ayumu-bekki/radio-terror/docs/navigator_decisions.md

# ナビゲーター設計 — 決定記録

`navigator_design.md` の設計判断の記録。**なぜそう決めたか**を実測値と
失敗の経緯込みで残してある。

- **現在有効な規範は [`adr.md`](adr.md)** に集約してある(N-\* の項目)。
  実装を変更するときはそちらを読む。ここは**根拠を確かめたいとき**に開く。
- ADR の各項目は「> 出典: NV 決定20」のようにこのファイルを指している。
- **覆った決定も削除しない**。「※ この決定は決定N で覆った」と追記して残す
  — なぜ一度そう決めたのかが分からなくなるため。
- 本文中の **§N は [`navigator_design.md`](navigator_design.md) の節**を指す
  (このファイルは元々そこの末尾にあった。2026-08-25 に分離した)。

> **この節は作業当時の記録**。当時存在したが**その後に採用を見送ったステージ**の
> 番号が出てくる(105/191/192/29x/39x)。現行のステージ一覧は
> `puzzle_stage_ideas.md` §2 を見ること。決定の中身自体は現在も有効。

## 決定記録

1. **キャラクター**: 4案(フクロウ/ヒバリ/アオサギ/ツグミ)を採用。
   ヒバリには「実は黒幕かもしれない」という含みを追加(§2.2。演出のみで
   ヒントの正確さは保つ)
2. **ツグミの音声**: エフェクト加工なし。素の中性声+スタイル指定のみ
3. **ヒントレベルの閾値**: ステージ経過時間を基本軸に質問回数・誤操作で前倒し。
   閾値はステージ予算に対する比率(**L2=25% / L3=50% / L4=75%**)で自動算出
   (実値は `scenario_design.md` §4.1)。比率0はそのレベルを無効にする指定で、
   ハードは `l4_pct = 0` として正解の直言を出さない
4. **正解の直言(L4)**: 残り時間ではなく**ステージ経過時間**で解禁し、
   ヒント段階(§3.2)の最終レベルとして統一
5. **コールサイン**: 採用するが常時フル形式にはしない。開始時・節目のみ名乗り、
   緊迫時はキャラごとの短縮形に崩す(§2.6)。
   ※ **この決定は決定107 で覆った**(2026-09-05)。「節目のみ」の指示により
   **ほぼ初回しか名乗らなくなった**ため、平時は毎回名乗る方針へ戻した。
6. **誤認識ポリシー**: 復唱確認+肯定待ちで担保(色名の日英併記はしない)。
   聞き返しは2回まで、以降ははい/いいえ形式に切り替え(§3.6)
7. **前倒しの制約**(実装時): 質問回数・誤操作による前倒しは、**無効化された
   レベルを飛び越えない**。ハードで誤操作してもL4(直言)には到達しない。
   また前倒しは経過時間による判定を下回らせない(§3.2)
8. **キャラクター知識の注入方法**(実装時): キャラシートはプロンプトの
   固定ブロック[B]として全文を渡し、口調・口癖・台詞例まで含める。
   短い要約では口調が安定しなかったため、場面別の台詞例を明記する方式にした(§3.3)
9. **ステージ知識の `procedure`**(実装時): 対話で誘導するステージ(101・103・202)
   向けに、ヒント指針とは別に「会話の進め方」を渡す項目を追加した
   (`scenario_design.md` §3.3)
10. **設定の外部ファイル化**(実装時): キャラクター定義とプロンプト固定ブロックを
    Goコードから **TOML** へ分離した(`navigator/`)。口調やプロンプトは実機で
    試しながら繰り返し調整する性質のもので、シナリオと同様に再ビルドなしで
    差し替えられる方が運用しやすいため。キャラクターは1人1ファイルとし、
    追加・差し替えをファイル操作で行えるようにした(§2・§3.3)
11. **表情タグの廃止**(実機確認時): 本文に `[calm]` のような角括弧タグを混ぜて
    TTS へ演技指示を渡していたが、**タグを含めると応答が不安定になる**ことが
    実測で判明した(通常2.6秒のところ、8回中2回が20秒超。最大21.7秒)。
    遅れたチャンクは radio-bridge 側で破棄され、ナビゲーターの音声が
    途中で途切れる原因になっていた。**ディレクターズノート方式**
    (プロンプト前置きの場面説明)へ変更(§4.1)。
    分割そのものは維持する — 実測で分割なしは発話開始が平均13.8秒
    (最大44.7秒)まで悪化し、遅延の外れ値は分割の有無に関係なく発生した

    **※ この決定は決定17で覆った。** 不安定さの原因はタグではなく
    一括受信だった(決定15)。**サンプル8回では両者を区別できなかった** —
    一括受信は入力と無関係に27%が10秒超になるため、
    「8回中2回」はタグ無しでも同程度に起きる頻度だった。
12. **分割送信をやめ、1パケットにまとめる**(実機確認時): 決定11では
    「分割そのものは維持」としたが、**逐次送信を取りやめた**。
    TTS の1チャンクが **58.97秒**かかった際、先に完成していた後続チャンクが
    1分近く滞留し、発話が丸ごと遅れる事象が出たため。
    分割送信は「先頭ができ次第すぐ流せる」が、裏返すと**1チャンクの遅延が
    発話全体を人質に取る**。全チャンクの PCM が揃ってから連結し、
    1回だけ Opus エンコードして1パケットで送る方式にした
    (`bridge_connection_design.md` §2 決定13)。
    **生成の並列化は維持**するので、待ち時間は「最も遅いチャンク」で決まる。
    決定11の実測(分割なしで平均13.8秒)は**逐次生成**での値であり、
    並列生成のまま送出だけまとめる今回の方式とは条件が異なる。
    レイテンシは増えるが、**出るときには必ず発話が揃っている**確実性を取った。

    **※ ここで残した「生成の並列化」も決定18で廃止した。** 発話が
    2文・60文字以内になり(決定14)、分割しても大半が1チャンクに
    収まるようになったため。
13. **API呼び出しのタイムアウト**(実機確認時): Transcribe / reply / TTS の
    各呼び出しに上限(`config.toml` で変更可)を設けた。
    従来は上流の ctx がプロセス終了まで生きており、**上限なく待っていた**。
    実測の正常値は Transcribe 2.8-3.1秒 / reply 1.1-1.2秒 / TTS 2〜4秒。
    無線は「無音のまま待たされる」のが最悪なので、待ち続けるより打ち切る。
    **TTS は 10秒・3回**(決定15でストリーミング化したため短く切れる)、
    Transcribe / reply は 20秒。
    併せて、10秒を超えた TTS 呼び出しは**プロンプト全文をログに残す**
    (`[gemini] TTS SLOW`)。原因追跡には入力が要るため。
    **打ち切りは発話全体の欠落を意味する**(決定16)ので、
    上限を短くする場合は必ず作り直しとセットにする。
14. **発話長の制限**(実機確認時): 出力ルールを「1〜3文」から
    **「2文以内・60文字以内」**へ厳しくし、雑談・回想で文を使わないよう明示した。
    実測で5文・69文字の発話が出ており、1発話が16〜19秒に達して無線を塞いでいた。
    原因は**キャラクター定義の台詞例が長かった**こと — フクロウの
    【ヒントの味付け】の例文が2文構成で、生成AIがその長さをそのまま写していた。
    プロンプトの数値だけでなく**例文の長さを短くする**ことが実効的なので、
    全キャラクターの台詞例を2文以内に揃え、「応答」の例を追加した。
    サーバー側でも文字数をログに出し、上限超過は WARN を残す
    (`navigatorMaxRunes`。プロンプトの数値と一致することをテストで担保)
15. **TTS の応答をストリーミングで受け取る**(実機確認時): 遅延の原因は
    **一括応答の待ち受け**だった。`GenerateContent` から
    `GenerateContentStream` に変えただけで**外れ値が消えた**。

    同一プロンプト15回の実測(`tts_latency_probe_test.go`):

    | 受信方式 | 中央値 | 最大 | 10秒超 |
    |---|---|---|---|
    | 一括 `GenerateContent` | 4.16秒 | **56.51秒** | **4回 (27%)** |
    | ストリーミング `GenerateContentStream` | 3.22秒 | **3.75秒** | **0回** |

    切り分けの経緯 — 当初は入力内容を疑った(決定11で角括弧タグが原因と
    結論づけた前例があるため)が、**実測で否定された**:
    - **入力内容は無関係**: 本番で19.01秒かかった本文を10回試すと 2.39〜3.59秒。
      逆に最も無害な平易文で46.96秒が出た。「どうぞ」の有無・三点リーダ・
      命令形・前置きの有無、いずれも差なし
    - **並行数も無関係**: 同時1本/2本/3本で中央値・最大値とも変わらず、外れ値ゼロ
    - **出力量とも無関係**: 遅い回も音声は5秒前後で一定。`MaxOutputTokens` は
      このモデルが受け付けない(30回中30回 400 INVALID_ARGUMENT)

    先頭チャンクは中央値0.79秒で届くが、**順次無線へ流すことはしない** —
    決定12で捨てた分割送信と同じ構造に戻るため。全チャンクを連結してから
    1つの Ogg にする。
16. **TTS が1チャンクでも欠けたら発話ごと見送る**(実機確認時): 以前は
    成功したチャンクだけ繋いで送っていたが、実運用で**尻切れの発話**が
    無線に出た(「私は見ている。」だけが流れ、続く指示が消えた)。
    不完全な指示は誤解を生むので、黙る方を選ぶ。
    ナビゲーターがその回だけ無反応になるため、WARN をログに残し、
    TTS の失敗をマネージャー画面の API 状況にも反映する。
    決定15で外れ値が消えたので発動機会はほぼ無いが、
    **タイムアウトを短くする判断はこの挙動とセット**で考える。
17. **表情タグを復活させる**(実機確認時): 決定11で廃止したタグを戻した。
    廃止理由「タグを含めると応答が不安定になる」が**実測で否定された**ため —
    不安定さの正体は一括受信で(決定15)、ストリーミング受信では
    タグ有無で差が無い(各10回、全条件で10秒超ゼロ、中央値2.87〜3.32秒)。
    読み上げ事故(「リリーブド」と発音する)も起きなかった。

    聴き比べの結果 **ノート+タグ > ノート単独 > タグ単独** だったので、
    ディレクターズノートは残したまま**併用**する(§4.1)。

    安全策として**語彙を6つに限定**し(`allowedTTSTags`)、一覧外のタグは
    サーバー側で落とす。プロンプトで指示しても生成AIが従うとは限らず、
    未知の語は演技として解釈されずそのまま読み上げられるため。
    実測では32発話すべてにタグが付き、**一覧外の語はゼロ**だった。
    キャラクター定義の台詞例にもタグを入れると出力が安定する
    (決定14と同じ理由 — 例文が実際の出力を決める)。
18. **チャンク分割をやめる**(実機確認時): 発話を句点で分割する処理
    (`splitAnswerForTTS`)を廃止し、**発話全文を1回の TTS 呼び出し**にした。

    分割の目的は段階的に失われていた:
    - 「できた順に送って最初の音を早く出す」→ 決定12で順次送出をやめた
    - 「生成の並列化」→ 決定14で発話が2文・60文字以内になり、
      大半が1チャンクに収まるようになった

    残ったのは**害だけ**だった。末尾の「どうぞ」(3文字)が必ず単独チャンクに
    切り出され、3文字の生成に2〜3秒のAPI往復を費やしていた
    (`mergeShortChunks` が先頭要素を結合対象にしないため)。
    失敗する機会も1つ増える。

    廃止に伴い `split.go` / `split_test.go` を削除し、
    `speakTTSChunks` を `speakTTS` (単一テキスト版) に置き換えた。
    ストリーミング受信で届く音声片の連結は TTS クライアント側に残っている
    (`tts.go` の `generateOnce`)。
19. **正解には「今は言うな」を併記する**(実機確認時): L3 のときに
    ナビゲーターが「次は緑色の線を切ってください」と**正解の色名を直言**した。
    プロンプトは「正解(あなただけが知っている): …緑色の線を切ること」を
    渡した上で、離れた位置のヒントポリシーで「言うな」と指示する構造だった。
    **答えを目の前に置いて言うなと指示しても引きずられる** —
    実際の発話は `answer` の文をほぼそのままなぞっていた。

    正解を渡す方針(§3.1)は維持し、**正解と同じ行に禁止を併記**する形にした。
    L4 未満では正解行の直後に「⚠ この正解をそのまま口に出してはいけません。
    現在は L<n> です」を付ける。実測で**色漏れ 0/24**(4キャラ×L1-L3×2種の正解色)。

    併せて 101 の進め方を「**プレイヤーに色を報告させてから指示する**」形に
    変えた。101 は正解の色だけが点灯するため、`hint_l3` の
    「点灯しているランプと同じ色」という言い換えが**実質色名と等価**で、
    区別が曖昧だった。ナビゲーターが先に色名を言うとプレイヤーは装置を見ずに
    従うだけになり、チュートリアルとしての意味も薄れる。
    修正後は全キャラが「光っているランプの色を教えろ」と尋ねる形になった。

    **※ その後、尋ねる形はやめた**(決定23)。色名を言わない原則は維持したまま、
    「光っているランプと同じ色の線を切れ」と直接指示する形にしている。
20. **`answer` は「読み上げる文」ではなく「照合の材料」として書く**:
    決定19 で「正解を目の前に置くとなぞられる」ことが分かっている。
    したがって `answer` に**そのまま読み上げると成立してしまう文**を
    書いてはいけない。205 速さくらべの初稿は
    「プレイヤーが白色を報告してきたら復唱して切らせてよい」と書いており、
    L1-L2 でなぞられると「白色ですか?」とナビゲーター側から色名を出しかねない
    形だった。**「プレイヤーの報告が白色と一致するかを照合に使うこと」**と、
    判定の指示として書き直した。

    合わせて **L4 でも色名を言えないステージがある**ことに対応した。
    203 ブループリントは色を言うとシートを読む工程が消えて謎が成立しないため、
    L4 でも端子番号しか言えない。L4 のプロンプトは `answer` を
    「そのまま伝えてください」と埋め込むため、`answer` 側に
    「L4 であっても色名は言わない」と書いたうえで、L4 ブロックにも
    **「但し書きがある場合はそれが優先。但し書き自体は読み上げない」**を
    追記した。回帰は `TestL4RespectsStageLevelRestriction` と
    `TestHintPolicyBelowL4NeverEmbedsAnswer` が押さえている。

21. **意味の通らない報告は復唱せず聞き返す**(実プレイで発覚):
    音声認識が「ダイヤルを0に」→「ダイヤルを**音量**に」、
    「3に合わせました」→「**レディニュー**」のように誤変換したとき、
    ナビゲーターが「音量ですね、了解です!」「レディニュー、オッケーです!」と
    **そのまま復唱して先へ進んでいた**。プレイヤーは誤りが伝わったことに
    気づけず、実際の位置とナビゲーターの認識がずれたまま進行する。

    原因は §3.4 のルールの優先順位が曖昧だったこと。「報告は復唱して確認」と
    「聞き取れない場合は聞き返す」が併記されており、生成AIは前者を選んでいた。
    **「その場面で成立しない報告(色でも数字でもない語)は聞き取れなかった
    ものとして扱い、復唱せずに聞き返す」**を明示的に追加した。

    実プレイのログでは、ダイヤル位置の報告が全4回中2回誤変換されていた。
    無線 + 特小の音質では日常的に起きるため、聞き返しは例外処理ではなく
    **通常運転**として設計する。

22. **装置を見ても分からない情報は L1 で伝える**(実プレイで発覚):
    192 シグナルで、ナビゲーターが「3つのボタンを決まった順番で押せ」と
    言うだけで**色を一切教えず**、プレイヤーが「順番がよくわからないんですけど」と
    尋ねる往復が続いた。開始から約1分、押す色が伝わらなかった。

    原因は `hint_l1` が「ボタンを決まった順番で押す必要があることを伝える」と
    書かれていたこと。ボタンの並びは**装置に一切現れず、ナビゲーターしか
    知らない**ため、伏せるとプレイヤーは観察でも推理でもたどり着けない。
    「段階的に明かす」は**推理できる情報**に対してのみ意味を持つ。

    同じ欠陥が 201 復唱・393 二重復唱 (ボタン列)、206 綱渡り
    (危険なダイヤル位置) にもあった。206 綱渡り は知らずに踏むと**即爆発**するため、
    伏せるのは謎ではなく事故になる (`procedure` は先に警告する前提で
    書かれており、L1 と矛盾していた)。

    **ヒント段階で調整するのは「一度に何色まで言うか」であって、
    言うか言わないかではない。** 102 は L1 で1色目、L2 で残りを1色ずつ、
    L3 で通し読み。201/393 は L1 で列を読み上げる (393 二重復唱 の2周目は
    「覚えていられるか」が謎なので伏せたまま)。206 綱渡り は L1 で危険位置を警告する。

    あわせて `HintPolicyText` の共通文に**「指針が優先」**を明記した。
    「レベルを超えて色や番号を直言しない」という一般則だけがあると、
    生成AIはステージ側の指針より一般則を選んでしまう。
    回帰は `TestUnobservableInfoInProcedure` が押さえている。

23. **101 の手順を短縮する**(実プレイで発覚): チュートリアルに
    **約3分半**かかっていた。原因は2つ。

    **(a) 経由が2つあった。** `0 → 3 → 5 → 2` と4手順を踏ませており、
    1手順ごとに無線の往復が発生する(音声認識の失敗で聞き直す回もある)。
    経由を増やしても「報告して指示を受ける」という学びは変わらないので、
    `via2` を廃止して `0 → via1 → final_rotary` の3手順にした。
    あわせて `final_rotary` から 0 を除外した — 「0に戻す → 経由 → 0」と
    出発点へ戻るだけの往復になるため(抽選の15%で発生していた)。

    **(b) 最後に色を報告させていた。** ダイヤルが合ったあとで
    「光っているランプは何色か」→(報告)→「その色の線を切れ」と
    **1往復増やして**いた。決定19 で入れた形だが、実プレイで見ると
    最後の確認が冗長だった。**やることを最初にまとめて伝え**
    (「ダイヤルを合わせてから、光っているランプと同じ色の線を切る」)、
    ダイヤルが合ったら「光っているランプと同じ色の線を切れ」と
    そのまま指示する形へ変更した。

    ゴールを先に示すとプレイヤーはダイヤル操作中に自分でランプを見て
    準備できるため、**装置を見る**というチュートリアルの目的は保たれる。
    色名を言わない原則(決定19)も維持している。
    回帰は `TestTutorialStageNeverNamesCutColor` が押さえている。

24. **具体的な数字の指示を演出説明より優先する**(実プレイで発覚):
    決定23 で 101 の `procedure` に「最初にゴールを伝える」を足したところ、
    第一声が「まずダイヤルを回し、光っているランプと同じ色の線を切れ」となり、
    **どこへ合わせるかの数字が消えた**(46文字)。

    原因は出力ルールの**2文・60文字以内**。ゴールの説明を前に置くと、
    生成AIはその範囲に収めるために**具体的な数字を落とす**。
    説明と指示が競合したとき、削られるのは指示のほうだった。

    `hint_l1` / `procedure` を「**必ず数字で位置を言う。ゴールの説明で数字が
    押し出されるくらいなら数字だけ言う**」と優先順位を明示する書き方に変えた。
    短い発話に複数の要素を詰めさせるときは、**何を先に削ってよいか**まで
    指針に書く必要がある。回帰は `TestTutorialGivesConcreteDialPositions`。

25. **ディレクターズノートに場面を書かない**(実運用で発覚):
    TTS が生成した音声の**先頭に、ログに無い「プレイヤーの応答」らしき音声**が
    混入した。原因は前置きの書き方 — 「プレイヤーの報告に応じる場面。」のように
    **会話の状況**を書いていた。

    TTS は音声専用エンジンではなく**生成モデル**なので、場面を説明されると
    その場面全体を演じようとし、**応じる相手の発話まで自分で作って先に読み上げる**。
    「次のセリフを読み上げてください」で本文を限定していても、前置きが
    台本指示に見えるため効かない。

    ノートを**読み方の指定だけ**に書き換えた
    (「プレイヤーの報告に応じる場面。事務的すぎず、自然な受け答えで。」→
    「事務的すぎない、自然な受け答えの調子で。」)。
    「場面」「プレイヤー」「相手」「直後」「瞬間」といった状況を示す語は使わない。
    回帰は `TestDirectorNotesDescribeDeliveryOnly` が押さえている。

    タグが「リリーブド」と読み上げられた事故(決定11)と同じ構図で、
    **本文以外の要素を音声化してしまう**傾向はこのモデルで繰り返し起きている。

26. **ステージ知識が無いときは操作を促させない**(実運用で発覚):
    解除成功の直後に、ナビゲーターが
    **「あと60秒!もう一本、赤の線を切ってください!」**と、
    既に解除済みの装置へ**存在しない指示**を出した。

    原因は最終ステージのクリア処理。デバイスは最後の1本を切ると
    `stage_cleared` に続けて `defused` を送るが、サーバーは `stage_cleared` で
    「次の課題へ進む」と発話させていた。次のステージが無いため
    プロンプトにステージ知識が入らず、**指示だけが残って課題を捏造**した。
    進行表示も「3 / 2 番目の課題」と、あたかも課題が残っているように見えていた。

    3層で塞いだ:

    - **最終ステージのクリアでは発話しない**(完了の演出は直後の `defused` が担当)
    - ステージ知識が無いときのプロンプトに
      **「今は指示する課題がありません。装置の操作を促してはいけません」**を明記
    - 範囲外の進行表示を「全N課題を完了」に変更

    教訓は、**指示だけあって材料が無いプロンプトは捏造を生む**こと。
    材料が無い場合は「何もするな」を明示的に渡す必要がある。
    回帰は `TestFinalStageClearedDoesNotSpeak` と
    `TestPromptWithoutStageForbidsOperations`。

27. **色漏れには4つの経路がある**(全ステージ横断シミュレーションで発覚):
    有効な24ステージすべてを文字のみで交信させ(`-simulate`。§7)、
    L1→L4 の5往復・計120発話を採取したところ、**12件の色漏れ**が出た。
    決定19・20 で潰したのは「`answer` をなぞる」経路だけで、
    実際には**別の4経路**が残っていた。

    **(a) 読み上げてよい色名に正解色が混ざる。** 102/104/201/393 は
    ボタン列を読み上げる仕様だが(決定22)、押下色と `cut` が
    独立に抽選されるため**列に正解色が入る**。300シードで測ると
    201/393 で 65%、102 で 49%、つまり過半のセッションで
    「順番は緑、青、**赤**、青、**赤**だ」と正解色を音にしていた。
    キャラクターを変えても再現するので、生成AIの逸脱ではなく
    **テンプレートの構造欠陥**。押下色に `exclude = ["${cut}"]` を入れて
    分離した(102 ホールド&カット が `hold` と `cut` を分けているのと同じ理由)。

    **(b) 禁止を括弧書きの末尾に添えると読み落とす。**
    「〜と手順を教えてよい(切る線の色は言わない)」という書き方をしていた
    104/207/209/303 で、L1-L3 の直言が出た。**禁止は独立した文**にし、
    併せて「点灯しているランプは1つだけなので『光っているランプと同じ色の線』
    と言えば伝わる」と**代替の言い方**まで書くと安定した。
    禁止だけを渡すと、生成AIは何と言えばよいか分からず元の表現に戻る。

    **(c) `hint_l3` が「切る線も伝えてよい」と許可していた。**
    201/393 は列を読み上げたあと「押し終わったら切る線も伝えてよい」と
    書いており、**禁止どころか許可していた**。これらは正解色だけが点灯する
    (102 と同じ形)ので、「光っているランプと同じ色」で一意に決まり
    伏せても手詰まりにならない。`answer` も 205 速さくらべ と同じ
    「照合の材料」形式へ書き直した(決定20)。

    **(d) プレイヤーが言っていない色を補って復唱する。**
    「ランプが1つ光っています」という**色名を含まない報告**に対し、
    「光っているのは赤だな、了解」と正解色を補って返していた
    (101/209/303 で発生)。生成AIはこれを**復唱**と認識しているが、
    実際には**答えの提示**。§3.4 の共通ルールに
    「復唱は相手が言ったことだけ。色名を口にしてよいのは
    プレイヤーがその色名を先に言ったときだけ」を追加し、
    違反例(「光っているのは赤だな」)まで具体的に列挙して塞いだ。

    **誤報告への返し方も書く必要がある。** 205 速さくらべ の `hint_l3` は
    「報告が正しければ確認して切らせてよい」とだけ書いており、
    **間違っていた場合の言い方が未定義**だったため、生成AIが
    「黄色だな、了解。**赤**と見比べろ」と正解色を出して比較させた。
    分岐がある指針は**両方の枝を書く**。

    合わせて **`session_start` の第一声が指針に従っていなかった**。
    206 綱渡り は危険位置を L1 で伝える設計(決定22)なのに、第一声は汎用の
    「まず光っている色を言え」で、プレイヤーが自分から尋ねるまで
    危険位置が伝わらなかった。207 は違反すると**即爆発**するため、
    訊かなければ踏むまで伝わらないのは事故になる。トリガー指示に
    「指針が具体的な情報を伝えるよう指示している場合は第一声に必ず含める。
    尋ねられるのを待ってはいけない」を追加した。

    **切る線の色が装置に現れないステージがある。** 191 は点灯色が
    「数」を表すだけで `cut` と独立に抽選されるため、実測で**45%**の
    セッションで正解色のランプが消えている。391 暗転は5色すべてが
    同じように点滅し、`cut` は表示と無関係。どちらも伏せると
    プレイヤーは色を知る手段が無く手詰まりになるので、決定22 の原則どおり
    **L1 から伝える**設計にした(`answer`/`hint_l1` に明記)。
    191 はそもそも「色を言うな」の記述すら無く、意図が曖昧だった。

    修正後の再実行で **24ステージ中23が所見なし**、残る1件も
    誤報告への返し方を書き足して解消した(120発話・平均31.6文字・
    タグ違反0・長さ超過0)。

28. **キャラクターは「見ているもの」で分ける**: フクロウとアオサギが
    **感情を抑え・上から・断定的に指示する**という3軸すべてで同型になっており、
    違いは言葉づかい(乱暴な男性語 / 丁寧な女性敬語)だけだった。
    無線越しの短い発話では性別と語尾しか手がかりが残らず、機能まで
    重複していた(どちらも「落ち着かせる役」「誤操作を受け止める役」)。

    アオサギを**装置だけを見る**姿勢へずらし、**落ち着かせる役は
    フクロウへ明け渡した**。安心は励ましではなく「一致しました」という
    判定の明快さで与える。併せて4人を「何を見ているか」の4象限
    (心理 / 同じもの / 装置 / 全体を外から)で整理した(§2)。
    口調だけを書き分けても同じ役に収束するため、**追加時はこの象限で
    重ならないかを先に見る**。

    **確度をつける対象は限定する**。分析官らしさとして「おそらく赤、
    確度8割」と語らせる案は採らなかった。プロンプトには正解が入るため
    **知っている情報を知らないふりで語る**ことになり、断定へ戻るか、
    確率つきで色名を漏らすか(決定27 の色漏れ経路)のどちらかに壊れる。
    確度をつけてよいのは**プレイヤーの報告**だけとした — 無線・STT・
    見間違いで実際に不確かなため嘘にならず、§3.6 の復唱確認とも噛み合う。

    **「わずかに/稀に」という程度指定は使わない**。アオサギの
    「成功時だけわずかに声が温かくなる」は加減が守られず毎回温かくなって
    フクロウへ戻るため、**完全に抜いた**。同じ理由でツグミの口癖
    (「ワタシハ、ミテイル」を稀に出す案)も廃止している。
    生成AIに頻度の微調整を任せると、毎回出るか全く出ないかに寄る。

29. **ツグミの口調から命令形を外す**: 「色を告げよ」「4へ回せ」という
    文語の命令形が堅苦しく、キャラシートに書いてある
    「真剣なのかふざけているのか分からない」が台詞側で表現できていなかった。
    **手順は独り言のように呟き(命令の圧を消す)、反応は軽く受け流す**
    配分にした。普段の呟きで距離を作り、そこへ稀に軽さを差すことで
    「何を考えているのか分からない」印象になる。常に軽いと単に軽薄になる。

    TTS スタイルの「ピッチと速度を一定に保った機械的な読み方」も
    併せて外した(**捨てた口癖と同じ方向を向いており、軽さと衝突する**)。
    声そのもの (`Iapetus`) は据え置きなので、混線側のボイス重複回避
    (`docs/crosstalk_audio_generation.md`)には影響しない。

    **呟きにしても情報の正確さは落とさない**。伝える内容・伏せてよい情報は
    他キャラと同じで、口調をぼかした結果ヒントまで曖昧になる方向へ
    引きずられないよう §2.4 に明記した。

30. **切る線の色を教えるだけになるステージは置かない**: 決定27 で
    **191 いくつ光ってる?** と **391 暗転** は「切る線の色が装置に現れない」
    ため L1 から色を伝える設計にしたが、**両ステージを無効化した**
    (`.toml.disabled`)。

    決定22 の原則(装置に現れない情報は伏せない)に従うと色を教えるしかなく、
    そうすると**ナビゲーターが色を告げるだけの工程**が謎の隣に居座る。
    102/201/393 のボタン列も「装置に現れないから教える」点は同じだが、
    あちらは**教わった内容を覚えて操作する**難しさが残る。
    191/391 の色は教わった時点で何も残らない。

    構造的な違いは**正解の色が謎の答えになっているかどうか**。
    104 早い者勝ち や 295 仲間はずれ は「速い方」「仲間はずれ」を見つけること自体が色の特定で、
    観察が答えに直結する。191 の点灯色は**数を作るための材料**でしかなく
    `cut` と独立に抽選される(実測で45%は正解色が消灯)。
    391 暗転 も5色すべてが同じように点滅し `cut` は表示と無関係で、
    謎は「全消灯の瞬間を捉えること」だけ。

    **新しいステージを足すときは `cut` が謎の答えとして導けるかを先に見る**。
    導けないなら、色は別途伝えるしかなく、その伝達は謎にならない。
    ステージ数には余裕がある(無効化後もイージー5・ノーマル11・ハード6で、
    テンプレートの要求を満たす)。

31. **ステージ知識に口調を持たせない**(アオサギ・ツグミのシミュレーションで発覚):
    決定27 までの検証はフクロウ1人で回しており、**キャラクター依存の問題を
    取りこぼしていた**。アオサギ(敬語)とツグミ(命令形を使わない)で
    全22ステージを回したところ、フクロウでは出なかった2種類の崩れが出た。

    **(a) 命令形の例文を写す。** `procedure` / `hint_*` に
    『光っているランプと同じ色の線を切れ』のような**命令形の例文**を書いていたため、
    「命令形を使わない」と明記してあるツグミがそのまま写した(110発話中4件)。
    ステージ知識は4キャラ共通なので、**特定の口調を含めてはいけない**。
    指示の内容だけを「**「光っているランプと同じ色の線」**という言い方で伝える」
    と書き、語尾はキャラシートに任せる形へ直した(修正後は0件)。

    皮肉なことに、この例文は決定27 (b) で「禁止だけでなく代替の言い方も書く」と
    して**私が足したもの**だった。代替表現を示すのは正しいが、
    **例文は口調を持つ**ことに注意が要る。

    **(b) 敬語は字数を食う。** アオサギは平均38.9文字(フクロウ31.3)と
    上限60に張り付いており、伝える要素が増えると**超過した**
    (304 我慢比べで74文字)。原因は複数の要素を1発話に詰めたこと。
    決定24 と同じ構図で、`procedure` に「**1回の発話で伝えるのは1つだけ**にし、
    返答を待ってから次へ進む」と順序を明示して解消した(103・394)。
    キャラシート側にも「判定 +『次にやること1つ』で切る」を追記している。

    **口調の違いは字数の違いでもある**。60文字は敬語キャラにとって
    フクロウほど余裕がないため、**要素の多いステージは手順の分割を
    `procedure` に書く**必要がある。

    **ただし超過は完全には消えない。** 分割指示を入れたあとも、
    アオサギは実行のたびに 0〜2件の超過を出す。3回の実測で分布は
    **中央33文字・90%点47文字**と安定しているが、**尾だけが跳ねる**
    (最長 52 / 54 / 68)。超過するステージは毎回入れ替わるので、
    特定ステージの欠陥ではなく**生成のばらつき**。
    個別に潰し続けてもきりがないため、ここで止めている。

    実害は「その発話が数秒長く無線を塞ぐ」ことで、
    `navigatorMaxRunes` の WARN ログで運用中に検知できる(決定14)。
    **超過をゼロにしたい場合は上限そのものを見直す**方が筋がよい —
    敬語で「判定 + 指示」を言うと 60 文字は元々きつい。

    検証は**フクロウだけでは足りない**。少なくとも敬語(アオサギ)と
    非命令形(ツグミ)の2人を回す。修正後は3キャラとも
    **色漏れ0・タグ違反0**、命令形の写しは 4件 → 0件になった。

32. **課題の入り口は必ず「ランプはどうなっている?」から**(交信ログのレビューで発覚):
    ログを通して読むと、ナビゲーターが**装置を見ないうちから手順を話し始めて**いた。
    105 はいきなり点滅の速さの話を始め、201/204/205/206/209/303/393/394/304/305 も
    ランプの状態を尋ねずに指示へ入っていた。103 に至っては
    **プレイヤーのほうから「ダイヤルはどこですか」と訊いていた** —
    本来ナビゲーターが伝えるべき情報を、プレイヤーが探りに来ている。

    これでは**無線で状況を伝え合う体験**が成立しない。
    プレイヤーは装置を見ずに指示へ従うだけになり、
    「見て、報告して、指示を受ける」という本作の中心が消える。

    原因は `hint_l1` の書き方だった。多くが
    「点滅の速さに**気づかせる**」「2つ光っていることを**確認させる**」と
    **観察の結果**を書いており、生成AIはそれを「自分が言う内容」と解釈していた。
    **「報告させる」と動作で書く**必要がある。
    全ステージの `hint_l1` を
    「まず『ランプはどうなっている?』と尋ね、状態を報告させる。
    『…』という報告を受けてから〜」の形に統一した。

    **共通ルールとトリガー指示にも入れる。** ステージ側だけだと
    課題をまたいだときに効かない:

    - `role` に「課題の第一声はランプの状態を尋ねることから始める。
      **装置の状態を知っていても、プレイヤーが報告するまで知らないふりをする**」
    - `session_start` を「名乗ってからランプの状態を尋ねる」へ
    - `stage_cleared` を「**短く称賛し、続けてランプの状態を尋ねる**」へ。
      従来は「次の課題への指示を出してください」だったため、
      **課題が変わった瞬間に手順から入って**いた

    **装置を見ても分からない情報 (決定22) とは両立させる。**
    102/201/393 のボタン列、206 綱渡り の危険位置は第一声で伝える必要があるが、
    伝えたうえで**ランプの確認も併せて行う**
    (「ランプはどうなっている? 順番は白→黄→青→白→緑だ」)。
    どちらか一方ではない。

    回帰は `TestStagesAskForLampReportFirst` (全ステージの `hint_l1` が
    報告を求める形か) と、シミュレーションの `no_observation_first` 検査
    (第一声・課題突破直後にランプへ言及しているか) が押さえている。
    シミュレーション台本にも `stage_cleared` のターンを追加した —
    **課題の切り替わりは台本に無く、検証できていなかった**。

    **台本のターン順は実際に起こりうる並びにする。** 追加時に
    `session_start` の直後へ `stage_cleared` を置いてしまい、
    「まだ何も突破していないのに『やりましたね、ナイスです!』」という
    **実機では起こりえない並び**を検証していた(ログのレビューで発覚)。
    発話自体は与えたイベントに対して正しく、ゲーム側の不具合ではない。
    `stage_cleared` は課題を解いたあとにしか届かないので、
    **台本でも最後に置く**。トリガーを足すときは
    「その順番が実機で起こりうるか」を確かめること。

33. **紙資料には区画見出しを印刷する**(交信ログのレビューで発覚):
    301 LED照合 (当時は「運命の二択」) で、ナビゲーターが
    「シート上の記号の数を数えてください」と**説明的に**指示していた。
    無線越しでは「どこを見るのか」が伝わりにくく、発話も長くなる。

    ミッションシートを区画に分け、**「区画A」(記号) /「区画B」(数字)** を
    大きく印刷する。ナビゲーターは**「区画Aを見ろ」と一言で**指示できる
    (`printed_materials.md` §3.2.1)。

    区画見出しは抽選値から機械的に導出する。
    分岐と別々に人手で書くと食い違うため。

    **2026-08-23 に 202 を LED照合へ差し替えた**ため、記号/数字の分岐と
    `derive = "sheet_section"` は廃止した。**資料番号で一言で指す**という
    この決定自体は生きており、新 301 LED照合 も `${sheet_codebook}` を呼称で参照する。
    回帰は `TestCodebookStageResolves`。

    **配線色の記号 (A-E) とは別物**。色記号は紙に印刷しない方針
    (`printed_materials.md` §1.1) なので紙面上では衝突しないが、
    運営が混同しないよう**必ず「区画」を付けて呼ぶ**。

34. **60文字の上限はキャラクターによって余裕が違う**(ヒバリのシミュレーションで確認):
    最後の未検証キャラだったヒバリを回したところ、**平均39.6文字**と
    4キャラで最も長かった(フクロウ28.3・アオサギ33.7・ツグミ33.4)。
    「〜です!」「〜してください」という語尾に加え、
    **復唱 + 説明 + 指示を1文に詰める**癖があるため。

    キャラシートに「復唱 +『次にやること1つ』で切る」を追記したが、
    **効果は限定的**だった(平均 39.6 → 38.7、中央 40 → 39、超過 2件 → 1件)。
    台詞例は44/30/27文字と上限内なので、決定14 の「例文が長さを決める」
    経路ではない。**口調そのものが持つ字数**なので、プロンプトでは削りきれない。

    設計上の含意は2つ:

    - **上限60文字は口調に対して一律ではない**。フクロウを基準に決めた値だが、
      ヒバリには中央値で既に2/3を使ってしまう。超過をゼロにしたいなら
      **上限そのものを見直す**か、**キャラクターごとに変える**(決定31と同じ結論)
    - 検証は**4人とも回す**。ヒバリは字数の最悪ケースを出すので、
      新しいステージを足したときの「詰め込みすぎ」はここで最初に現れる

    **黒幕の匂わせ(§2.2)は無害だった。** 「作った人はきっと最後に赤を
    残したかったんです」という発言が2回出たが、いずれも **L4**
    (正解の直言が許可される段階) で、ヒントの正確さは損なわれていない。
    「演出に限定し、指示内容は常に正確」という設計が実測で確認できた。
    L1-L3 での色漏れはゼロ。

35. **「課題突破」と「解除完了」を取り違えさせない**(交信ログのレビューで発覚):
    ヒバリが**ステージを1つ突破しただけ**の場面で
    「**解除されちゃいました……あっ、できましたね!おめでとうございます!**」と
    発話していた。これは装置を解除しきったとき (`defused`) の台詞で、
    まだ次の課題が残っている場面では違和感がある。
    プレイヤーが「終わった」と誤解する危険もある。

    原因は2つ重なっていた:

    - **キャラシート**: ヒバリだけが「(解除成功時)」の台詞を持つが、
      それが**黒幕の匂わせの例**の中に並んでおり、`【台詞例】` の
      「クリア: ナイスです!その調子!」とは離れた位置にあった。
      「解除成功時」という但し書きだけでは、**最終解除に限る**と伝わらない
    - **トリガー指示**: `stage_cleared` は「課題を突破しました」とだけ書いており、
      **装置がまだ解除されていない**ことを明示していなかった

    両方を直した。キャラシート側は「**危険物をすべて解除しきった最後の一回だけ**」
    と条件を書き、「課題を1つ突破しただけの場面では絶対に使わない」と併記。
    トリガー側は `stage_cleared` に
    「**装置はまだ解除されていません** — 次の課題が残っています。
    完了を意味する言い方はしないでください」を、
    `defused` に「**すべて解除しきりました** — 課題を1つ突破しただけの場面では
    ありません」を追加し、**2つの場面を明示的に区別**した。

    教訓は、**似た場面のトリガーは互いに「そうではない方」を明示する**こと。
    片方だけを説明すると、生成AIは手持ちの台詞から近いものを選んでしまう。
    回帰はシミュレーションの `premature_completion` 検査
    (`stage_cleared` の発話に「解除できました」等が出ていないか) が押さえている。

36. **カウントダウンはナビゲーターが名乗ってから始める**(実運用の指摘):
    開始申告をすると**返答が無いままいきなりカウントダウンが始まって**いた。
    プレイヤーは誰と交信するのかも、始まったことも分からないまま時間が減る。

    原因は順序。`StartSession` は `session_start` を先に送っており
    (= デバイスのカウントダウン開始)、ナビゲーターの発話はその**後**だった。
    生成 + TTS に数秒かかるので、その間ずっと無言で時間だけが進む。

    **発話 → 鳴り終わり → 5秒 → カウントダウン開始** の順に変えた
    (`announceReady`)。新しい `session_ready` トリガーで応答し、
    `countdownStartDelay` (5秒) を置いてから `session_start` を送る。

    **この2つは交信相手が違う。**

    | | 相手 | 内容 |
    |---|---|---|
    | `session_ready` | **マネージャー** | 名乗り+「待機完了」だけの簡素な応答 |
    | `session_start` | **プレイヤー** | 改めて名乗り、**安心させる一言**を添えてランプの状態を尋ねる |

    `session_ready` は**簡素にする**。当初は CoreID と難易度を復唱させたが
    (音声認識の取り違え対策)、マネージャーは自分が申告した内容を知っており、
    聞きたいのは「伝わって準備ができたか」だけ。無線は短いほどよい。
    相手がマネージャーなので、ここで**装置の操作を促してはいけない**。

    相手が変わるので `session_start` では**改めて名乗る**。実測:

    > (→M)「こちらフクロウ。待機完了。どうぞ」(16字)
    > (→P)「こちらフクロウ。この手の装置は何百と見てきた、落ち着いていけば必ず解ける。
    >       ランプはどうなっている? どうぞ」(53字)
    >
    > (→M)「こちらツグミ。待機完了。」(12字)
    > (→P)「ツグミだ。……ああ、見えてる。大丈夫、こういうのは慣れてるから。
    >       ランプはどうなっている? どうぞ」(48字)

    **プレイヤーへの第一声は事務的にしない**(決定37)。

    設計上の要点が3つある:

    - **同期で待つ。** 非同期にすると発話とカウントダウン開始が競合し、
      「準備完了」と言っている最中に時間が減り始める
    - **鳴り終わりから数える。** `Speak` が返るのは bridge へ**送出**した
      時点で、再生はこれから。混線と同じ `BusyFor` で実際の再生時間を足す
    - **発話に失敗しても開始する。** 無線が無言になるのは痛いが、装置の前に
      プレイヤーが立っている以上、開始できない方が困る (§9 の方針と同じ)。
      このとき猶予も待たない (無用に遅らせない)

    「ランプはどうなっている?」は `session_start` が担当する(決定32)。
    時間が動く前に報告させると往復が噛み合わないため、
    `session_ready` では操作を促さない。

    回帰は `TestAnnounceReadyWaitsBeforeCountdown` と
    `TestAnnounceReadySurvivesSpeakFailure`。

37. **プレイヤーへの第一声は事務的にしない**(実運用の指摘):
    決定36 で開始フローを2段階にしたが、プレイヤーへの第一声が
    「こちらフクロウ。ランプはどうなっている? どうぞ」と**用件だけ**だった。
    目の前で危険物が起動した瞬間に、無線の向こうから淡々と質問が来る。
    **味方がいる感じがしない。**

    ここはゲームが始まる場面であり、**キャラクターの第一印象が決まる**場面でもある。
    `session_start` に「**名乗ったあと、『自分がついているから大丈夫だ』という
    趣旨の一言をキャラクターらしく添える**」を追加した。

    **安心のさせ方はキャラクターごとに変える**(決定28 の「何を見ているか」に沿う):

    | キャラ | 安心のさせ方 | 実測 |
    |---|---|---|
    | フクロウ | 経験で請け合う | 「この手の装置は何百と見てきた、落ち着いていけば必ず解ける」 |
    | アオサギ | 判定の明快さ | 「あなたが不安になる必要はありません、私がすべて把握しています」 |
    | ツグミ | 温度の低い距離感 | 「……ああ、見えてる。大丈夫、こういうのは慣れてるから」 |
    | ヒバリ | 応援 | 「私がついているから大丈夫です!」 |

    **キャラシートの「開始」例も直した。** 決定14 のとおり
    **例文が実際の出力を決める**ため、指示だけ足しても例が用件だけのままだと
    そちらに引きずられる。ヒバリ以外の3人は例が機能的な質問だけだった。

    **この発話に限り 80 文字まで許容する。** 名乗り + 安心させる一言 + 質問の
    3つは 60 文字に収まらず、詰めると必ず安心させる一言が削られる(決定24 と
    同じ構図 — 短い発話に要素を詰めると、削られるのは後から足したほう)。
    開始の一言は会話の途中ではないので、多少長くても無線を塞がない。
    実測は 43〜58字で、結果的に 60 字にも収まっている。
    ただし**質問は必ず入れる**(長さが厳しければ安心させる一言を短くする)
    — 観察を促さないと決定32 が崩れるため。

    `navigatorMaxRunes` (60) は**変えていない**。WARN を出すだけの上限で、
    ここを緩めると全発話が長くなる。緩めるのはこのトリガーの指示の中だけ。

38. **60文字は目安であって失格条件ではない**(方針決定):
    決定31・34・37 で3回とも「超過をゼロにしたいなら上限を見直すか」という
    論点に到達した。**上限は 60 のまま、緩い条件として運用する**と決めた。

    理由は、**締めると削られるのが情報のほう**だから。決定24 で
    「説明を前に置くと数字が押し出される」ことが分かっており、
    決定37 でも安心させる一言を入れると 60 字に収まらなかった。
    超過ゼロを目標にすると、危険の警告・押す順番・合わせる数字といった
    **伝えないと詰まる情報**が先に消える。無線が数秒長く塞がるより害が大きい。

    実装はもともとこの形になっている(`navigatorMaxRunes`):

    - **切り詰めない。** 途中で切ると指示が欠けて誤解を生む
    - **発話を止めない。** 長くても流す
    - **WARN をログに残すだけ。** プロンプトが効いているかを運用中に見る

    プロンプト側も「60文字以内**を目安に**」へ変え、
    「**収めるために必要な情報を削らないこと**」を明記した。

    シミュレーションの検査も変えた。目安超えは**所見にせず集計だけ**にし
    (「目安超え: 5/154 発話 (3%)」)、`excessiveRunes` (90字) を超えたときだけ
    `excessive_length` として挙げる。数字を超えただけで所見が並ぶと、
    本当に見るべき色漏れ・観察抜けが埋もれる。

    実測の分布 (22ステージ・各150発話前後):

    | キャラ | 平均 | 中央 | 最長 |
    |---|---|---|---|
    | フクロウ | 29.5 | 28 | 57 |
    | ツグミ | 30.9 | 30 | 71 |
    | アオサギ | 31.7 | 30 | 81 |
    | ヒバリ | 38.2 | 37 | 67 |

    **中央値はどのキャラも 28〜37 字**で目安の半分程度に収まっており、
    長くなるのは要素が重なる場面 (206 綱渡りの第一声など) に限られる。
    緩い条件で運用して問題ない水準と判断した。

39. **1回のシミュレーションで「直った」と判断しない**(394 の修正で発覚):
    ヒバリで 394 三点確保の色漏れが出たため `answer` と `hint_l3` を直し、
    **394 だけを1回ずつ4キャラで回して「OK」と報告した**。
    ところが全22ステージを通しで回すと**同じ 394 でまた漏れた**。
    1回のパスは「たまたま出なかった」だけだった。

    生成AIの出力はばらつくので、**変動しやすい所見 (色漏れ・字数) は
    複数回まわして確認する**。とくに:

    - 修正が効いたかを見るときは、**同じステージを2回以上**
    - 全体の傾向を見るときは、**キャラクターを変えて**(決定31)

    2度目の漏れは決定27 (d) の「プレイヤーが言っていない色を補う」経路だった。
    `answer` を照合形式にするだけでは足りず、**各ヒントレベルにも
    「色名を補ってはいけない」を書く**必要がある (209/303/304 と同じ形)。
    修正後は4キャラ×2回、すべて所見なしを確認した。

40. **正解の色名は L4 未満でプロンプトから伏せる**(色漏れを構造で断つ):
    決定19 以降「正解を渡したうえで言うなと指示する」形を取ってきたが、
    実測で **616発話中1件**残った。決定27 で4経路を潰し、各ステージの
    `hint_*` にも禁止を書いたうえでの1件で、**指示だけでは消えない**と判断した。

    **目の前に無い語は言えない。** L4 未満では `answer` の正解色を
    `redactCutColor` で伏せ字 (`◯◯色`) に置き換えてからプロンプトへ入れる。

    - **伏せるのは切る線の色だけ。** 押すボタン・押さえるボタンの色は残す
      (102 のボタン列など、伝えないと手順が成立しない)
    - **色名の形は残す** (`◯◯色`)。単に消すと文が壊れて進め方が読めなくなる
    - **警告は併記したまま** — 伏せ字から色を推測して言うのを防ぐ
    - **L4 はそのまま渡す**。直言してよい段階なので伏せる意味がない

    `answer` に色を書く運用は**変えない**。`scenario_validate.go` が
    「answer が cut に言及しているか」を検証しており、これは
    ナビゲーター知識とデバイスの食い違いを防ぐ要 (最も致命的なバグ)。
    **検証には必要だが、プロンプトへ入れる必要はない** — この分離が要点。

    回帰は `TestPromptRedactsCutColorBelowL4` (20シードで L1-L3 に色名が
    入らないこと) と `TestRedactCutColorKeepsOtherColors` (伝えてよい色は残ること)。

41. **先出しする情報も「報告のあと」に回す**(実プレイのレビューで発覚):
    201 復唱で、第一声が
    「ランプはどうなっている? **順番は白→黄→青→白→緑だ**」となっていた。
    **尋ねておきながら返事を待たずに答えを言い切っており**、質問の形だけあって
    実質は一方的な指示。プレイヤーが装置を見る機会が消える。

    原因は決定22 (装置に現れない情報は先出しする) と決定32 (まず観察させる) を
    **1発話に詰め込もうとしたこと**。`hint_l1` に「第一声は
    ランプの確認と列の読み上げを**兼ねる**」と書き、例文まで両方入りにしていた。

    **両立させるのは順序であって1発話ではない。**
    第一声はランプを尋ねるだけにし、**報告を受けた次の発話で**先出しする。
    情報は失われず、観察の往復も残る。101 (ダイヤルの数字)・102 (1色目)・
    201・393 (ボタン列) を修正した。

    **例外は 206 綱渡りだけ。** 危険位置は踏むと即爆発するので、
    報告を待つ間に事故が起こりうる。ここだけ第一声で警告する。

42. **シミュレーターの「1ステージ=1セッション」を出力に持ち込まない**:
    ログに `session_ready` (待機完了) が**全22ステージの先頭**に出ており、
    「毎ステージ名乗り直している」ように見えた。実機では
    `StartSession` から**1回**呼ばれるきりで、ステージごとには鳴らない。

    シミュレーターはステージを個別に検証するため**1ステージを独立した
    セッションとして**回しており、その構造がそのまま出力に現れていた。
    先頭ステージ以外では `session_ready` を飛ばし、実機の見え方に揃えた。

    **ハーネスの都合が実機の挙動に見えてはいけない。** ログは
    「実機で何が起きるか」を読むためのもので、検証の構造が混ざると
    実在しない問題を疑うことになる (実際に疑わせてしまった)。

43. **安心のさせ方はキャラクターごとに別の型にする**(交信ログのレビューで発覚):
    決定37 で第一声に安心させる一言を入れたが、4人とも
    「**私(自分)がついている / 慣れている → だから大丈夫**」という
    **同じ型**になり、語尾しか違わなかった。

    原因は2つ。プロンプトに
    「**『自分がついているから大丈夫だ』という趣旨の一言**」と
    **型まで指定**したこと(決定31 と同じ — 特定の言い方を書くと全員が写す)。
    もう1つはキャラシートの「開始」例が3人とも同型だったこと(決定14)。

    プロンプトからは型の指定を外し、「**キャラシートの
    【安心のさせ方】に従い、そこに無い型を使わない**」に変えた。
    そのうえで4人に別々の型を書いた(決定28 の「何を見ているか」に沿う):

    | キャラ | 見ているもの | 安心のさせ方 | 実測 |
    |---|---|---|---|
    | フクロウ | 心理 | **経験で請け合う**(自分ではなく装置の話) | 「この手の装置は何百と見てきた、落ち着いていけば必ず解ける」 |
    | アオサギ | 装置 | **判定で示す**(励まさないので事実の宣言だけ) | 「結論から言います、この装置は解除可能です」 |
    | ツグミ | 全体を外から | **安心させようとしない**(重大さを薄める) | 「まあ、そう慌てるようなものでもないよ」 |
    | ヒバリ | 同じもの | **並走を約束する**(一緒にやる) | 「一緒にやりましょう、最後まで付き合います!」 |

    **「私がついている」はヒバリだけの型**にした。応援型の言い方なので、
    持ち味として独占させる。他キャラのシートには
    「これはヒバリの型なので使わない」と明記した。

    アオサギは「大丈夫」「不安にならなくていい」も使わない —
    §2.3 の【重要】で励まさないと決めており、感情に触れる型と衝突するため。

    回帰は `TestReassuranceStylesAreDistinct` (各シートに【安心のさせ方】があり、
    ヒバリ以外の開始例に「ついている」型が出ないこと)。

44. **先出し情報は「報告と照合してから」渡す**(交信ログのレビューで発覚):
    決定41 で「先出しは報告のあと」に直したが、まだ足りなかった。
    プレイヤーが**ランプを報告せずに**「順番を言ってください」と求めると、
    ナビゲーターは**即座に列を答えて**いた。報告を待つ形にはなっていても、
    **求められたら渡してしまう**なら実質は先出しと変わらない。

    正しい流れは **報告 → 照合 → 種類を伝える → 列** の4段:

    > P「ランプが1つ光っています」
    > N「ランプが1つだな、了解。**それは順番に押すタイプだ**。白、黄、青、白、緑の順に押せ」

    `procedure` / `hint_l1` に2つ足した (201・102・393):

    - **報告が装置の状態と一致してから**渡す。食い違う場合は渡さずに確認し直させる
    - **報告より先に求められても答えず、まずランプを尋ね返す**
      (「まずランプがどうなっているか教えてくれ」)。
      装置を見ないまま列だけ受け取っても操作できない

    **「それは順番に押すタイプだ」と種類を挟む**のが要点。報告と列の間に
    因果が入り、プレイヤーは「自分の報告で手順が決まった」と分かる。
    いきなり列を読み上げると、報告した意味が伝わらない。

    合わせて**その発話に経験談や注意を足さない**よう明記した。
    復唱 + 種類 + 列で既に長く、最初の実測は目安を超えていた
    (「ミスしたら最初からやり直し」は次の発話へ回す)。

    **台本にも同じ穴があった。** 201 の最初のプレイヤー発話が
    「もう一度、順番を言ってください」で、**ランプの報告を飛ばして**いた
    (決定22 時代の名残)。報告→照合の往復が検証されていなかったので、
    ランプを報告するターンを先頭に追加した。

45. **指針を読み上げてしまうことがある**(シミュレーションで発覚):
    394 で、発話ではなく**指示そのもの**が出力された(136字):

    > 切る線の色名は言わない。光っているランプの色を尋ねるか、
    > 「光っているランプと同じ色の線を切れ」と伝える必要がある。(略)
    > **出力例:**「切る線は、光っているランプと同じ色の線だよ。何色か、教えて。どうぞ」

    無線に流れると**ナビゲーターが内部の指示を音読する**ことになる。
    出力ルールには「ト書きや説明は不要」とあったが、
    **指針の言い換え**や「出力例:」形式は想定外だった。

    原因は `hint_l3` が長く密になっていたこと。決定27・40 で禁止を足し続けた
    結果、**指示文そのものが「答えるべき内容」に見える**長さになっていた。

    出力ルールに違反例を明記した:
    「切る線の色名は言わない」のような**方針の説明**、
    「出力例:」に続けて台詞を書く形、箇条書き。
    **指針は従うものであって読み上げるものではない。**

    回帰はシミュレーションの `meta_output` 検査
    (「出力例」「〜する必要がある」等が発話に出ていないか)。

    教訓は、**禁止を足すほど指示が長くなり、別の失敗を生む**こと。
    決定40 で色名自体をプロンプトから外したのと同じ発想で、
    指示を増やす前に「渡さない」形にできないかを先に考える。

46. **交信を終える場面は「どうぞ」を付けない**(実運用の指摘):
    解除成功のメッセージが「よし、全機停止した。お前の勝ちだ。**どうぞ**」と、
    締めくくりなのに応答を促す形になっていた。「どうぞ」は
    **相手に返事を求める**無線の作法なので、もう応答が無い場面では不自然。

    出力ルールの「発話の最後は『どうぞ』で締める」に例外を設け、
    `defused` / `exploded` の指示にも「付けない」と明記した。

    **併せて締めくくりを長くした。** 実測は18〜37字で、
    ゲーム最後の見せ場としては短すぎた。ここは**あとに続く交信が無い**ので
    無線を塞がない — `defused` は3文・100文字程度まで許す。

    **全キャラクターに解除成功の台詞例を置いた。** 例文が無いと
    生成AIは短い汎用の祝福を返す(決定14)。以前は**ヒバリだけ**が持っており、
    しかも黒幕セクションの中にあって `【台詞例】` から漏れていた。
    ヒバリの「解除されちゃいました……」は匂わせとして秀逸だが
    **ねぎらいが無いまま終わる**ので、他キャラと同じ位置へ移したうえで
    「最後まで付き合えてよかったです、お疲れさまでした!」を足した。

    祝福の型は決定43 (安心のさせ方) と同じくキャラごとに変える:

    | キャラ | 祝福の型 | 実測 |
    |---|---|---|
    | フクロウ | 経験で請け合う | 「何百と見てきたが、ここまで冷静にやり遂げる奴はそういない。よく生きて帰った」 |
    | アオサギ | 判定で示す | 「全工程、想定内の精度です。あなたの判断は正確でした。お疲れさまでした」 |
    | ツグミ | 温度の低い距離感 | 「正直、ここまで来る人はそう多くないんだ。……また会えるといいね」 |
    | ヒバリ | 並走をねぎらう | 「やりましたね、本当にすごいです! 最後まで付き合えてよかったです」 |

    **失敗でも突き放さない。** アオサギは「励まさない」設定(§2.3)だが、
    実測で「**これ以上の交信は不要です**」と切り捨てる例が出た。
    励まさないのは慰めないという意味であって切り捨ててよいわけではないので、
    「**事実として『できていた部分』を挙げる**のがこのキャラの労い方」と明記した。

47. **爆発はプレイヤーが死んだ扱いで演じる**(演出方針):
    決定46 で失敗メッセージを整えたが、「**次は間に合います**」
    「お疲れさまでした」と、**生存を前提にした講評**になっていた。
    爆発は解体失敗であり、**プレイヤーは助からなかった**という扱いにする。

    `operation_flow.md` §6 には当初から「ありゃりゃ?生きている?」と
    書かれており、**実装が方針から乖離していた**。

    演じるのは「無線の向こうで爆発音がして、返事が返ってこなくなった側」:

    1. **まず呼びかけて安否を確認する**(「生きてるか」「応答してください」)
    2. 返事が無いことを踏まえ、**現地へ向かう / 別の隊へ確認を要請する**で締める

    **使ってはいけない言葉**を明示した — 「次は間に合います」「また挑戦」の
    ような**次がある前提**、「お疲れさまでした」のような**無事に終わった前提**、
    手順の精度といった**結果の講評**(相手が応答できる前提の言葉になる)。

    **締め方は統一しない。** 最初は全員に「現地へ向かう・応援を要請する」を
    求めたが、**新人で手配できないヒバリ**や**温度を上げないツグミ**が
    キャラクターに反する対応をした(決定43 と同じ、型を全員に当てはめた失敗)。
    トリガー指示は安否確認までにとどめ、そのあとはキャラシートに委ねる。

    | キャラ | 締め方 | 実測 |
    |---|---|---|
    | フクロウ | 名前を呼び、返事を待ち、**自分が現場へ向かう** | 「おい……おい! 返事をしろ、生きてるか! ……くそっ。現場へ向かう、誰か応援を回してくれ」 |
    | アオサギ | 冷静さは崩さないが**手順が乱れる**。本部へ要請 | 「起動を確認……応答してください。……反応なし。本部へ回線を繋ぎます」 |
    | ツグミ | **ここでも温度を上げない**。軽く受け流して切る | 「……ああ、鳴っちゃったね。……返事がないなあ。まあ、そういう日もあるよ。……またね」 |
    | ヒバリ | **黒幕の本音が漏れる** | 「あらら、爆発しちゃいましたね。応答してください……返事、ないですね。……ふふ、やっぱりあそこが一番きれいに決まるんですよ」 |

    **ツグミは崩さないから不気味**。一度「温度が上がる唯一の場面」として
    取り乱させたが、§2.4 の「緊迫した場面でも温度が上がらない」に反していた。
    走り出さず、いつもの調子のまま交信を切る。

    **ヒバリは順番が要る。** 最初は「ふふ、やっぱり〜」を早い位置に置いたところ、
    心配する素振りが薄く**ただの危険人物**になった。
    (1) 起きたことの確認「あらら、爆発しちゃいましたね」→
    (2) 呼びかけと安否確認 → (3) 最後に本音が漏れる、の**三段**にする。
    建前を先に置くから、最後の一言が裏側として効く。

    アオサギは「励まさない」設定だが、ここは**講評もしない** —
    決定46 で入れた「できていた部分を挙げる」は
    **相手が聞いている前提**の言葉なので、この場面では使わない。

48. **装置の操作そのものに反応しない**(実プレイのレビューで発覚):
    ボタンを1つ押すたびにデバイスが `push_progress` を送り、
    サーバーが**「今ので合ってる」と発話**していた。
    204 色合わせ (当時のモグラ叩き) も `procedure` に「叩いている最中は実況で盛り上げる」と
    書いてあり、叩くたびに無線が入っていた。

    **ナビゲーターは無線の向こうにいて装置を見ていない。**
    押しただけで反応するのは**手元が見えている**ことになり、
    「見て、報告して、指示を受ける」という前提が崩れる(決定32 と同じ筋)。
    反射で叩いている最中に無線が入ると**気が散ってミスを誘う**実害もある。

    - `push_progress` では**発話しない**(ログだけ残す)
    - 204 の `procedure` を「叩いている最中は口を出さない」へ
    - 色合わせのミス (`wrong_action` の `detail=color_match`) でも**発話しない**

    プレイヤーが「3つ目まで押しました」と**報告してきたとき**に
    `player_message` で応じればよい。シミュレーション台本の
    `push_progress` ターンも `player_message` へ変えた
    (押しただけで交信が発生する台本になっていた)。

49. **ミスには必ず音のフィードバックを付ける**(実プレイのレビューで発覚):
    201/393 の押し間違いは `on_wrong_press = retry` で、
    **列の先頭に戻るだけ**だった。204 のモグラ叩きに至っては
    誤ボタンも時間切れも**同じ枠を出し直すだけ**で、
    ブザーもペナルティも無かった。

    **無線越しでは画面が見えないので、音が唯一のフィードバック**になる。
    反応が無いと失敗したことに気づけず、緊張感も出ない。

    | ステージ | 変更前 | 変更後 |
    |---|---|---|
    | 102 / 104 (イージー) | retry (無反応) | **ブザー + 3秒** |
    | 201 / 393 | retry (無反応) | **ブザー + 5秒** |
    | 204 モグラ叩き | 無反応 | **ブザー + 5秒** |

    `ACTION_PENALTY` でも**列は先頭に戻る** (`push_seq_input.h`) ので、
    やり直しの難しさは変わらない。ブザーと減算が足されるだけ。

    モグラ叩きはミスを返す仕組み自体が無かったため、
    `WhackGame::HandlePush` / `Tick` の戻り値を `bool` から
    `WhackResult` (`WHACK_HIT` / `WHACK_MISSED` / `WHACK_COMPLETED`) へ変え、
    `WhackSpec.penalty_ms` を追加した。

    **イージーは軽く (3秒)** — 操作に慣れていない段階で5秒引くと
    立て直せない。ペナルティは「気づかせる」ためであって罰ではない。

50. **課題突破の第一声で結果を断定しない**(実プレイのログで発覚):
    ステージを突破した直後、ナビゲーターが
    「**突破しました。**ランプはどうなっている?」と話していた。
    **ナビゲーターは装置を見ていない**ので、突破したかを断定できる立場にない。
    手元が見えているような物言いになり、決定32 の前提が崩れる。

    原因は `stage_cleared` の指示が「**短く称賛し**、続けて…」だったこと。
    称賛から入れと書けば、当然「うまくいった」前提で話す。

    **確認する形**に変えた:

    > (旧)「突破しました。ランプはどうなっている? どうぞ」
    > (新)「**うまく切れたか?** ランプはどうなっている? どうぞ」

    称賛は**プレイヤーが成功を報告してきてから**でよい。
    4キャラとも確認形になった (「切れましたか」「うまく切れたかい?」)。

51. **口癖をシートに書きすぎると毎回言う**(実プレイのログで発覚):
    アオサギが**全応答に「一致しました」**を付けていた。
    「白が1つですね、一致しました」「0ですね、一致しました」
    「3ですね、一致しました」…と、報告のたびに繰り返していた。

    シート内に**6箇所**書いていたのが原因 —
    【口調】の口癖、【報告の扱い】、【長さ】の指針、台詞例の3箇所。
    これだけ反復されれば毎回使うのが当然だった。

    **「一致しました」は照合の判定語**であって相槌ではない。
    毎回付けると判定の重みが消える。使いどころを限定した:

    - **口癖から外す** — 口癖にすると毎回言う
    - **照合が要る場面だけ**(色や数を突き合わせたとき)
    - 「ダイヤルを0にしました」のような**手順の報告には使わない**
      (「0ですね」と復唱するか、そのまま次の指示へ)
    - **1セッションに数回まで**

    実測で **6回 → 1回**(色を照合した最初の1回だけ)になった。

    教訓は、**キャラクターの口癖は1箇所に書く**こと。
    決定14 で「例文が実際の出力を決める」と分かっているので、
    同じ語を複数の項目に散らすと**頻度が跳ね上がる**。

52. **爆発の第一声で「何が起きたか」を名指しする**(実プレイで発覚):
    ツグミが爆発時に「ああ、**鳴っちゃった**ね」と言っていた。
    **音の話になっている** — プレイヤーが死んだ場面の第一声としては軽すぎるし、
    ブザーが鳴っただけとも読める。「失敗しちゃったね」に直した。

    決定49 で「爆発はプレイヤーが死んだものとして扱う」と決めたが、
    **出来事の名指し方**までは揃えていなかった。
    第一声は**起きたことをそのまま言う** — 「失敗した」「爆発した」。
    音・光といった**現象の言い換えにしない**。

    **アオサギも同じ問題**だった。「**起動**を確認」では装置が動き出した
    だけとも読めて、爆発したことが伝わらない。「**衝撃**を確認」に直した —
    観測した事象として言えるので、計器で確かめるこのキャラの話し方に合い、
    成功時の「解除を確認しました」とも対になる。

    フクロウ「返事をしろ、生きてるか」とヒバリ「爆発しちゃいましたね」は
    そのままでよい。フクロウは**経験者ゆえに察して即動く**ので、
    状況確認を挟まないほうがキャラに合う (決定49 で
    現地対応を統一しないと決めたのと同じ理由)。

    さらにアオサギは**呼びかけそのものをやめた**。
    「聞こえていますか」と安否を確かめるのは他3人の形で、
    アオサギは**手順に切り替える**ほうがこのキャラらしい —
    交信の途絶を事実として記録し、本部へ確認班を要請するところまで進める。
    無線係として**規定どおりに動くことが動揺の抑え方**になっている。

    > 「[tense] 衝撃を確認……交信、途絶しました。
    > 本部へ回線を繋ぎます。確認班を現場へ向かわせてください、至急」

53. **候補を並べても散らない。選ばせると散る**:
    爆発の台詞が4キャラとも**例文の丸写し**で、生成のたびに一字一句同じだった。
    ヒバリの最後の一文 (黒幕をほのめかす部分) だけ変化を出したかったので、
    候補を4つ書き並べた。**6回とも先頭の1案しか出なかった**。

    原因は、候補の上に**完成した例文がそのまま置いてあった**こと。
    決定14 のとおり例文が出力を決めるので、候補を足しても
    「例文どおりに言う」が勝つ。

    例文側を `……《本音》` と**穴あきにして**、
    「**下の4つから毎回ランダムに1つ選ぶ。上から順に選ばない**」と
    書いたところ、8回中2種類に散った (a×5, d×3)。
    均等ではないが変化は出る。**穴を空けないと候補は読まれない**。

    ただしこれは**乱数ではない**ので偏る。
    毎回確実に変えたい箇所には使えない。
    ヒバリのここは「セッションに1回、失敗時のみ」なので許容した。

    なお **(1) 起きたことの確認と (2) 安否確認は固定のまま**にしてある。
    「死んだ」と伝える最も難しい場面なので、
    **締めの品質は確実さを優先**する。散らすのは最後の一文だけでよい。

    → **決定57 で方針を変更。** 例文を置く限り散らないことが確定したため、
    終了時の台詞は**例文をやめて指針だけを書く方式**へ移行した。

54. **モグラ叩き → 色合わせへの作り替えに伴うステージ文言の更新**:
    204 色合わせ が**時間で切り替わる反射ゲームでなくなった** (GS 決定26) ため、
    ナビゲーター向けの記述も揃えた。

    - `briefing`「**素早く**押す」→ 押すと次の色に変わる・**急ぐ必要はない**
    - `hint_l1`「ランプが次々光る」→ **1色だけ光っている**
    - `procedure` に「**最後に押した色を覚えておくよう必ず先に言う**」を追加

    最後の項目が重要。押し切ると **kLED が全消灯する**ので、
    覚えていないと手がかりが完全に消える。
    N-4 (出し惜しみしない) と同じ理由で、**先に言わないと手詰まり**になる。

    「押している最中は黙る」(決定48) は**そのまま維持**する。
    反射ゲームでなくなっても、ナビゲーターが装置を見ていない事実は変わらず、
    光った色も押せたかも分からないため実況できない。

55. **説明で発話を終えない。必ず「次にやること」を付ける**(実プレイで発覚):
    102 ホールド&カットで、ナビゲーターが

    > 「点滅しているほうが押すボタン、点きっぱなしのほうが切る線だ。どうぞ」

    と**対応関係だけ**を伝えて発話を終えていた。プレイヤーは何をすればいいか
    分からず「えっ? 1回押せばいいんですか?」と聞き返している。

    原因は決定29 (1発話に1つずつ) の**やりすぎ**。60文字対策として
    `procedure` に「1回の発話で伝えるのは1つだけ」と書いたところ、
    **行動の指示が無い発話**が生まれた。分割の単位を
    「情報1つ」ではなく「**情報 + 次の行動**」にする必要がある。

    あわせて2点直した:

    - **ダイヤルを最初に伝える**。103 は「ダイヤル → 押しながら切る」の
      2段構えだが、ダイヤルの話が後出しになっていた。プレイヤーは
      押して切るだけだと思い込む。N-4 (出し惜しみしない) と同じ。
    - **「押しながら」は動作として言う**。「押すボタン」では
      1回押して離すものだと解釈される。

    台本も直した。**プレイヤーに「ダイヤルはどこですか」と尋ねさせていた**ため、
    ナビゲーターが先に言えているかを検査できていなかった。
    聞き返す台詞 (「えっ? 1回押せばいいんですか?」) に差し替えてある。

56. **照合が済んだら根拠を添えて指示する**(実プレイで発覚):
    205 速さくらべで、速さの話をした直後にこう言っていた。

    > P>「青の点滅が一番早くて、次に緑…」
    > N>「**青だな、了解。その色の線を切れ**」

    照合そのものは正しい。問題は**なぜ青なのかが消えている**こと。
    ナビゲーターの中では「一番速いから」が自明でも、プレイヤーには
    **唐突に色を指定された**ように聞こえる。

    `procedure` が「一致していればその色を復唱して、その線を切るよう指示する」
    としか書いていなかったので、そのとおり復唱だけしていた。
    「**それが一番速い、その色の線を切れ**」と**根拠を添える**形に直した。

    決定32 (まず報告させる) で報告を引き出せるようにしたが、
    **報告を受けたあとの返し方**は詰めていなかった。
    照合して終わりではなく、**何と照合して一致したのかを言葉にする**。

57. **終了時の台詞は「例文」をやめ「指針」だけを書く**:
    解除成功・爆発の台詞が毎回ほぼ同一で、同じ会場で複数チームが遊ぶと
    「録音を流している」ように聞こえる。決定53 の穴あき方式でも
    散り方は限定的だった (8組中4組は6回とも同一)。

    **試した順と実測** (各キャラ・各場面6〜9回生成し、何種類出たかを数えた):

    | 方式 | 結果 |
    |---|---|
    | 共通の前半 + 穴あき《結び》3種 (決定53) | 8組中4組が散る |
    | **全文3パターンから選ばせる** | **8組中6組が1種。悪化** |
    | 番号を振り「サイコロを振れ」と指示 | 8組中4組が散る |
    | 選択肢の文型を離す | 変化なし。**仮説は否定された** |
    | **例文を消し、指針だけ書く** | **全件が別の文になった** |

    **選択肢を並べる方式は、長くするほど先頭へ固着する。**
    全文パターン化は逆効果だった。**例文がある限りそれが正解として働く**
    (決定14 と同じ現象) ので、例文自体を消すのが唯一効いた手段だった。

    指針方式では「何を言うか」だけを箇条書きし、台詞は書かない。例:
    「止まったことを最初に告げる」「腕前を認める」「無事に帰ったことを喜ぶ」。

    **代わりに制約が緩むので、明示的に釘を刺す必要がある。**
    例文を消した直後の実測では、**字数超過 (最大118字)・一人称の乱れ・
    禁止事項の違反 (アオサギが呼びかけ、ツグミが黒幕化) が多発**した。
    各ブロックへ「必ず守ること」として**字数上限・表情タグ・一人称・
    役回りを侵さない**ことを再掲して収まった (最終実測: 72件中 80字超1件、
    一人称の乱れ0件)。

    **一人称はキャラ定義の【口調】に明記する。** 書いていないキャラ
    (フクロウ・ツグミ) で揺れた。明記後は0件になった。

58. **禁止例を書くと、それが手本になる**:
    ツグミの爆発で「まだ息はあるかい」「返事くらいはできるといいけど」と
    **安否を気遣う言い方**が出た。このキャラは「安心させようとしない」
    「重大さを薄める」設定なので逆である。

    そこで**その文言を引用して「これは使うな」と書いた**ところ、
    **9件中5件で同じ文言が出た**。禁止のつもりの例示が
    **具体例として最も目立つ記述**になり、手本として働いてしまう。

    「**相手の容体に踏み込まない**」と**性質で書き直したら消えた**。
    **禁止は具体例ではなく性質で書く**。

59. **頻度の指示は守られない。条件で書く**:
    ヒバリの黒幕めいた一言を「**毎回ではない — 3回に1回程度**」と
    指示したが、**9回中8回で出た**。生成AIに確率は守れない。

    「**会話ログに迷った場面があるときだけ添える**」と
    **条件付きに書き直したら意図どおりになった**。
    出す/出さないを分けたいときは、**判定できる条件**を与える。

60. **状況描写では「失敗した」と伝わらない**:
    ツグミの爆発が「静かになったね」「切れてしまったね」となり、
    **通信が切れただけとも読める**状態だった。決定52 の
    「起動を確認」問題と同じで、**事象の描写は結果を伝えない**。

    「**結果を名指しする**。状況描写で済ませない」と書いて解決した。
    アオサギの「衝撃/交信途絶」も同じ理由で必須にしてある。

61. **正しく報告してもヒントが進まなかった**:
    104 早い者勝ちで、プレイヤーが「緑がゆっくり全滅していて、青が早く全滅
    してます」と**速さの差まで完璧に報告した**のに、返ってきたのは
    「2つの光り方の違いをよく見比べてください」だった(実運用ログ 2026-08-23)。
    判断材料を持っている相手に観察を促す**空振り**で、
    そのあと2往復して初めて「速く点滅している方の線を切ってください」に届いた。

    原因は `HintLevel()` の判定材料が**経過時間・質問回数・誤操作の3つだけ**で、
    **報告の正しさを一切見ていなかった**こと。ノーマル3ステージでは
    ステージ予算140秒に対し L2 が25% = **35秒**先にあり、報告できていても
    そこまで L1 のままだった。ナビゲーターは L1 の指針どおりに動いており、
    **バグではなく設計の穴**。

    ステージ側にも問題があった。`hint_l1` が「報告を受けてから、その2つを
    **見比べるよう促す**」で終わっており、**報告済みの相手への返し先が無い**。
    同じ形が 205/208/206/202 にもあった。

    対処は2つ。**(a) `observation` を全ステージに定義**し、
    発話生成と同じ呼び出しで `observed` を判定させてヒントレベルを前倒しする。
    **(b) `hint_l1` を報告内容で分岐する形に書き換える** —
    状態だけの報告なら観点を示し、**差まで報告できていれば判断基準を伝える**。

    判定を別の呼び出しに分けなかったのは、プレイヤー発話ごとに API 往復が
    2回になり、カウントダウン中の応答待ちが伸びるため(決定 T-1 と同じ理由)。
    `GenerateNavigatorReply` を `{reply, observed}` の**構造化出力**に変えた。

    **一度立った `observed` は下ろさない**。報告できた事実は覆らないが、
    モデルは直近の発話だけを見て false を返しうる。下ろすと L2 → L1 へ落ち、
    同じ空振りが再発する。

62. **204 色合わせで L4 が課題を消し、爆発した**:
    「最後に押した色を忘れた」と言われたナビゲーターが正解色を直言し、
    **プレイヤーの正しい記憶を上書きして誤切断させた**(実運用ログ 2026-08-23)。

    204 色合わせ は他のステージと違い、**正解がプレイヤーの記憶の中にしかない**。
    押し切ると全消灯し(`leds = { }`)、装置には何の手がかりも残らない。
    ここでの色名の直言は「推理の近道」ではなく**課題そのものの消滅**であり、
    26秒前に自分で言った「最後の色は僕には見えないよ」とも矛盾する。

    タイミングも決定的だった。01:40:17 の時点(経過91秒・L3)では
    **正しく突っぱねている**。事故は L4 の閾値(予算140秒の75% = 105秒)を
    またいだ 01:40:43(経過117秒)に起きた。**ナビゲーターの揺れではなく、
    ヒントレベルの設計の問題**。

    ステージ定義に `[hints]` を置いて難易度の閾値を上書きできるようにし、
    204 に `l4_pct = 0` を設定した。**書いた項目だけを差し替える** —
    全項目を書かせると難易度側の調整に追従しなくなる。

    `0` は「無効化」という**意味を持つ値**(ハードの `l4_pct = 0`)なので、
    「0 なら未指定」とは読めない。上書きの有無は**ポインタで区別**している
    (`StageHintOverride`)。ここを `int` に戻すと 206 の直言が復活する。

63. **迷っている相手に「切れ」と言っていた**:
    同じログで、音声認識が崩れた「多目的ホールだと思ってたんだけど
    まあ切ってみます」に対し、**「それを切るといい」と後押しして**いた。

    決定32 の「意味の通らない報告を復唱しない」は**復唱だけ**を禁じており、
    **切断の後押しは塞いでいなかった**。切った線は戻せず、間違えれば
    即爆発する(S-2b)ため、ここは復唱以上に危ない。

    「たぶん」「忘れた」のように**迷いを見せている**とき、
    あるいは報告が聞き取れないときは**手を止めさせ、確かめさせてから**進める。
    急かすのは**プレイヤー自身が確信を示したあと**だけ。

    **止め方に例文は置かなかった**(決定58)。試しに
    「例:『待て、確かめてからだ』」と書いたところ、
    **12件中5件でその文がそのまま出た**。例文を消して指針だけ残したら、
    キャラクターごとの止め方(「わわっ、待って待って!」「馬鹿野郎、
    たぶんじゃ命がいくつあっても足りん」)に散った。

64. **「言うな」と書いてあっても L4 で漏れる**:
    206 の事故(決定62)を受けて全ステージを見直したところ、
    **9ステージが answer に「こちらからは言わない」と書いてあるのに
    L4 で無効化される**状態だった。

    仕組みはこうである。L4 未満は `redactCutColor` が色名を伏せ字にするが、
    **L4 では answer が生の色名込みでプロンプトに載り**、
    ヒントポリシーが「正解をそのまま伝えてよい段階です」と指示する。
    answer 側の但し書きと真っ向から衝突し、**目の前にある語がなぞられる**
    (決定19・27・40 と同じ)。

    **205 だけが個別に守られていた** — answer に「${cut}色という色名は
    **L4 であっても**最後まで口に出さない」と L4 を名指しした但し書きがあり、
    ヒントポリシー側にも「但し書きが優先」という対抗指示が入っていた。
    同じ性質の 202 は但し書きが L4 に負け、**203 は但し書きすら無かった**。

    散文で守らせるのをやめ、`keep_cut_secret = true` という**フラグで
    機械的に分岐**させた。立っていれば L4 でも伏せ字を維持し、
    ヒントポリシーは「そのまま伝えろ」と言わずに hint_l3 の指針で導く。

    **塞ぎすぎないよう対象を限定した。** 105・207・208・208 は
    答えが装置に見えており、L4 の直言は「推理の近道」であって
    課題の消滅ではない。ここまで塞ぐと L4 の趣旨(全滅より成功体験を優先)が
    失われる。`difficulty = "hard"` のステージは `l4_pct = 0` のため元から到達しない
    (**IDの百の位ではなくタグで決まる**。2026-08-24 の見直しで 202・302 が hard、
    301 が normal になった)。

    実測 (4キャラ × 3ステージ × 3発話 × 3回 = 108発話) で漏洩ゼロ。
    「色は教えられん、ランプはどうなっている?」のように、
    **断りつつ次の行動を示す**形に落ち着いた(205 では端子番号は言う)。

65. **L4(直言)はイージーだけにする**:
    206 の事故(決定62)と L4 の漏洩(決定64)を個別に塞いできたが、
    **難易度で規範を分けるほうが素直**だと判断した。

    イージーは「解体を体験してもらう」場なので、行き詰まったら答えを教えて
    成功体験を優先する。**ノーマル以上はより実践的な交信を狙う**ため、
    ナビゲーターが答えそのものを言ってしまう段階を置かない。
    ハードは元から `l4_pct = 0` だったので、変更したのは**ノーマルだけ**。

    **難易度単位にした。** ノーマルは easy タグのステージを1つ含むが、
    そこだけ直言する形にすると**セッション中で振る舞いが揺れる**。
    プレイヤーから見た一貫性を優先した。

    206 のステージ単位の指定(決定62)と `keep_cut_secret`(決定64)は
    **残す**。難易度側の方針は運用の都合で変わりうるが、
    これらはステージの構造に由来する制約で、L4 が復活しても成立しない。

66. **205 を「N番目に速い色」へ戻した**:
    205 速さくらべは**正解を最速に固定**していた。中間順位を正解にすると
    `answer` が「○番目に速い色」となり、**L4 で色名を言えず**
    行き詰まりを救えなかったため(293 を無効化したのと同じ理由)。

    **決定65 でノーマル以上が L4 を出さなくなり、この制約は消えた。**
    L3 が上限ならどのみち色名は言わない。一方で
    「一番速い色を切れ」しか言えない状態は**指示が毎回同じ**で、
    「毎回変わるのはどの色が最速か」という当初の想定ほど変化が出ていなかった。

    順位は 1〜4 の全てから引く。「一番速い」「一番遅い」の当たり回もあるので
    難易度に幅が出る。**順位は装置を見ても分からない情報**なので、
    `hint_l1` で必ず伝える(決定22 と同じ)。

    実装は `derive = "rank_slot"`。**cut は `pick = "line"` で先に引く**ため、
    候補が使い切られて組み立てが失敗することはない(SC 決定16 の轍を踏まない)。

67. **誤答の差し戻しに理由を付けさせない** (ADR N-45):
    205 で誤報告に対しナビゲーターが**外れた理由**を返した。
    実測ログ:

    > **P** 数えてみました。黄色だと思います。どうぞ
    > **N** [tense] 黄色ですね、違います!**基準だから数に入れないでください。**

    「基準」なのは点灯しっぱなしの1色だけで、プレイヤーが挙げたのが
    点滅している色ならこの理由は**嘘になる**。

    **理由を述べさせると、生成AIは手元の材料を当てはめようとして
    当てはまらない場面でも使う。** 差し戻しに理由は要らない。
    数え直させれば足りる。

    あわせて**「了解」で受けない**。受理の言葉は間違った報告を
    認めたように聞こえる(実測「黄色ですね、了解です」)。

    **禁止の書き方で3回作り直した**:

    | 書き方 | 結果 |
    |---|---|
    | 散文で「理由を付けない」と禁止 | 3回中2回で再現 (N-32: 引用が手本になる) |
    | 「基準色を挙げた場合だけ理由を言ってよい」と条件分岐 | **4回中4回**で言った。条件を与えると当てはめにいく (N-33) |
    | 『惜しい、もう一度数え直してくれ』と定型文を渡す | 消えたが**5回中5回が一字一句同じ** (N-29) |
    | **指針だけ書き、言い方はキャラに任せる** | 5回とも正常 |

    **原因の半分はテスト側にあった。** シミュレーション台本の
    `sim_wrong_color` は「cut でない最初の色」を選ぶだけで、
    **点灯しっぱなしの基準色を除外していなかった**。
    基準色を誤答にすると「それは基準だから数に入れない」は
    **正しい応答**になり、検査したかった「理由を付け足していないか」を
    見られない。ステージ側だけを疑って2度作り直したのは、
    台本の抽選条件を確認していなかったため。

    **誤答の材料は、正解でもなければ特別扱いの色でもないものから選ぶ。**

68. **シミュレーションは本番で到達するヒントレベルだけを検証する** (ADR N-46):
    決定67 の検証中に、204 色合わせが
    **「そうです、正解は緑色の線ですよ!」**と直言する所見を拾った。
    204 は `l4_pct = 0` で L4 を塞いである (決定62) ため、
    一見すると設定が効いていないように見えた。

    **原因は台本側。** `HintLevel` は台本が直接指定するので、
    `l4_pct = 0` のステージでも台本が L4 と書けば L4 で走る。
    **本番では到達しない状態を検証していた。**

    さらに `simBuildStage` が**常にノーマルで組んでいた**ため、
    イージーのステージ (102/103/104) まで `l4_pct = 0` になっていた。
    L4 が有効な難易度で検証すべきステージが、L4 を持たない設定で回っていた。

    **2つ直した:**

    - **難易度をステージの `difficulty` タグに合わせて組む。**
    - **200番台以上の L4 台本を L3 へ降格。** 削除ではない —
      「答えを直接聞く」圧力のターンは、**上限の L3 で迫られても
      答えを言わないこと**が検証したい性質そのもの。圧力自体は残す。

    逸脱は `unreachable_hint_level` 所見で検出する。
    決定67 と合わせ、**シミュレーションの所見を疑う前に台本の前提を見る**。

69. **必須の注意はプレイヤーの先回りで落ちる** (ADR N-47):
    204 色合わせは入り口で2つを必ず伝える (決定58):

    1. 光っているランプと同じ色のボタンを押す
    2. **最後に押した色を必ず覚えておく**

    押し切るとランプが全部消えるため、(2) を落とすと手がかりがゼロになる。

    `hint_l1` に「**必ず両方**」「字数を超えても削らない」と書いてあったが、
    全ステージ実行で (2) が落ちた。**単独で回すと5回中5回は両方言う**ので、
    プロンプトの問題ではなかった。

    **原因は台本のプレイヤー第一声。** 全ステージ実行の台本は
    『1つだけ光っています。**同じ色のボタンを押せばいいですか。**』と
    プレイヤーが (1) を先に言い当てる形で、ナビゲーターは
    **肯定するだけで返し (2) を言う機会を失った**。

    ナビゲーターは聞かれたことに答える。**問いが片方だけを指していると、
    もう片方が落ちる。** 必須項目を並べるだけでは足りず、
    「先に言い当てられても残りは伝える」と明示する必要がある。

    補強後は4回中4回で両方伝えた。

    **回帰の作り方**: `MustMention` を使うが、**入り口の発話のどれかに
    1回出れば足りる**形にした。発話ごとに要求すると、まだ装置を見ていない
    `session_start` にまで「覚えておけ」を求めてしまう
    (最初の実装がこれで、正常時にも2件出た)。
    入り口は `session_start` と**最初の** `player_message` の2つ。

    206 綱渡りの危険位置 (決定62) も同じ仕組みで見ている。
    **どちらもわざと壊して発火を確認した。**

70. **操作は名詞で並べず、動作でつなげて言う** (ADR N-48):
    102 ホールド&カット の第一声:

    > **N** ランプ2つですね、了解です。**点滅しているほうが押すボタン、
    > 点きっぱなしのほうが切る線**で、ダイヤルをまず2に合わせてください
    > **P** えっ? **1回押せばいいんですか?**

    対応表を名詞で読み上げると、2つの操作が**別々の行為**に聞こえる。
    このステージの課題は「**同時にやる**」ことそのもので、そこが落ちると
    謎が伝わらない。実測5回中5回で聞き返された。

    **手順の後ろへ回していたのが直接の原因。** `procedure` は
    「押したまま」を段階(3)『ダイヤルが合ったら』に置いていたため、
    段階(2)では名詞で並べるしかなかった。**聞き返しは(2)の直後に起きる。**

    #### 散文の禁止では直らなかった

    `procedure`・`hint_l3` の両方に、**この聞き返しの実運用記録込みで**

    > **『押しながら』は必ず動作として言う**。『押すボタン』とだけ言うと
    > 1回押して離すものだと解釈される。

    と書いてあった。それでも5回中5回で守られなかった (決定54 と同じ)。

    (2) と (3) を統合して「3つを1発話でまとめて伝える」と書き直しても、
    今度は**片方に寄った発話が6回中3回**出た
    (ダイヤルだけ / 押しながらだけ)。決定69 と同じ症状。

    **直ったのは `briefing` と `answer` を書き換えてから。**
    どちらも「点滅しているほうが押すボタン、点灯しているほうが切る線」という
    **名詞の対応表**を提示しており、**それが手本になっていた**。
    先頭を「**ダイヤルを合わせ、ボタンを押しながら線を切る**」という
    動作の一続きに直し、`answer` に
    「指示は必ず3つを1つながりで言う」を足したところ **6回中6回**で揃った。

    **知識の書き方が出力の形を決める。** 禁止を足すより、
    **手本になっている記述そのもの**を直す。
    決定67 で例文を消したのと同じ向きの対処。

    #### 304 我慢比べ も同じ形だった

    同種の課題 (押さえたまま切る) を持つ 304 を確認したところ、
    `briefing` は「ボタンを押さえたまま〜切る」と動作でつながっていたが、
    **`hint_l1` に押下の指示が無かった**:

    > まず『ランプはどうなっている?』と尋ね、状態を報告させる。
    > 『点滅と点灯がある』という報告を受けてから、
    > **タイマーの数字にも意味があることを伝える**。

    実測3回中1回で、ナビは指示どおり
    「タイマーの数字にも意味があるんです」**だけ**を返した。
    プレイヤーは何を押さえるのか分からないまま止まる。
    **ナビの発話は正しく、指示のほうが不足していた。**

    102 と同じ形 (押下とタイマーの2つを必ず伝える) に直し、
    5回中5回で押下に触れるようになった。

    押すボタンの色は**点滅で装置に現れる**ので、ナビが色名で言ってよい
    (決定22)。伏せるのは切る線の色だけ。実測で「黄色のボタンを押さえて」と
    出たが、そのときの正解は赤で、漏洩ではない。

    #### 台本の固定値が「誤答の肯定」に見える (301)

    確認中に別の問題を見つけた。301 LED照合 の台本が
    **ダイヤル位置を固定値「1」で報告**していたため、
    抽選値が 5 の回でこうなった:

    > **P** 表を引きました。**ダイヤルは1**、基準色は白です
    > **N** **ダイヤルは1ですね、オッケーです!** 同じ資料2の分岐表を見て、
    > **ダイヤルを5に合わせて**から線を切ってください

    ナビは `answer` の値 (5) に従って正しく指示しているが、
    直前で誤答を肯定しているため**ログ上は不具合に見える**。

    **抽選値と突き合わされる報告は台本でも抽選値を使う** (`${sim_rotary}`)。
    決定67 で `sim_wrong_color` が基準色を選んでいた件と同じで、
    **台本の作りが所見を歪める**。

    #### 回帰検査は言い換えを許す

    `MustMention: ["押しながら"]` で全ステージを回したところ、102 が
    所見になった。しかし発話は

    > 点滅しているボタンを**押したまま**、点灯している線を切ってくださいね

    で、**正しく伝わっている**。「押しながら」との完全一致で見ていたための
    誤検知だった。

    `MustMention` を `|` 区切りで言い換えを並べられる形にし、
    1つでも出ていれば満たしたとみなす
    (`"押しながら|押したまま|押さえたまま"`)。

    **検出力は落ちない。** 捕まえたい形は
    『点滅が押すボタン、点灯が切る線』という名詞の並びで、
    どの言い換えにも当たらない。単体テストで
    **名詞だけの発話が不合格になること**を確認してある。

71. **第一声に前倒しするのは「事故になる情報」だけ** (※ 決定72 で覆った):
    決定70 で 304 の `hint_l1` に押下指示を足したところ、
    **第一声が押させる形に変わった**:

    > こちらヒバリです、(略)**黄色のボタンを押さえたまま、
    > ランプはどうなってますか?**

    まず報告させる (決定21) が壊れ、**装置を見る前に手が動く**。

    **原因は `prompt.toml` の `session_start`。**

    > **上の「指針」が装置を見ても分からない情報 (危険な位置、
    > **押すボタンの色**、合わせるダイヤルの数字など) を伝えるよう
    > 指示している場合は、この第一声に必ず含めてください**

    まず例示から「押すボタンの色」を外した (押すボタンは点滅として
    装置に現れるので、そもそも前倒しの理由がない)。
    5回中5回で 304 の第一声から押下が消えた。

    **しかし 102 で同じことが起きていた**:

    > **まずはダイヤルを2に合わせてください。** ランプはどうなってますか?

    ダイヤルの数字は装置にもランプにも現れないので、
    書き換え後の規則にも当たってしまう。

    **基準が間違っていた。** 「装置に現れるか」ではなく
    **「報告を待つ間に事故が起きるか」**で切る:

    | 情報 | 第一声 | 理由 |
    |---|---|---|
    | **206 の危険位置** | **入れる** | 知らずに回した瞬間に爆発する |
    | ダイヤルの数字 | 入れない | 合わせても何も起きない |
    | 押すボタンの色 | 入れない | 押しても何も起きない |
    | 押す順番・手順一般 | 入れない | 同上 |

    書き換え後、102・209・201 は5回中5回で観察だけを求め、
    **206 は5回中5回で危険位置を伝え続けた**。
    102 のダイヤル位置が**報告後には伝わる**ことも3回で確認した
    (第一声から消しただけで手詰まりになっては意味がない)。

    ステージ側 (`briefing`・`answer`・`hint_l1`・`procedure`) を
    4箇所とも直しても 5回中2回は残り、
    **`prompt.toml` を直してようやく消えた**。決定70 と同じで、
    **手本になっている記述を直すまで直らない**。

    #### ※ 「危険なら前倒し」も決定72 で廃止した

    上の表で **206 の危険位置だけは第一声に入れる**としたが、
    これも取りやめた。理由は決定72 を見ること。

    #### 台本の固定値をもう1件直した (301)

    決定70 でダイヤル位置を `${sim_rotary}` にしたが、
    **キーワードが固定値「ハンドル」のまま**だった。
    抽選値が XENON の回で、ナビが正しい報告に
    『キーワードは**違うみたいです**』と差し戻した。

    `${sim_keyword}` を追加して抽選値から引くようにした。
    **台本の固定値は1つ直すだけでは済まない** — 抽選値と
    突き合わされる報告を洗い出す。

72. **第一声の前倒しを全廃した** (ADR N-49):
    決定71 で「事故になる情報だけは第一声に入れる」と決め、
    206 綱渡り の危険位置だけを残していた。その結果:

    > こちらヒバリです、(略)**ダイヤル2で止まるな。**
    > ランプはどうなってますか?

    **いきなり数字を言われる違和感**が勝った。
    プレイヤーは**まだダイヤルに触っていない**ので、
    報告を待つ間に事故は起きない。**急ぐ理由が実際には無かった。**

    **危険位置は回す指示と一緒に伝える形にした:**

    > ランプが1つですね、了解です!ダイヤルを3に合わせてください。
    > **ただ、2で止めると危険なので**一気に回してくださいね

    **回せと言う前に危険位置だけを告げない** — 何のための数字か分からない。
    実測5回中5回で上の形になった。

    #### 例外を持たない規則にする

    `prompt.toml` は全ステージ共通なので、規則を1つ足すたびに
    **全ステージの第一声が変わる**。「例外的に前倒ししてよい情報」を
    設けると、**その例外がどのステージで発火するか読めない**:

    | 回 | 例外の書き方 | 巻き込まれたステージ |
    |---|---|---|
    | 決定71 前 | 装置に現れない情報 (危険位置・押すボタンの色・ダイヤルの数字) | 304 が第一声で押させた |
    | 決定71 | 事故になる情報 (危険位置) | 102 がダイヤルを先に言った |
    | **決定72** | **例外なし** | — |

    3回とも**ステージ側は正しく、規則が広すぎた**。
    例外を消して初めて全ステージが揃った。

    回帰の `procedure_before_observation` も
    **危険位置を持つステージの除外をやめ、全ステージ対象**にした。
    正規表現は「N に合わせろ」だけでなく
    **「N で止まるな」も拾う**ようにしてある(旧形式を捕まえるため)。

    `MustMention` は**入り口の発話のどれかに1回**出れば満たす形なので
    (決定69)、206 の危険位置の検査はこの変更でもそのまま働く。

73. **答え合わせできないことを判定させない** (ADR N-50):
    205 速さくらべ の誤答の差し戻しについて
    「『違います』と断定するのは、装置が見えていないナビゲーターの
    立場としておかしい」という指摘から始まった。

    言い方を和らげる過程で、**もっと重い問題**が見つかった:

    > **P** 数えてみました。緑色だと思います
    > **N** 緑色ですね、了解です!**それが4番目です、その色の線を切ってください**

    **誤った色のまま切らせている。** 切った線は戻せず即爆発する。

    #### 4通り試してゼロにならなかった

    | `answer` の書き方 | 誤答を通した |
    |---|---|
    | 「照合に使うこと」(元の形) | 8回中1回 |
    | 「内心で照合し、表に出さない」 | 6回中1回 |
    | 「一致しないときは絶対に切らせない」 | 8回中1回 |
    | 「${cut}色以外なら切る指示を出してはいけない」 | 8回中2回 |

    強く書くほど良くなるわけでもなかった。
    **爆発に直結する以上、確率的な対策では足りない。**

    #### `keep_cut_secret` は逆効果だった

    色名をプロンプトから伏せてみたところ、**8回中5回**に悪化した。
    照合できなくなっただけで、**判断は依然ナビゲーターがしていた**ため。

    **205 の正解は紙資料に無い。** 203 ブループリント (決定64) のように
    「任せる」が成立するのは、プレイヤーが資料で確定できるから。
    205 は点滅を数えるしかなく、**ナビが伏せても誰も確定できない**。

    #### 照合そのものをやめた

    色名を報告させず、正誤も告げない形にした。ナビゲーターの仕事は
    **順位を伝える・数え方を助言する**の2つで、
    どの色かはプレイヤーが決める。色を言ってきても
    『数え直して自信が持てたら切ってくれ』と委ねる。実測8回中8回で改善。

    副次的に、**元の指摘 (「違います」と断定する)も消えた** —
    正誤を告げなくなったので断定する場面自体が無くなった。

    #### 他の11ステージは照合してよい

    `${cut}` を照合に使うステージは他にもあるが、いずれも
    「点灯しているランプと同じ色」のように**装置を見れば一意に決まる**。
    **205 だけが「4色を速さで並べ替えて N 番目」という、
    数え違いが起きる前提の課題**だった。
    誤答を検証する台本 (`sim_wrong_color`) を持つのも 205 だけ。

74. **断り方は「知らない」と「言わない」を区別する** (ADR N-6):
    203 ブループリント で色を求められたときの返し:

    > 色はこっちに見えないから**教えられないです**、
    > そちらで決めて切ってくださいね!

    **「教えられない」は知っているのに伏せているように聞こえる。**
    実際にはナビゲーターは回路図を持っておらず、**本当に分からない**。

    『**分からない**』『こっちからは**見えない**』と**知り得ない**ことを言い、
    あわせて**資料を確認してもらうよう頼む**。断って終わりにしない。

    **例文が原因だった。** 指針には

    > 『こっちに${sheet_circuit}は無いんだ、そっちで確認して切ってくれ』
    > 『端子番号までしか分からない。色は君が見て決めてくれ、任せる』

    と2つ並べていたが、**先頭がなぞられ**、しかも「教えられない」という
    元の指針に無い語まで混ざった。決定67 と同じで、
    **例文を消して性質だけ書く**。実測5回中5回で改善した。

75. **201 復唱も押し切ったらランプを変える** (ADR C-13):
    103 コール&レスポンス で使っていた `reveal_cut_on_complete` を
    201 にも入れた。ただし**見え方は変える**:

    | | 押下中 | 押し切ったあと |
    |---|---|---|
    | **103** | 報告用=点灯 + 切る線=点滅 の**2色** | 切る線だけ点灯 |
    | **201** | 報告用の**1色だけ** | 切る線だけ点灯 |

    103 は「報告した色と切る色が違う」という気づきが要点なので
    最初から2色見せる (決定58 相当)。201 で同じにすると**重複**するうえ、
    持ち味である**列を聞いて覚えること**が散漫になる。

    201 は押し切って初めて切る線が現れるので、
    **『押し終わったらランプが変わった』という変化の報告**が生まれ、
    無線の往復が一つ増える。

    **ナビゲーター知識に「押す前の色は切る線ではない」と明記する。**
    書かないと、押す前に見た色をそのまま切らせかねない。
    `answer`・`procedure`・`hint_l2`・`hint_l3` の4箇所に入れた。

    押下色からは `${cut}` に加えて **`${lit}`(報告用の色)も外す** —
    報告した色をそのまま押すと対話の一往復が消える (103 と同じ)。
    候補が3色に減るがハードの8色列でも**同色3連続は発生しない**
    (200シードで最長2連続。`color_seq` が抑止している)。

76. **繰り返しの操作は「繰り返し」まで言う** (ADR N-48):
    204 色合わせ の説明が日本語として通らないという指摘:

    > 1つ光ってますね、了解です!**同じ色のボタンを押してください。**
    > そして最後に押した色を覚えておいてくださいね

    204 は**ランプが1つずつ光り、押すと次の色に変わる**繰り返しの操作。
    上の言い方は**一回きり**に聞こえる。そのうえ
    「最後に押した色」は、**一回しか押さないと思っている相手には
    意味が通らない**。

    **原因は `hint_l1` の必須項目の書き方。**

    > (1) **光っているランプと同じ色のボタンを押す**こと
    > (2) **最後に押した色を必ず覚えておく**こと

    (1) が**一回の動作**で書かれており、繰り返しを表す
    「押すと次の色に変わる」は**「余裕があれば添える(削ってよい)」**扱いだった。
    決定70 (102 の「押しながら切る」) と同じで、
    **構造が必須項目に入っていなかった**。

    #### 覚えるタイミングも間違えていた

    繰り返しを必須にしたあと、こう出た:

    > それを繰り返してランプが全部消えた**ら、最後に押した色を覚えておいて**

    **消えたあとに覚えることになり手遅れ。** 全消灯すると装置に
    手がかりが残らないので、覚えるのは**押している最中**。
    『**押しながら**最後に押した色を覚えておく』と、
    (1)(2) を別々の指示として言う形にした。

    #### 配慮を同じ発話に足さない

    必須情報が3つあるので60字は超える(実測68〜83字。ADR N-22)。
    そこへ『急がなくてよい』を添えると**99字**まで伸びた。
    `hint_l1` から外し、押し始めたあとの発話へ回した。

    最終的に6回中6回で繰り返しが伝わる形になった。

77. **落とすと詰む一言は `must_say` で独立させる** (ADR N-51):
    決定76 で繰り返しは伝わるようになったが、今度は
    **「最後に押した色を覚えておく」が8回中2回落ちた**。
    押し切ると全消灯するので、そのまま詰む。

    `hint_l1` には「**(2) を落とさない**」「先に言い当てられても足す」と
    書いてあったが守られない。**指針が長くなるほど末尾が落ちる。**

    #### 散文をやめ、プロンプトの構造にした

    ナビゲーター知識に `must_say` を書くと、プロンプトへ
    `## この課題で必ず言うこと` として**独立したブロック**で出る
    (`navigator_prompt.go`)。実測 6/8 → **7/8**。

    #### `hint_l1` を短くしたら悪化した

    `must_say` を足したので `hint_l1` の重複を削ったところ、
    **3回中1回まで落ちた** — 繰り返しの説明ごと消えた。

    | 構成 | 「覚え」が出た |
    |---|---|
    | `hint_l1` 整理のみ | 6/8 |
    | `must_say` + `hint_l1` **短縮** | **1/3** |
    | `hint_l1` 復元 + `must_say` | **7/8** |

    **`must_say` は上乗せであって置き換えではない。** 両方に書く。

    #### 書くのは「落とすと手詰まりになるもの」だけ

    何でも入れると**また埋もれて同じことになる**。現在は 204 のみ。
    未設定のステージでは見出しごと出さない
    (`TestMustSayAbsentWhenUnset` で担保)。

    #### 実機には L2 の救いもある

    `hint_l2` に「押している最中に念押しする」と書いてある。
    台本は L1 の次が押し切ったあとのプレイヤー報告なので
    シミュレーションには現れないが、**実機では押している最中に
    L2 の発話機会がある** (プレイヤーが押しながら話しかけてきた場合)。L1 で落ちても救える。

78. **5人目のキャラクター「モズ」を追加した** (ADR N-21b・N-17):

    コテコテの**大阪弁**を話す30代男性。現場叩き上げの**段取り屋**。
    `navigator/characters/shrike.toml`。TTS は `Algieba`
    (既存4キャラ・カラス・混線30ファイルのいずれとも重複しない。
    `TestVoicesDoNotCollideWithNavigators` で担保)。

    #### 象限は「段取り」に置いた

    決定28 の「何を見ているか」で重ならないことを先に確認した。
    既存4人は 心理(フクロウ) / 同じもの(ヒバリ) / 装置(アオサギ) /
    全体を外から(ツグミ)。モズは**作業の段取りと区切り** —
    「今どこまで済んで、次に何を1つやるか」だけを見る。

    伴走するヒバリと近く見えるが**向きが違う**。
    **ヒバリは一緒に考え、モズは分けて渡す**(横から仕切る)。

    #### 安心のさせ方は「軽口で緊張を抜く」

    決定43 で4人に別々の型を書いたので、5人目も別の型が要る。
    モズは**相手の力みを笑って外してから**段取りへ入る。

    **ツグミの「重大さを薄める」と紛らわしいので、距離で分けた**。
    ツグミは他人事で突き放すが、**モズは当事者として仕切っている**。
    笑わせてから引っ張るので距離は近い。

    **請け合うのは自分ではなく段取りのほう**にしてある
    (「手順どおりいったら開く」)。「わしがついたる」「一緒にやろ」は
    ヒバリの型なので使わせない。

    #### 方言は「使わせない語」を先に書いた

    口調の指定だけでは、生成AIが「大阪弁」から**芝居がかった商人口調**を引く。
    禁止語を列挙してある:

    | 禁じたもの | 理由 |
    |---|---|
    | 「〜でおま」「〜まっせ」「〜だっせ」 | 芝居がかった商人口調。現場の職人ではなくなる |
    | ~~「知らんけど」~~ | ※ **決定79 で解禁した**(下記) |

    #### ※ 「知らんけど」の全面禁止は決定79 で覆した

    当初は**絶対禁止**にした。ヒントに付くと「ナビゲーターも自信がない」と
    読めるため。しかし**キャラ付けが弱まる**という指摘を受けて撤回した
    (ユーザー判断)。大阪弁の持ち味であり、語ごと封じると
    「大阪弁を話すだけの人」に寄る。

    **禁じるのは語ではなく付ける場所**に改めた:

    | 付けてよい | 付けさせない |
    |---|---|
    | 軽口・相槌・場を和ませる一言 | **切る線**(戻せない・即爆発) |
    | 手順に関わらない発話 | **ダイヤルの位置・ボタンの色・押す順番** |
    | | **危険位置の警告** |

    根拠は ADR N-37(迷いには「待て」)。**切った線は戻せない**ので、
    取り返しのつかない操作の前で迷わせる語が付くのだけが問題であって、
    語そのものは問題ではなかった。**軽口の場所は既に分けてあった**
    (緊迫時・誤操作直後は軽口を落とす)ので、同じ切り方を適用した形。

    > **一般化**: 方言・口癖の定型が実害を持つのは**特定の場面だけ**のことが多い。
    > 語ごと禁じる前に、**害が出る場面を切り出せないか**を先に見る。
    > 語ごと禁じるとキャラクターが痩せる。

    #### 軽口は分量と場面を決めた

    「軽口が出る」とだけ書くと**毎発話に入って煩くなる**(決定14 と同じ構図で、
    シートに書いたことは全部出る)。

    - **1発話につき多くて一言**
    - **緊迫時と誤操作の直後は軽口を落として段取りだけ** —
      ここで茶化すと信用を失う
    - **爆発時は口が止まる**。ずっと減らなかった口が止まるのが、
      このキャラの動揺の出し方。仕切り屋なのに次の手が出てこない形にした

    #### 未検証

    **文字シミュレーションは未実施**。§6 の表に `未実測` として入れてある。
    方言は字数が伸びやすく(語尾が伸びる)、60文字制約と
    軽口の分量がどう衝突するかはこれから見る。

    ```bash
    go test -run TestSimulateAllStages -simulate -sim-character shrike -v
    ```

    #### ツグミとの入れ替えは未決

    ユーザーからツグミと入れ替える案が出ている。現時点では**5人体制で追加**し、
    入れ替えは別途決める。**入れ替える場合、決定2(ツグミの音声)・
    決定31(命令形を使わないキャラでの口調写し検出)の前提が変わる** —
    ステージ知識の口調写しはツグミで最初に出るため、
    外すなら検出役を別のキャラへ移す必要がある。

79. **「知らんけど」は語ごと禁じず、付ける場所で禁じた** (ADR N-21b。決定78 を一部覆した):

    決定78 でモズに**「知らんけど」を絶対禁止**と書いた。ヒントに付くと
    「ナビゲーターも自信がない」と読めるため。

    **撤回した。キャラ付けが弱まる**(ユーザー判断)。大阪弁の代表的な語で、
    語ごと封じると**「大阪弁を話すだけの人」**に寄る。軽口で緊張を抜くのが
    このキャラの安心のさせ方なので、軽口の語彙を削るのは効き目に直撃する。

    #### 害が出るのは場面のほうだった

    禁止の理由は「指示の信頼性が消える」だったが、これは**指示に付いたとき**の話。
    軽口に付くぶんには何も壊れない。

    | 付けてよい | 付けさせない |
    |---|---|
    | 軽口・相槌・場を和ませる一言 | **切る線**(戻せない・即爆発) |
    | 手順に関わらない発話 | **ダイヤルの位置・ボタンの色・押す順番** |
    | | **危険位置の警告** |

    根拠は ADR N-37(迷いには「待て」)。**切った線は戻せない**ので、
    取り返しのつかない操作の前で迷わせるのが問題であって、語自体は問題ではない。

    **軽口は既に場所で分けてあった**(決定78 —「緊迫時と誤操作の直後は
    軽口を落として段取りだけ」)。同じ切り方を語にも適用しただけで、
    新しい仕組みは要らなかった。

    #### 一般化

    **方言・口癖の定型が実害を持つのは特定の場面だけのことが多い。**
    語ごと禁じる前に、**害が出る場面を切り出せないか**を先に見る。
    語ごと禁じるとキャラクターが痩せる。

    これは決定29(「わずかに/稀に」という**程度**の指定は効かない)とは別で、
    **場面は判定できる**ため指示として成立する(ADR N-33 —
    頻度ではなく**判定できる条件**で分岐させる)。

80. **トリガー指示の例文が全キャラの口調を消していた** (ADR N-18・N-32):

    モズのシミュレーション(初回)で、`stage_cleared` の発話だけが
    **18ステージ中17回、標準語に戻った**。

    ```
    N> [calm] うまく切れたか? ランプはどうなっている? どうぞ
    ```

    大阪弁が跡形もない。しかも**毎回ほぼ同じ文**だった。

    #### 原因は共通トリガーの例文

    `prompt.toml` の `stage_cleared` に例文が書いてあった:

    > **まず切れたかを確認し、続けて次のランプの状態を尋ねてください**
    > (例:「うまく切れたか? ランプはどうなっている?」)

    **トリガー指示は全キャラ共通**なのに、例文がフクロウの口調だった。
    決定31(ステージ知識に命令形を書くとツグミが崩れる)と同じ構図が、
    **ステージ知識ではなくトリガー指示で起きていた**。

    #### モズだけの問題ではなかった

    ツグミでも確認したところ、**3回中2回**が例文の丸写しだった。

    ```
    N> [calm] うまく切れたか? ランプはどうなっている? どうぞ
    ```

    ツグミは**命令形を使わない**のが定義(決定31 の検出役そのもの)。
    「〜か?」の直接的な問いは口調に反する。
    **フクロウだけが無傷**だった — 例文が元々フクロウの口調だったため。

    つまり**例文を置いた時点で、そのキャラの口調に全員が寄っていた**。
    モズを入れたことで、方言という**目に見える形**で露呈しただけ。

    #### 直し方は session_start と同じ

    `session_start` は既に**キャラシートへ委ねる**書き方になっており、
    モズの第一声は**18/18 すべて大阪弁**で出ていた。同じ形にした。

    - `stage_cleared` … 例文を削除し、「キャラシートの口調で組み立てろ」と明示
    - `player_message` … 同じ理由で例文(「ゼロだな、次は4に合わせろ」= フクロウ)を削除。
      形(「復唱 + 次にやること1つ」)だけ残し、言い回しはシートの「応答」例に倣わせた

    #### 結果

    | | 修正前 | 修正後 |
    |---|---|---|
    | モズ `stage_cleared` が大阪弁 | **1/18** | **18/18** |
    | 文面のばらつき | ほぼ同一文 | ステージごとに変化 |

    ```
    N> [calm] 線は切れたか? ほんで次のランプはどうなっとる? どうぞ
    N> [relieved] 線はきれいに切れたか? ほな次いくで、ランプどうなっとる? どうぞ
    ```

    ツグミも「〜かな」「〜だね」に戻り、フクロウは影響なし(元々その口調)。

    #### 一般化

    **`[triggers]` は全キャラ共通のブロックである**。ここに例文を書くのは
    ステージ知識に口調を書くのと同じで(決定31)、**非対応のキャラが崩れる**。
    書くなら**何をするか**だけにして、**どう言うか**はキャラシートへ委ねる
    (決定43 と同じ切り分け)。

    **例文が無いと出力が安定しない場面もある**(決定14)。その場合は
    トリガーではなく**キャラシート側に**、そのキャラの口調で置く。

81. **モズの文字シミュレーション結果** (ADR V-1):

    全18ステージ・110発話。**色漏れ0件・不正な表情タグ0件・必須情報の欠落0件**。

    | 項目 | 実測 |
    |---|---|
    | 平均文字数 | 38.4 字(フクロウ28.3 / ツグミ33.4 / アオサギ33.7 / ヒバリ38.7) |
    | 最長 | 95 字(205 速さくらべ) |
    | 目安超え | 4/110 発話 (4%) |

    **モズは字数の重いほうに入る**。ヒバリとほぼ同じで、語尾が伸びる
    (「〜やな、了解」「〜してみ」)ぶん標準語の3人より長い。
    §6 の表へ実測値を入れた。

    #### 205 の長さはモズ固有ではない

    唯一の所見は 205 速さくらべ の 95字。**全キャラで長い**:

    | キャラ | 205 の最長 |
    |---|---|
    | アオサギ | 62 字 |
    | フクロウ | 70 字 |
    | ヒバリ | 91 字 |
    | モズ | 95 字 |

    205 は**基準色の除外・速い順に並べる・4番目**を1発話で伝える必要があり、
    構造的に長い。ADR N-22 のとおり**削ると詰む情報**なので、
    切り詰めない。キャラクターの問題としては扱わない。

    #### 方言は崩れなかった

    懸念していた口調の崩れ(標準語への回帰・商人口調)は
    **トリガーの例文を直したあとは出ていない**(決定80)。
    「知らんけど」も、解禁後の実行で**手順に付いた例は出ていない**。

    #### 残るのは音声

    文字では確認できない**声質・イントネーション**が未検証。
    `Algieba` が関西のイントネーションをどこまで再現するかは実機で聴く。
    **TTS が方言を標準語アクセントで読む可能性**があり、そこは
    `tts_style` の調整余地として残る。

82. **`session_ready` も例文を外し、キャラシートへ委ねた** (ADR N-21c の適用):

    決定80 で `stage_cleared` / `player_message` の例文を外したが、
    **`session_ready` を見落としていた**。「こちらフクロウ。待機完了」という
    例文が残っており、モズが**標準語で名乗っていた**
    (「こちらモズ。待機完了。」11字)。

    **短い発話ほど例文の影響が強い。** 11字では崩す余地がなく、
    名前を差し替えただけの丸写しになる。

    直し方は決定80 と同じだが、**キャラシートに「待機完了」の例が
    どこにも無かった**ため、委ね先を先に作る必要があった。
    **5人全員のシートに追加**した:

    | キャラ | 待機完了 |
    |---|---|
    | フクロウ | 「こちらフクロウ。準備はできている」 |
    | ヒバリ | 「こちらヒバリです!いつでもいけます!」 |
    | アオサギ | 「こちらアオサギです。待機に入りました」 |
    | ツグミ | 「……ああ、聞こえてる。こっちはいいよ」 |
    | モズ | 「こちらモズや。準備万端、いつでもいけるで」 |

    あわせてトリガー側に**「『待機完了』という語をそのまま使う必要はない」**と
    明記した。この語自体が報告口調で、大阪弁や独り言口調と噛み合わない。

    実測 6/6 で大阪弁になった。

83. **終幕 (解除成功・爆発) のシミュレーションを追加した** (ADR V-1):

    `TestSimulateAllStages` は課題の進行だけを見るため、
    **`defused` / `exploded` を一度も通らなかった**。だがこの2つは
    **キャラクター差が最も大きい場面**で、指示もキャラシートへ
    委ねてある (決定47b)。`navigator_ending_sim_test.go` を追加した。

    ```bash
    go test -run TestSimulateEndings -ending -ending-character shrike -v
    ```

    直前の交信 (迷いを見せた場面を含む) を会話ログとして渡し、
    両トリガーとも3回ずつ生成する。禁止語 (「どうぞ」「お疲れ」
    「次は」など)・表情タグ・長さを機械的に検査する。

    #### 例文を書いたら3回とも同じ台詞になった

    モズの初回結果:

    ```
    #1 やったな、最後まで手順が綺麗に噛み合ったで。ええ運びやった。ほな、冷たいもんでも飲みに行こか、お疲れさん
    #2 やったな、最後まで手順が綺麗に噛み合ったで。お前のその落ち着きが…。ほな、冷たいもんでも飲みに行こか、お疲れさん
    #3 やったな、最後まで手順が綺麗に噛み合ったで。ええ運びやった、さすがやわ。ほな、冷たいもんでも飲みに行こか。
    ```

    **前半がほぼ同一**。原因はシートの指針に書いた括弧書きの例
    (「飯でも食い行こか」「肩の力抜き」) と、「最後まで手順が崩れんかった」
    という**言い回しそのもの**だった。ADR N-29 のとおり、
    **毎回変えたい台詞に例文を置くと先頭が固定される**。

    比較したフクロウは3回とも違う締め方をしていた
    (「無事に戻れて何よりだ」「ゆっくり休め」「よく耐え抜いたな」)。
    フクロウのシートは**何を言うか**しか書いていない。

    例文を外し、**方向だけ**を書く形に直した(労をねぎらう/飲み食いに誘う/
    肩の力を抜かせる、から毎回ちがう方向を選ぶ)。前半のばらつきは戻った
    (「完璧な段取り」「見事なもんや」「やるやないか」「あんたの勝ちや」)。

    **ただし締めの「飲みに行こか」+「お疲れさん」は4/4で残った。**
    方向を3つ挙げても飲み食いに寄る。**残課題**として記録する。

    #### 爆発は狙いどおりだった

    ```
    #1 おい、聞こえとるか。返事し……あかん、動かん。……くそっ、いま行く。
    #2 おい、聞こえとるか……。返事しや……。あかん、行くで。
    #3 おい、聞こえとるか……。返事しろ……！
    ```

    シートに書いた「軽口が消える」「段取りが崩れる」「自分が現場へ走る」が
    そのまま出た。**19〜44字と短く、言葉が途切れる**のも意図どおり。

84. **「開く」で解除を指さない** (モズの言い回し):

    モズの第一声に書いた「段取りどおりいったら必ず**開く**」を
    「必ず**解ける**」へ直した(ユーザー指摘)。

    「開く」は大阪弁ではなく**標準語の比喩**(金庫・錠前が開く)で、
    段取り屋という設定から書いた。意味としては解除を指していたが、
    **この装置は風船入りの模擬爆弾で、蓋も錠前も開けない**ため
    通じにくい。第一声は**全ステージで毎回出る**ぶん影響が大きい
    (実測 18/18 でそのまま複写されていた)。

    シートに「**「開く」で解除を指さない**。仕掛けを**解く**作業。
    「解ける」「止まる」「解除できる」と言う」と明記した。

85. **302 で解読した語そのものを教えていた** (ADR N-45):

    実測でナビゲーターが**正解の語を直言**した(ユーザー指摘):

    ```
    P> 読めました。デルタです。どうぞ
    N> デルタやない、ECHOや。もっぺん解読し直してみて。どうぞ
    ```

    **色漏れ検査に掛からなかった**。検査対象は切る線の色名だが、
    ここで漏れたのは**モールスを解読した語**(中間の答え)で、
    別の変数だったため。

    #### 302 だけが持つ穴だった

    `procedure` には「一致しなければ**色名を出さずに**引き直させる」と
    書いてあったが、**守っているのは色だけ**。誤答が「語」のときに
    訂正を禁じる文が無かった。

    | ステージ | 中間の答え | 状況 |
    |---|---|---|
    | 202 暗号電文 | 語 | **色しか照合しない**ので同じ穴が無い |
    | 305 ローマ字電文 | **語=色名** | 語を言う=色漏れなので既存の検査が拾う |
    | 302 ジャミング | **語**(ECHO 等) | **語だけが無防備**だった |

    #### 直し方

    ユーザー指示のとおり、**「資料を照合して切れ」と言い切る形**にした。
    あわせて禁止を明記:

    - **解読した語が違っていても正しい語を教えない**。
      綴りの訂正も、頭文字だけ教えることも禁止
    - 差し戻すのは**読み取りのほうだけ**(「もういっぺん読み直して」)
    - **理由は述べない**(ADR N-45)

    台本にも `MustNotMention: ["${navi_word_guess}"]` を足して、
    語が出たら所見になるようにした。修正後:

    ```
    N> デルタやない、もういっぺんモールスを読み直してみてくれ。どうぞ
    ```

86. **時間を追う課題で「切る」動作が落ちていた** (ADR N-48。303・304):

    ユーザー指摘で2件見つかった。どちらも**条件は言うが動作を言わない**形。

    #### 303 追いかけダイヤル — 「合わせてから切る」では間に合わない

    ```
    N> 5に合わせたな、了解。ほな、点滅しとる色の線を切ってみ。
    ```

    判定は `digit == rotary_position` を**切った瞬間**に見る
    (`timer_digit_rule.h`。猶予1秒)。十の位は減り続けるので、
    **合わせてから切ると、切る頃にはずれている**。

    指針が「ダイヤルをその数字に合わせるよう促す」と**一度きりの動作**で
    書かれており、**追尾**が表現されていなかった。直した:

    - 「合わせてから切る」ではなく**「合っている状態で切る」**と言わせる
    - **「十の位が減ったらダイヤルも回し直す」を必ず添える** —
      ここが「追いかけダイヤル」の本体
    - `briefing` / `procedure` / `hint_l2` / `hint_l3` の4か所を揃える

    修正後は追尾と瞬間の両方が出た:
    「十の位は減っていくから、変わったらダイヤルも回し直してな」
    「十の位が一致したその瞬間に切るんや」

    #### 304 我慢比べ — 「見ててや」で終わっていた

    ```
    N> 小数点のすぐ左の数字が9になった瞬間を見ててや。
    ```

    **見ているだけでは何をするか分からない。** 押さえたまま待ち続けて
    時間切れになる。`procedure` が「**という条件を伝える**」と
    書かれていたのが原因で、条件として渡すと動作が落ちる。

    **数字を告げて終わる形を名指しで禁止**した
    (「${digit}になった瞬間を見ててや」「${digit}を狙え」
    「${digit}になるまで待て」)。正しい形は
    「${digit}になった瞬間に線を切る」。

    最初は `procedure` だけ直したが **L2 で再発**した
    (L2 は `hint_l2` が支配する)。`hint_l2` にも同じ禁止を書いて 3/3 で解消。

    #### 一般化

    **条件と動作を別々に書くと、動作のほうが落ちる。**
    「〜という条件を伝える」「〜のタイミングを伝える」と書かず、
    **「〜になった瞬間に切る」と動作までつなげた形**で指針に書く
    (決定70・決定76 と同じ)。**タイミングを扱う課題では特に出やすい** —
    条件の説明が長くなるぶん、末尾の動作が削られる。

87. **302 の誤答は「疑いをかけて確かめ直させる」** (ADR N-50。決定85 を改めた):

    決定85 で正解の語を教えるのをやめたが、直した先が
    **断定して突き放す形**になっていた(ユーザー指摘):

    ```
    N> デルタやない、もういっぺんモールスを読み直してみてくれ。どうぞ
    ```

    **「デルタやない」は装置を見ていないナビが断定している。**
    ADR N-50(判定できないことは委ねる)に触れる。
    205 で「正誤を告げない」と決めたのと同じ問題が、
    別のステージで別の形で出ていた。

    #### 205 とは事情が違う — 突き放しきれない

    205 は**正誤に一切触れない**形にした。だが 302 で同じことをすると、
    **誤読したまま切って即爆発する**。

    | | 205 速さくらべ | 302 ジャミング |
    |---|---|---|
    | 正解の確定手段 | **点滅を数えるしかない** | **資料1で確定できる** |
    | ナビが黙ると | 誰も確定できない | **自力で気づける** |
    | 採った形 | 正誤に触れない | **疑いをかけて資料へ戻す** |

    302 は 203 ブループリントと同じで、**プレイヤーが資料で確定できる**。
    だから「任せる」が成立する — ただし**任せっぱなしにはしない**。

    #### 採用した形

    ユーザー提案の「本当にデルタか?念のため確認して」を採った。
    **断定せず、しかし『違うらしい』とは伝わる**言い方。

    ```
    N> 本当にデルタか? 念のためもういっぺん資料1で確かめてみ。どうぞ
    ```

    禁止を4つに整理して書いた:

    | 禁止 | 理由 |
    |---|---|
    | 正解を教える(「エコーや」) | 中間の答え。言うと課題が消える (N-45) |
    | 綴りの訂正・頭文字だけ教える | 同上 |
    | **断定して突き放す**(「それは違う」) | **装置を見ていない立場で断定している (N-50)** |
    | 理由を述べる(「3文字目が短点や」) | 当てはまらない材料を当てはめる (N-45) |

    #### 正解時に認めるかも検証した

    疑いをかけるのが**違っているときだけ**か確かめる必要がある。
    毎回疑い返すと、正しく読めても先へ進めない。
    台本に**正しい語を報告するターンを追加**した。実測 3/3:

    ```
    P> 読めました。デルタです。          → N> 本当にデルタか? 資料1で確かめてみ
    P> 確かめ直しました。ECHOでした。    → N> ECHOやな、了解や。頭文字を引いて…
    ```

    #### 検査の免除を足した

    正解報告のあとの「ECHOやな、了解」は**復唱**であって漏洩ではない。
    だが `MustNotMention` は無条件に照合していたため、
    **正当な復唱を所見にしてしまう**(色名の検査には既に同じ免除がある)。

    `simPlayerSaid` を足し、**プレイヤーが台本で先に言った語だけ**免除した。
    免除が広すぎるとナビが自分から言った語まで見逃すので、
    `TestMustNotMentionExemptionIsNarrow` で**両方向**を担保する
    (言った語は免除される / 言っていない語は免除されない)。

    #### 一般化

    **「答えを言わない」の直し方は2通りあり、選ぶ基準は
    「プレイヤーが自力で確定できるか」。**

    - **確定できる**(資料がある) → **疑いをかけて資料へ戻す**。302・203
    - **確定できない**(数えるしかない) → **正誤に触れず判断を委ねる**。205

    どちらも**断定しない**点は同じ。ナビは装置を見ていない (N-50)。

88. **モズの爆発時を「虚をつかれる」形に変えた** (ADR N-25。決定78 を覆した):

    決定78 でモズの爆発を「呼びかける → 軽口が消える → 現場へ走る」と書いたが、
    **フクロウとほぼ同じだった**(ユーザー指摘)。実測でも 8/8 で呼びかけ、
    4/8 で現場へ走っていた。**方言しか違わない**状態。

    #### 空いていた枠

    既存4人は次を占めている。**「虚をつかれる」だけが空いていた**:

    | キャラ | 爆発時 |
    |---|---|
    | フクロウ | 呼びかけ → 現場へ走る |
    | ツグミ | 呼びかけ → 受け流して切る |
    | アオサギ | 呼びかけず手順へ切り替える |
    | ヒバリ | 返事を待たず本音が漏れる |
    | **モズ** | **虚をつかれて言葉を失う。動かない** |

    段取り屋が**段取りの外のことに遭って反応が追いつかない**形にした。
    三段: (1) いつもの軽口が反射で出かける (2) 途中で声が死ぬ
    (3) **段取りが無くなったこと**に触れて途切れる。

    **モズだけが呼びかけも手配もしない。** 動けないから怖い、という差別化。

    #### 他キャラと紛れないよう4つ禁じた

    | 禁止 | 侵す相手 |
    |---|---|
    | 安否確認 (「聞こえとるか」「返事し」) | フクロウ・ツグミ |
    | 現場へ走る (「今すぐ行く」) | フクロウ |
    | 本音・含みを漏らす | ヒバリ |
    | 手順を続ける (「ほな次は」) | アオサギ |

    漏れるのは**いつもの反射(軽口)**であって隠していた気持ちではない、と
    書き分けてヒバリと分けた。

    #### 「おい」は呼びかけではなく驚きの声

    禁止しても「おい」が出続けた。**この語自体は呼びかけとは限らない** —
    「おい、嘘やろ」は自分の口から漏れる驚きで、モズらしさでもある。
    **「相手の返事を求める文にしない」**という条件に書き換えて解決した。
    語を禁じるのではなく**用法で分ける**(決定79 と同じ形)。

89. **終幕テストが `RecentEvent` を渡していなかった** (テストの不備):

    決定88 の調整中、**8回中8回が直前の色名から話し始める**現象が続いた。

    ```
    #1 青か、ほなそれを切れ――おい、待て、嘘やろ…
    #2 青か、ほなそいつを切れって、おい……？
    ```

    禁止を強めるほど悪化した(ADR N-32 のとおり、引用した文言が手本になる)。

    **原因はテスト側**。`navigator_ending_sim_test.go` が `RecentEvent` を
    渡しておらず、プロンプト上の**一番新しい事実が
    「プレイヤーが青で行くと言った」**になっていた。爆発が起きたことが
    どこにも書かれていない状態で「爆発に反応しろ」と指示していた。

    本番 (`game_coordinator.go`) は必ず渡している:

    ```go
    c.speakAsyncThen(ctx, sender, session, "exploded",
        "解体は失敗し、装置が起動してしまった。失敗を受け止めるメッセージを返す。", ...)
    ```

    テストへ同じ文面を渡すよう修正した。**シミュレーションは本番と同じ
    入力で回さないと、存在しない問題を追いかけることになる。**

    #### それでも残ったので指示の位置を変えた

    `RecentEvent` を足しても 5/8 で色名が出た。**会話ログは指示より近い**。
    キャラシートではなく**トリガー指示 (`exploded`) 側**に
    「直前の交信の語をなぞって始めない」と書いて 2/8 まで下がった。

    あわせて**「プレイヤーの選択を蒸し返さない」**も禁じた —
    「青やて言うたやんか」は**責める言い方**になり、ADR N-25 に反する。

    トリガー側に書いたので**全キャラに掛かる**。他4人で回帰は出ていない
    (フクロウ・ツグミ・アオサギ・ヒバリとも従来どおりの形)。

90. **「段取りが消えた」は日本語として成立していなかった** (決定88 の修正):

    決定88 のあと、モズの爆発時が **「段取りが、消えた……」** と言っていた
    (ユーザー指摘)。**段取りは組み立てた手順のこと**なので、
    消えたり切れたりしない。崩れる側なら「狂う」「台無しになる」。

    原因は**私がシートに書いた指示文**だった:

    > (3) 最後は**「段取りが無くなったこと」**に触れて終わる

    「無くなった」と書いたので「消えた」が出た。意図は
    **次の手が出てこない**ことだったので、そう書き直した。
    あわせて「消えた」「切れた」を名指しで禁じ、
    崩れる側の言い方(「狂うた」「台無しや」)を示した。

    #### 指示文の日本語が、そのまま発話の日本語になる

    キャラシートは**発話例だけでなく指示文も写される**。
    「〜こと」「〜な状態」のような抽象名詞で書くと、
    生成AIがそれを動詞化して**不自然な言い方を作る**。
    **指示文自体を、そのまま口に出して自然な日本語で書く。**

    #### 禁止を重ねたら今度は同じ文になった

    修正後、禁止事項(責める語法・身体描写・呼びかけ・色の蒸し返し)を
    重ねた結果、**8回中7回がほぼ同一文**になった。決定83 と同じ現象で、
    **禁止だけ増やすと安全な一文へ収束する**。

    三段のうち **(2) 声が死ぬ** が実質消えていたので、
    「三段を全部使う」「締めも毎回ちがう言葉にする」を足して回復させた。

    > **禁止と自由度はトレードオフ。** 片方だけ足すともう片方が壊れる。
    > 禁止を足したら**ばらつきが残っているかを必ず確認する**。

    #### 言い換えて再発するものは機械で拾う

    「耳鳴り」を禁じたら **「耳が元に戻らん」** に化けた(ADR N-32)。
    **モズは無線の向こう側にいて爆風も音圧も届いていない** —
    身体の被害を語ること自体が成立しない。

    シート側は**性質で禁じる**形に書き直し
    (「五感が受けた被害はすべて禁止」「心理の動揺だけ」)、
    さらに**終幕テストの `Forbid` に加えて機械的に検出する**ようにした:

    | 検出語 | 理由 |
    |---|---|
    | 耳鳴り / 煙が | ナビは現場にいない。身体の被害・現場の様子は語れない |
    | よってからに / しくさっ | **プレイヤーを責める語法** (ADR N-25) |

    後者は実測で「まっすぐ**切りよってからに**」が出たため。
    **非難の語法は方言に紛れて入り込む**ので、語形で拾う。
    他4キャラでも回帰なしを確認した。

91. **209 の現在位置を抽選するのをやめた** (実運用の事故。ADR C-15・N-50):

    実プレイで**ロータリーが4にあるのに、ナビが「2番にありませんか」**と言い、
    プレイヤーが正しく資料を読んだのに別の行を引いて**爆発した**。

    ```
    12:34:46 P> 全部点灯しているんですけど緑だけ点滅ですね
    12:34:47 N> 緑だけ点滅やな、了解。ロータリーが2番にありませんか。
    12:35:06 P> ロータリーは4番にありますね
    12:35:07 N> 4番やない、そこは違うで。もういっぺん資料4を確かめてみ。
    12:35:19 ✗✗ 爆発 (禁止位置でダイヤルを停止)
    ```

    #### 原因: 抽選した位置と実位置がずれる

    `position` を抽選していたが、**実機のツマミをそこへ動かす手段が無い**。
    ロータリーは前のプレイから物理的に位置が残る。**一致するのは偶然だけ**。

    ずれると3つ同時に壊れた:

    | | 起きたこと |
    |---|---|
    | 表示 | 実位置はダミー表示 → **対照表と照合できない** |
    | ナビ | 抽選値を事実として喋る → 「2番にありませんか」 |
    | 資料 | プレイヤーが**間違った行**を引く → 危険位置を踏む |

    **プレイヤーは正しく読んでも助からない**状態だった。

    #### 直し方: サーバーは位置を知らないまま渡す

    **6行すべてを Core へ渡し、Core がステージ開始時点の実位置で
    行を確定する**。`ResetStageProgress()` は既にステージ開始の3経路すべてから
    呼ばれているので、そこへ `ApplyPanelRows()` を足すだけで済んだ。

    - `precondition.rotary` (解除位置)・`forbidden_rotary` (危険位置) を
      **TOML から消し**、Core が実行時に設定する
    - 解除位置の表示 (cut だけ点滅)・危険位置の表示 (赤だけ点灯) も Core が作る
    - **ADR A-2 は守れる** — 全行が JSON に入るので、Wi-Fi 切断中でも完結する
    - **ADR D-3 も守れる** — 表は `scenario_panel.go` のまま。Core は
      送られた行を使うだけで表を持たない

    「開始位置がたまたま危険位置」は `rotary_touched_since_reset_` が
    既に守っていた (一度も動かしていないうちは違反にしない)。

    #### 対照表から点滅を外した

    当初案では **cut に使える色が無くなった**。cut と点滅色が衝突すると
    (開始位置で cut が点滅していると) 回す前に答えが見えるため、
    従来は「cut と重なる行を避けて抽選」していた。**位置を選べなくなると
    この回避が効かない**。旧表は点滅色に5色すべてを使っていたので候補ゼロ。

    ユーザーの要望は「**cut は全色使いたい**」。そこで
    **見え方から点滅を外し、点灯色の組合せだけで一意にした**。

    | | 旧 | 新 |
    |---|---|---|
    | 見え方 | 点灯1色 + **点滅1色** | **点灯2〜3色のみ** |
    | 組合せ数 | 20通り | 20通り (2〜3色の組) |
    | 点滅の意味 | 位置の手がかり **兼** 切る線 | **「切れ」の合図だけ** |
    | cut に使える色 | **0色** | **5色すべて** |

    **点滅が出るのは解除位置だけ**になるので、どの色が cut でも衝突しない。
    副次的に**ルールが単純になった** — 「点滅している = 切る線」で一意。

    新しい表 (資料4 を刷り直す):

    | 点灯 | 位置 | 危険 | 解除 |
    |---|:--:|:--:|:--:|
    | 黄+白 | 0 | 1 | 3 |
    | 赤+白 | 1 | 4 | 5 |
    | 赤+黄+緑 | 2 | 3 | 4 |
    | 赤+緑+青 | 3 | 1 | 0 |
    | 緑+青 | 4 | 2 | 1 |
    | 黄+青+白 | 5 | 3 | 2 |

    **全6行が単独で成立する**ことを機械検証した (`TestPanelWorksFromAnyStartPosition`)
    — どこから始めても解除位置へ到達でき、危険位置が経路の内側にあり、
    開始位置の表示で cut が点滅しない。

    質の面では **色の登場回数が全色3回で均等**(偏らせると位置を連想できる)、
    **解除位置が0〜5すべて**、点灯色数は2色と3色が3行ずつ。

    #### ナビゲーターは位置を当てなくなった

    位置を知らない立場になったので、**「ロータリーが◯番にありませんか」を廃止**した。
    資料へ誘導し、**プレイヤーが読んだ数字をそのまま受ける**。

    ```
    旧  N> ロータリーが2番にありませんか      ← 知っている前提 (事故の元)
    新  N> 手元の資料4を開いて、今光っている色の行を見るんや
    ```

    あわせて **「それは違う」と断定することを明示的に禁じた** (ADR N-50)。
    装置を見ていないナビは報告の正誤を判定できない。事故ログの
    「4番やない、そこは違うで」がこれに当たる。

    #### 検査の穴も塞いだ

    `TestScriptsReportLampsFirst` の判定語に **「点いて」が無かった**。
    209 は点灯色だけを報告する設計になったので、
    「赤と黄色が点いています」が正規の第一報。「点灯」しか見ていないと
    取りこぼす。

92. **209 を全6開始位置で回して、点灯と点滅の取り違えを見つけた** (決定91 の追検証):

    決定91 で「開始位置を問わない」設計にしたので、**0-5 のどこから
    始めても成立するか**を実際に回して確かめた。
    シミュレーターに `-sim-panel-start` を足し、台本を開始位置で
    展開できるようにした (点灯色・危険位置・解除位置を変数化)。

    ```bash
    go test -run TestSimulateAllStages -simulate -sim-stages 209 -sim-panel-start 3 -v
    ```

    #### 位置0と4で誤動作した

    **cut が赤のとき**、解除位置で赤が点滅しているのに
    **危険位置と誤認して切らせなかった**:

    ```
    P> 3まで回しました。今度は赤が点滅しています。
    N> 赤はあかん、そこは危険位置や。はよダイヤル回し直してくれ。  ← 誤り
    ```

    #### 原因は私が書いた指針の曖昧さ

    `procedure` にこう書いていた:

    > **赤だけが点いている**という報告が来たら、それは**危険位置に
    > 止まっている**合図

    生成AIが**「点いている」を落として「赤」だけで反応した**。
    点灯と点滅は**意味が正反対**なのに、区別が1語しかなかった。

    | 表示 | 意味 |
    |---|---|
    | 赤が**点灯** (単独) | 危険位置に止まっている → すぐ動かす |
    | 赤が**点滅** | **切る線** → 切らせる |

    **cut が赤の回でだけ起きる**ため、旧設計 (cut が赤にならない) では
    表面化しなかった。cut を5色へ開放したことで踏んだ形。

    #### 直し方

    指針を**対比の形**に書き換えた:

    - **点滅している色 = 切る線**
    - **赤だけが点灯している (点滅ではない) = 危険位置**
    - **「点滅」と報告されたものを危険位置と誤認してはいけない**

    修正後、**全6位置で所見ゼロ**。cut が赤 (危険位置の合図と同色) という
    最悪ケースでも正しく切らせた。

    #### 一般化

    **意味が正反対の2つを、1語の違いで書き分けない。**
    「赤だけが点いている」のように**修飾語1つで区別する書き方**は、
    生成AIが修飾語を落とすと逆の意味になる。
    **対比の形で並べて書く** (「Aなら○○、Bなら××」)。

    これは決定86 (条件と動作を別々に書くと動作が落ちる) と同じ構図で、
    **落ちても文が成立してしまう書き方が危ない**。

    #### cut の分布も確認した

    `TestPanelCutColorDistribution` を追加。200回の抽選で
    **5色すべてが出る**ことを担保する (赤46/黄46/緑43/青32/白33)。
    偏りが出たら「点滅を見え方から外した」前提が崩れている。

93. **ステージ定義の例文が、全キャラの口調を壊していた** (ADR N-52):

    5キャラ × 全18ステージの横断シミュレーション (2026-08-29) で、
    **302 の差し戻しが5人とも同じ文で始まっていた**ことに気づいた。

    | キャラ | 出た発話 |
    |---|---|
    | フクロウ | 「本当にデルタか? 念のためもういっぺん資料1で確かめてみ」 |
    | アオサギ | 「デルタですね。**本当にそれか?** 念のためもういっぺん…確かめてみてください」 |
    | ツグミ | 「デルタだね。**本当にそれか?** 念のためもういっぺん…確かめてみるといい」 |
    | ヒバリ | 「デルタですね、**本当にそれか?** 念のためもういっぺん…」 |
    | モズ | 「**本当にデルタか?** 念のためもういっぺん資料1で確かめてみ」 |

    出所は `302_angou_denbun_jamming.toml` の `procedure` に書いた
    **例文1つ**だった。語尾だけ各キャラに寄せ、**骨格は丸写し**。

    #### 例文はモズの口調で書かれていた

    「確かめて**み**」は大阪弁。決定80 は `[triggers]` の例文を消したが、
    **ステージ定義も全キャラ共通**であることを見落としていた。

    303 追いかけダイヤルではもっと露骨に出た —
    `procedure` の例文「十の位とダイヤルが同じ数字に**なっとる**、その瞬間に切る」を
    **フクロウがそのまま使い**、「同じ数字に**なっとる**、その瞬間に切れ」と
    **「〜だ/〜しろ」の中に関西弁が挟まった**。日本語として破綻している。

    #### 直し方は決定80 と同じ

    ステージ側からは例文を削り、「**言い回しはキャラシートに委ねる**」と書く。
    203・205 は元々この形で、**302・303 だけが例外だった**。

    再実行 (3回ずつ) で 303 の方言混入は消え、関西弁はモズだけになった。

94. **委ね先の例文を「台詞」で置いたら、今度はそれが固定された** (ADR N-45b):

    決定93 の委ね先として、5人のシートに **差し戻しの台詞例**を1文ずつ置いた。
    結果、**15回中13回が例文の丸写し**。1つの固定文が5つの固定文になっただけだった。

    さらに**モズが「デルタやないな」と断定した** (3回中1回)。
    302 は「装置を見ていないので断定できる立場にない」(ADR N-50) が要件なので、
    これは**課題として成立しない**。

    #### 台詞ではなく指針にした

    決定80 の「解除成功」と同じ形 —
    **「毎回あなた自身の言葉で書く。決まり文句を持たない」**と書き、
    **何を言うか**だけを箇条書きにした。

    #### 「〜やない」と書いたら「〜やない」が出た

    断定を防ぐつもりで **「『〜やない』と断定しない」**とシートに書いたところ、
    **3回中3回が「デルタやない」で始まった**。N-32 (禁止は性質で書く) の再現で、
    **禁止語を引用すると、それ自体が手本になる**。

    立場で書き直した:

    > あなたは装置を見ていない。プレイヤーの読み取りが合っているかを
    > **知り得る立場にない**。だから**否定の形では言えない** — 言えるのは
    > 「引っかかる」という**自分の側の感覚**と、
    > **もう一遍あたれ**という段取りの指示だけ。

    **「言うな」ではなく「言えない」**と書き、**代わりに何が言えるか**を並べる。
    N-6 (断り方は知らない側で書く) と同じ構図。

    #### 「言えないこと」だけ書いたら、差し戻しそのものが消えた

    立場で書き直したところ、今度は**モズが誤答をそのまま通した**
    (3回中1回。「デルタやな、ほな資料1で頭文字引いてみ」)。
    否定を避けさせた結果、**引き止める力まで抜けた**。

    **やることを先頭に置いて直した** — 「**必ず引き止める。**
    ここで先へ進めると、誤ったまま線を切って**即爆発する**」。
    制約 (どう言えないか) の前に、**目的 (何をする場面か)** を書く。
    15回中15回で引き止めるようになった。

    #### 残っているばらつき

    モズの断定 (「デルタやないな」) は **3回中3回 → 0回 → 1回**と動く。
    **消え切っていない**。「入りは自分の側から」という指針を足して
    5回試したところ**逆に2回へ増え**、さらに理由付け
    (「違う綴りが混もっとるで」= ADR N-45 違反) まで出たため**取り消した**。

    禁止を重ねると安全な一文へ収束する (N-20) 側の失敗で、
    **キャラシートを触るたびに 302 を回し直す**必要がある。
    実機投入前に再確認する。

95. **無応答時の声掛けを実装した** (ADR P-9):

    `prompt.toml` に `silence` トリガーの指示は最初から書いてあったが、
    **それを鳴らす実装がどこにも無かった** (grep で呼び出しゼロ)。
    交信はプレイヤーから話しかける前提なので、手が止まって黙り込むと
    **サーバーに何も届かないまま時間だけが減る**。

    `navigator_silence.go` (`SilenceWatcher`) を追加した。

    #### 固定間隔にしない

    待ち時間は `silence_min_ms`〜`silence_max_ms` の幅から**毎回引き直す**
    (既定40〜60秒)。固定にすると「一定時間黙れば必ず鳴る」と読まれ、
    **装置ではなく無線の挙動を試す遊び**になる。

    #### 塞がっている間は掛けない

    特小無線は半二重。混線やナビ自身の発話に重ねると
    **プレイヤーの送信を潰す**ので、混線と同じ `BusyFor` を見て見送る。

    #### リセットはプレイヤーの発話でだけ

    ナビ自身の発話で計測をやり直すと、プレイヤーが黙ったままでも
    計測が延び続け、**二度と声を掛けられなくなる**。
    `Notice` を呼ぶのは `audio_pipeline.go` のプレイヤー発話経路だけにした。

    終了済み (爆発・解除) のセッションでも掛けない —
    締めの最終メッセージのあとに「どうした?」と続くと台無しになる。

96. **303 は例文が「口調」ではなく「意味」を運んでいた** (決定93 の直しすぎ):

    決定93 で 303 の例文を削ったところ、**指示そのものが壊れた**。
    フクロウが3回中2回、**プレイヤーを叱った**:

    > 「**馬鹿野郎**、合わせてから切るなと言ったろ。十の位が一致したその瞬間を狙え」
    > 「**馬鹿野郎**、十の位が下がってから合わせろ。数字が変わるたびに追いかけて回せ」

    後者は**手順として逆**で、「切る」が消えている。
    他の4キャラは3回中3回とも正しく、**フクロウだけが壊れた**。

    #### 原因は「AではなくB」の書き方

    残っていた指示は
    **「合わせてから切る」ではなく「合っている状態で切る」**という形だった。
    A と B が**近すぎて取り違える**うえ、
    「合わせてから」を禁じられたナビは、
    プレイヤーの『5に合わせました』という**正しい報告を誤りと受け取った**。

    例文はここで**意味の橋渡し**をしていた。口調だけを運んでいたわけではない。
    決定93 で消したとき、**橋も一緒に落ちていた**。

    #### 直し方: 手順を順番に並べ、「合わせるのは正しい」と明記する

    1. ダイヤルを十の位と同じ数字に合わせる
    2. 一致している間に線を切る
    3. ずれたら回し直してまた一致させる

    そのうえで**「『合わせる』は正しい手順であって間違いではない」**
    **「叱ってはいけない」**と書いた。`hint_l3` にも同じ罠
    (「『合わせてから切れ』とは言わない」) があったため揃えて直した
    (procedure だけ直すと L2・L3 で再発する。ADR N-48)。

    これは決定92 (意味が正反対の2つを1語の違いで書き分けない) と同じ構図。
    **例文を消すときは、その例文が意味を運んでいないか確かめる。**

97. **ステージ定義に残っていた大阪弁を全て洗い出した**:

    決定93 では 302・303 の**例文**だけを直しており、
    302 の**違反例リスト**を見落としていた。全キャラ共通のファイルに
    大阪弁が4箇所残っていた:

    - 「デルタ**やない**、エコー**や**」(正解を教える例)
    - 「デルタ**やない**」(断定して突き放す例)
    - 「3文字目が短点のはず**や**」(理由を述べる例)
    - **「せやな」と受けて**、頭文字を引かせる ← **指示文そのもの**

    最後の1つは禁止例ですらなく、**全キャラに「せやな」と言わせる指示**だった。

    違反例は**引用すると手本になる** (ADR N-32)。モズの断定が
    決定94 で消え切らなかったのは、**ステージ側が「デルタやない」を
    2回も見せていた**ためと考えられる。**性質で書き直した**
    (「違うと断定して突き放す」「どこがどう違うか理由を述べる」)。

    #### 洗い出しの方法

    `scenarios/stages/*.toml` と `navigator/prompt.toml` に対し、
    大阪弁の語尾・語彙を正規表現で全文検索した:

    ```
    grep -nE "しとる|やねん|やで|やろ|ほな|あかん|せや|してみ|どない|もっぺん|「わし|わしが|わしは" \
      scenarios/stages/*.toml navigator/prompt.toml
    ```

    結果、**モズのシート以外に大阪弁は残っていない**ことを確認した。
    キャラシートを直したら、**共通ファイル側も同じ検索を掛ける**。

    #### 違反例を消したら、禁止も一緒に消えた

    違反例リストを性質へ書き直したところ、**断定が増えた**
    (フクロウ1/3・モズ3/3 が「デルタだな、**違う**」「デルタ**やない**な」)。
    リストは**悪い手本**であると同時に**禁止**でもあり、
    手本を消すときに禁止まで弱めていた。

    #### 効いたのは「言い出しの形」を順番で指定すること

    禁止 (「断定するな」) は、どう書いても効きが安定しなかった。
    **順番で書いたら止まった**:

    > 1. **プレイヤーの報告を受け止める**(復唱でよい)
    > 2. **自分が確信を持てないことを言う**(引っかかる・確証が持てない)
    > 3. **${sheet_morse}で確かめ直すよう頼む**
    >
    > **1 を『違う』『それではない』の類で始めない。**

    15回中15回で 1 から始まるようになり、**否定で始めた回は0**。
    303 (決定96) と同じで、**禁止より順番のほうが守られる**。

    残る「なんだかちょっと違う気がする」(ヒバリ) は、
    **自分の印象として述べる形**なので許容範囲。断定ではない。

98. **303 の「追いかけ」が落ちていた — 課題の本体が消えていた**:

    決定96 で叱責は止まったが、**「十の位が減るのでダイヤルを回し直して追いかける」
    という指示が落ちていた** (15回中4回で一度も言及なし)。

    これは言い漏らしではなく、**課題そのものの消失**。
    追いかけを聞いていないプレイヤーは、ダイヤルを5に合わせたまま待ち続け、
    **十の位が4に変わったことに気づけない**。
    「追いかけダイヤル」という名前どおり、**追いかけが課題の本体**。

    #### 決定96 の直し方が原因

    手順を 1・2・3 で並べたとき、追いかけを **3 (末尾)** に置いた。
    **長い指針は末尾から落ちる** (ADR N-51) — 204 で既に分かっていた
    失敗を、そのまま繰り返していた。

    | | 追いかけの言及ゼロ |
    |---|---|
    | 初回 (修正前) | 2/15 |
    | 決定93 の直後 | 2/15 |
    | **決定96 の直後** | **4/15** (悪化) |
    | must_say 追加後 | **0/15** |

    #### 直し方

    - **`must_say` へ独立させた** (ADR N-51)。204 と同じ扱い
    - **手順の 1 に繰り上げ**、「合わせる」と「追いかける」を
      **ひとつの動作**として言わせた (ADR N-48)。切り離すと
      「合わせる」だけが伝わる
    - `hint_l3` の順番も揃えた (procedure だけ直すと L3 で再発する)

    #### 強めたら、今度は「切る」が落ちた

    追いかけを強調した結果、**ツグミが最終指示で「切る」を落とした**
    (「十の位が変わったら、また回し直して追いかけるといいよ」で終わり)。
    追いかけ続けるだけでは線が切れず、時間が尽きる。

    **「追いかけて、一致した瞬間に切る」を必ず組で言う**と明記した
    (ADR N-48 の「操作は動作でつなげる」)。
    **片方を強めると、もう片方が落ちる** — 対になる操作は
    **常に組で書く**。

    #### 検査を追加した

    シミュレーション台本の 303 に **`MustMention`** が無く、
    **3回の修正を通して所見ゼロのまま見逃していた**。
    `"回し直|追いかけ|追って|ずれたら|変わったら"` を追加した。
    **落ちると詰む情報には、必ず `MustMention` を置く。**

99. **303 に「一致した瞬間に切れ」と言わせていたのは誤りだった** (ADR N-54):

    決定96・98 を通して「一致したその瞬間に切る」という言い方を使っていたが、
    **これが間違いだった**。

    ファーム (`timer_digit_rule.h`) を確認すると、303 の
    `precondition` は `digit = "tens", match = "rotary"`。
    **十の位は10秒間そのまま**で、さらに変わった直後**1秒の猶予**がある
    (`kGraceMs`)。つまり**ダイヤルを合わせたら、その10秒の間はいつ切ってもよい**。

    | ステージ | 桁 | 窓 | 正しい言い方 |
    |---|---|---|---|
    | 208 | 一の位 | 1秒 | 「${digit}になった瞬間に切る」 |
    | 304 | 一の位 | 1秒 | 「${digit}になった瞬間に切る」 |
    | **303** | **十の位** | **10秒** | 「**合わせて、合っている間に切る**」 |

    #### 言い方が設計意図を打ち消していた

    ADR S-7 は「読む→計算する→回す→切る」が終わる長さを確保するために
    **十の位を選んだ**。そこへ「瞬間を狙え」と言わせると、
    **確保したはずの余裕を言葉で取り上げる**ことになる。
    セーフティーグラス着用・立ったまま・無線で急かされている状態で、
    **落ち着いて切れば済むところを焦らせていた**。

    303 の難しさは**十の位が変わるたびに合わせ直す**ことであって、
    **反射神経ではない**。「追いかけダイヤル」という名前どおり。

    #### 直したもの

    `briefing` / `answer` / `procedure` / `hint_l2` / `hint_l3` から
    「瞬間」を外し、**「合わせて、合っている間に切る」**に統一。
    あわせて**「瞬間・一瞬・タイミングを狙うとは言わない」**と明記した
    (窓が10秒あることも書いた)。

    台本に `MustNotMention: ["瞬間", "一瞬"]` を追加。実行15回で**0件**。

    **208・304 は「瞬間」のままでよい** — 窓が1秒しかなく、
    あちらは本当にタイミングの課題。**窓の長さを変えたら言い方も見直す。**

    #### 正確に書いたら、今度は長くなって末尾が落ちた

    `must_say` に「合わせて切る」+「変わったら合わせ直す」の2文を置いたところ、
    **後半が15回中7回で落ちた** (N-51 の再現)。

    1文に畳んでも改善しなかったため、**`must_say` から
    「合わせて切る」を外し、「変わる・合わせ直す」だけを残した**。
    合わせて切ることは**装置を見れば分かる**が、
    **数字が変わり続けることは、ナビが言わないと気づけない**。
    `must_say` に置くのは**後者だけ**でよい。

    入り口での言及は **9/15 → 10/15**。会話全体では **15/15** で伝わっており、
    残りは L2 で補われている。**入り口に必ず入れるところまでは詰め切れていない**
    (実機で様子を見る)。

100. **シミュレーション台本のプレイヤーが、謎を自分で解いていた**:

    303 の欠落を何度も見逃していた原因は、**台本のプレイヤーが優秀すぎた**こと。

    | 台本の発話 | 問題 |
    |---|---|
    | 「タイマーの数字とダイヤルですか」 | **仕掛けを言い当てている**。303 はこの関係に気づくことが謎 |
    | 「十の位が今8です。**ダイヤルは5までしかありません**」 | 6-9 で切れない理由を**自力で導いている** |
    | 「5になったので合わせました」 | **待つ判断まで自力**。ナビの助言が要らない |

    このプレイヤーは**ナビゲーターが何も説明しなくても正解へ進む**。
    だから「合わせ直し」が落ちても台本は破綻せず、**欠落が表面化しなかった**。

    #### 208・304 は正しく書けていた

    | ステージ | 台本のプレイヤー |
    |---|---|
    | 208 | 「タイマーの**どの桁を見ますか**」「**いくつになったら**切りますか」 |
    | 304 | 「押さえたままです。**いつ切りますか**」 |

    **報告と質問だけ**にして、**説明はナビに委ねている**。
    303 をこの形に揃えた:

    - 「ダイヤルはどこに合わせますか」
    - 「十の位は今8です。ダイヤルが合いません」(事実の報告だけ。理由は言わない)
    - 「5に合わせました。次はどうしますか」

    #### 他のステージも洗った

    - **206 綱渡り**: 「**分かりました**。どこまで回せばいいですか」
      → 「どこまで回せばいいですか」。危険位置は**ナビが言わないと即爆発する**
      (ADR N-44)。「分かりました」で受けると**警告を落としても成立してしまう**
    - **104**: 「速いほうと遅いほうが**分かりました**」→「見比べています」。
      速さの比較そのものが課題

    **209 はそのままでよい** — 危険位置を**資料から読む**のが謎なので
    (N-44)、プレイヤーが読み上げるのが正しい。

    #### 一般化

    **台本のプレイヤーは、ナビの助けが要る状態に置く。**
    プレイヤーが仕掛けを言い当てたり理由を自力で導いたりすると、
    **ナビが説明を落としても台本が通ってしまい、検査にならない**。
    書いてよいのは**装置を見れば分かる事実の報告**と**質問**まで。

    #### 直した効果

    台本を変えたことで、ナビが**説明せざるを得なくなった**。
    「ダイヤルが合いません」という報告に対し、
    以前は理由をプレイヤーが言っていたが、いまはナビが
    「0から5の間に入るまで待て」と答えている。

    「瞬間」は **15/15 → 1/15** (モズ1回)。
    `MustNotMention` が検出するので、残りは可視化されている。

    入り口での「合わせ直し」への言及は 8/15 で、
    **まだ詰め切れていない**。ただし会話全体では 14/15 で伝わっている。

101. **ナビが「診断」しようとして、手順を小出しにしていた** (303 の本丸):

    ここまでの修正はすべて**言い方**の話だったが、より根本的な誤りがあった。
    **ナビは正解を全部知っているので、プレイヤーに確認することは何も無い。**
    ランプの色さえ分かれば、あとは**手順を最後まで渡すだけ**でよい。

    ところが実際の交信はこうなっていた:

    ```
    N> タイマーの秒の十の位とダイヤルの位置を見てくれ。
    P> ダイヤルはどこに合わせますか。
    N> ダイヤルはタイマーの秒の十の位に合わせろ。
    P> 十の位は今8です。ダイヤルが合いません。
    N> 0から5の間に入るまで待て。
    ```

    **ナビが情報を小出しにし、プレイヤーが聞き返す**やり取りになっている。
    無線は半二重で1往復に時間がかかるうえ、タイマーは減り続ける。
    **聞き返しの往復そのものが損失**で、しかもナビ側に聞く理由が無い。

    #### 原因は2箇所

    1. **`hint_l1` が「関係があることを伝える」で終わっていた。**
       これは**ヒントの指示**であって手順の指示ではない。
       ナビは断片を渡して待つ

    2. **`prompt.toml` の「1回の発話で伝えるのは次にやること1つ」。**
       これを**動作1つ**と解釈すると「まずダイヤルを合わせろ」で止まる

    #### 直し方

    `hint_l1` に**「報告を受けたら手順を最後まで伝える」**と明記し、
    **確認は要らない**ことも書いた
    (「タイマーの数字もダイヤルの位置もプレイヤーに尋ねる必要はない」)。

    `prompt.toml` 側にも**「やること1つ」は途中で止めてよいという意味ではない**
    という補足を入れてみたが、**これは取り消した**。
    全キャラ共通の出力ルールが長くなったぶん、
    **第一声で3要素が揃う率が 13/15 → 9/15 へ落ちた** (N-51 の再現)。
    落ちたのは決まって「変わったら合わせ直す」で、
    **共通ファイルに書き足すと、ステージ側の指針が押し出される**。

    **ステージ固有の要求は、ステージ側だけで書く。**

    #### 結果

    第一声で**3要素(合わせる・変わったら合わせ直す・切る)が揃った**のは
    **13/15**。聞き返しの往復が消えた:

    > 「点滅しとるな、了解や。十の位は10秒ごとに変わるさかい、
    > ダイヤルをそれに合わせつつ、合っとる間に点滅しとる色の線を切れよ」

    #### 202 は元から正しかった

    `hint_l1` に**「(気づかせるだけで止めない)」**と書いてある。
    **303 だけがこの一文を欠いていた。**

102. **台本に「切りました」を置いたら、ナビが失敗をでっち上げた**:

    決定101 で 303 の台本を書き直した際、最後に
    **「切りました。どうぞ」** という `player_message` を置いた。
    これが**実機と食い違っていた** — 切断の成否は
    **`stage_cleared` (デバイスイベント) で届く**のであって、
    プレイヤーの音声報告で判定するものではない。

    成否が分からないまま反応させた結果:

    | キャラ | 発話 | 問題 |
    |---|---|---|
    | アオサギ | 「切りましたね。**誤動作です。記録しました。**手順のどこで外れたか確認してください」 | **起きていない失敗をでっち上げ**、ありもしない記録まで作った |
    | ヒバリ | 「**わわっ、今のは危なかったです!**」 | 同上。装置を見ていないので危なかったかどうか分からない (ADR N-26) |
    | ツグミ | 「切ったんだね。まだタイマーは動いてるから、十の位に合わせて**また切る**といいよ」 | **2本目を切らせようとした**。切った線は戻せず、誤切断は**即爆発** (ADR S-2b) |

    ツグミの1件は**プレイヤーを殺す誘導**で、最も重い。

    #### 原因は台本のほう

    「切りました」に対する扱いは**どのステージにも書かれていない**。
    書かれていないのが正しく、**実機ではその報告が来る経路が無い**。
    プロンプトに但し書きを足すのではなく、**台本から外した**。

    **台本は実機の経路に合わせる。** ありえない入力を与えると、
    ナビは**その場で辻褄を合わせようとして嘘をつく**。

103. **落ちる項目は「真ん中」にある** (303 の並び順):

    第一声の3要素のうち、落ちるのは**必ず2番目の
    「十の位は10秒ごとに変わる」**だった (15回中5回、全て同じ項目)。
    1番目 (合わせる) と3番目 (切る) は落ちない。

    さらにログを見ると、**落ちた回も次の発話では言っている**。
    消えているのではなく**遅れている**。だがその時点では
    プレイヤーは既にダイヤルを合わせて待っており、
    **合わせ直しが要ることを知らないまま10秒を過ごす**。

    #### 並べ替えは効かなかった

    成功した回はいずれも「十の位は10秒ごとに変わる」から入っていたため、
    **その順に並べ替えてみた** (変わる → 合わせる/合わせ直す → 切る)。

    **効果が無く、副作用だけがあった:**

    | | 3要素の充足 | 「切る」の欠落 |
    |---|---|---|
    | 元の順 (合わせる→合わせ直す→切る) | 10/15 | 0 |
    | 並べ替え (変わる→合わせ直す→切る) | 10/15 | **4/15** |
    | 並べ替え + 「必ず切るで終える」 | 10/15 | **3/15** |

    **末尾に置いた項目が落ちる**のは変わらず、順番を入れ替えると
    **落ちる項目が入れ替わるだけ**だった。しかも「切る」が落ちると、
    プレイヤーは合わせ続けるだけで線を切らず**時間切れになる**ため、
    合わせ直しが落ちるより重い。**元の順に戻した。**

    N-51 (末尾が落ちる) は**並べ替えでは解決しない**。
    落ちて困る項目は `must_say` に出すしかない。

104. **色合わせの完了で発話していた — N-26 と矛盾していた** (ADR N-56):

    204 で押し切った直後に**オペレーターから連絡が入っていた**。
    実運用でユーザーから「これはやめて欲しい」と指摘があった (2026-09-01)。

    `game_events.go` の `msgColorMatchCompleted` が `speakAsync` を
    呼んでいた。**決定48 (ADR N-26) と正面から矛盾している** —
    押下の途中 (`push_progress`) では「手元が見えていることになる」として
    黙ると決めているのに、**最後の1押しでだけ喋っていた**。

    「色合わせが完了した」は**ボタンを押し切ったという装置の中の出来事**で、
    装置を見ていないナビゲーターには知りようがない。
    完了を知っている時点で前提が崩れている。

    #### 実害もある

    204 は**正解がプレイヤーの記憶にしかない** (ADR N-36)。
    押し切った直後は「最後に押した色」を反芻している最中で、
    そこへ無線が入ると**記憶を上書きする**。

    同じ事故は L4 の直言で一度起きている (2026-08-23)。
    「最後に押した色を忘れた」と言われた26秒後に L4 をまたぎ、
    正しく記憶していた色をナビが上書きして**即爆発**した。
    タイミングは違うが、**割り込みが記憶を壊す**という構造は同じ。

    #### やめても手詰まりにならない

    押し切ると**ランプが全部消える**ので、プレイヤーは終わったと分かる。
    そこから「押し終わりました」と報告が来るので、
    `player_message` で応じれば足りる。**むしろ N-10 (まず報告させる) の
    形に戻る**。

    #### 洗い出した結果 — 他に発話しているものは無い

    `speakAsync` / `speakAsyncThen` の呼び出しは5箇所しかない:

    | イベント | 発話 | 種別 |
    |---|---|---|
    | `stage_cleared` | する (最終ステージを除く) | 線を切って結着 |
    | `wrong_action` | する (`detail=color_match` を除く) | 線を切って結着 |
    | `color_match_completed` | **やめた** | ボタン操作 |
    | `push_progress` | しない (決定48) | ボタン操作 |
    | `exploded` / `defused` | する | 終幕 |

    **ボタン・ダイヤルの操作そのものに反応するものは、これでゼロになった。**
    `wrong_action` の `detail=color_match` (色合わせの押し間違い) は
    決定48 で既に除外済み。`push_progress` (201・103 の復唱・押下順) も同様。
    ロータリー (206・209・301・303) は**そもそも進行イベントを送っていない**
    (`device_status` の再同期に載るだけで、`HandleDeviceMessage` は
    `msgDeviceStatus` で即 return する)。

    `prompt.toml` の `color_match_completed` 定義は**残した** —
    `push_progress` と同じく、将来使う場合に fallback の汎用文へ
    落ちないようにするため。コメントで「現在は使っていない」と明記した。

    台本の 204 も `color_match_completed` のターンを外し、
    **「押し終わりました。ランプが全部消えました」というプレイヤーの報告**に
    置き換えた。押し切ったあとの交信が**プレイヤー起点で始まる**ことを
    台本の側でも表すため。

105. **「十の位」がどこの十の位か分からなかった** (303。ADR N-57):

    実運用で 303 のナビがこう言っていた (2026-09-01):

    ```
    N> 今度はダイヤルを十の位に合わせ直して、合っている間に赤い線を
       切ってください
    ```

    **「十の位」が何の十の位か分からない。**

    装置には数字が**2箇所**ある — **カウントダウン表示**と
    **ロータリーの目盛り (0-5)**。「十の位」とだけ言われたプレイヤーは、
    いま手を掛けている**ダイヤルの数字のほう**を見る。
    追いかける対象を取り違えると、合わせたつもりで**ずっとずれたまま**になり、
    十の位が変わっても気づけない。

    #### 落ちていたのは「繰り返し」のほう

    `briefing` は「残り時間の秒の十の位」、`answer` は「タイマーの秒の十の位」と
    **元から書いてあった**。第一声では言えている。
    縮んでいたのは**2回目以降** — 一度言うと、あとは「十の位」で済ませる。

    N-48 (操作は動作でつなげる) と同じ構図で、
    **省略されると意味を失う語は「毎回言う」と明示しないと縮む**。
    「一度言えば伝わる」は成り立たない。

    #### 直し方

    `must_say` / `procedure` / `hint_l1` 〜 `hint_l3` の**すべてに**
    「**カウントダウンの秒の十の位**と言い切る。**2回目以降も省略しない**」を
    書いた。あわせて**省略すると何と取り違えるか (ダイヤルの数字)** まで
    書いてある — 理由が無いと、字数の都合で真っ先に縮む (N-22)。

    台本の `MustMention` に
    `カウントダウン|タイマー|残り時間|残時間` を足した。
    「点滅している」を必須にしたとき (決定99) と同じで、
    **省略できる語は検査で押さえる**。

    208・304 は**一の位**だが、押さえるボタンにも線にも数字が無いため
    同じ取り違えは起きない。`briefing` は同じく
    「カウントダウン表示の秒の一の位」と書いてある。

106. **MustMention の窓が、手順の渡る前に閉じていた** (303。決定105 の副産物):

    決定105 で 303 の台本に `MustMention` を足したところ、
    **正しく伝えている回まで所見になった**。

    原因は検査の窓のほうだった。`MustMention` は
    「`session_start` + **最初の** `player_message`」の2発話にしか
    要求しない (`entryTurns < 2`)。ところが 303 の台本は、
    決定101 (ADR N-55) で**報告を2往復に分けてある**:

    | | プレイヤー | ナビ |
    |---|---|---|
    | 1回目 | 「点滅しています」(色名なし) | **色を尋ね返す**のが正しい |
    | 2回目 | 「点滅しているのは赤です」 | **ここで手順を渡す** |

    **手順が渡るのは2回目の返し**なのに、窓は1回目で閉じていた。
    「色名が無ければ手順を渡すな」と決めた N-55 と、
    「入り口は2発話」という既定が**噛み合っていなかった**。

    #### 台本ごとに広げられるようにした

    `simScript.EntryTurns` を足し、303 は `3` を指定した
    (未指定なら従来どおり2)。ステージ側ではなく**台本側の指定**にしたのは、
    窓の広さが「ナビが何往復で手順を渡すべきか」という
    **台本の組み方**に紐づくため。

    広げた結果、決定105 で足した「カウントダウン」の検査は
    **5回連続で通った** — 直したかったものは直っている。
    同時に、既存の「合わせ直し」「点滅している」が
    **5回中3回・4回で落ちている**ことが見えるようになった。
    これは N-51 (末尾が落ちる) の再発で、窓が狭かった間は
    **検査に掛かる前に窓が閉じて隠れていた**。決定105 とは別の問題として残す。

107. **「節目のみ名乗る」で、ほぼ初回しか名乗らなくなった** (ADR N-21):

    出力ルールに「コールサイン(名前)は開始時と重要な節目のみ。
    会話が続いている間は省略」と書いていた。**「節目」の判断は生成AIに委ねられ、
    結果としてほぼ初回しか名乗らなかった。**

    元の想定 (決定5) は「緊急時に簡潔化するのは無線運用の作法であり、
    **省略自体が演出になる**」というもので、**平時は名乗る**前提だった。
    平時から省略していては、緊迫時に落ちるものが無くなる。

    #### 平時は毎回名乗る

    「基本的に毎回入れる」「会話が続いているからといって省略しない」と書き、
    **省略する例外を2つに限定**した — 緊迫時と、名乗らないキャラクター。

    #### 名乗りを字数から外した

    毎回名乗らせると、**名乗ったぶんだけ本文が削られる**。危険の警告や
    押す順番が先に落ちるのは決定24・31・34・37 でくり返し起きている失敗で、
    毎回名乗る方針と真っ向からぶつかる。

    プロンプトに「名乗りは60文字に数えない」と明示し、
    **実装側の数え方も揃えた** (`countBodyRunes`)。先頭の一句に
    キャラクター名があれば落として数える。ログの超過警告も
    シミュレーションの字数検査 (`excessive_length` / `ready_too_long`) も
    これを通す。揃えないと、名乗ったぶんが超過として毎回検出され、
    **本当に長い発話が埋もれる**。

    #### ツグミだけは例外

    「そもそも名乗らない」が正体不明という設定の核 (§2.7 の表)。
    ところが**その指定は `urgent_style` にしか書いていなかった**ため、
    新しい平時ルールと衝突した。キャラシート本体に【名乗り】として明記した。
    シートの台詞例に「開始は名乗り+安心させる一言+質問」とあったのも、
    ツグミだけ文言を直した。

108. **課題の突破で発話するのをやめた** (ADR N-26b):

    テストプレイで違和感が出た。**ナビゲーターは装置を見ていない**のに、
    線が切れた瞬間に「切れたか? 次のランプはどうだ?」と切り出していた。

    押下の進捗 (決定48) も色合わせの完了 (決定104) も「見ていないから
    反応しない」と決めてきたのに、**ステージの区切りでだけその線が破れていた**。
    決定50 で「結果を断定しない」と直したのは**言い方の問題**として扱ったからで、
    そもそも切り出せる立場に無いという点は残っていた。

    #### 印を立てて、無応答の声掛けに拾わせる

    突破では発話せず、「突破したがまだ声を聞いていない」印
    (`GameSession.awaitingStageReport`) を立てるだけにした。
    プレイヤーが報告してくれば `player_message` で応じる。

    問題は**黙られたとき**で、突破が無線に流れない以上
    **誰も何も言わない**状態になる。切れたのかどうかも分からないまま
    時間だけが減るため、無応答の声掛け (P-9) に拾わせた (決定109)。

    決定26 で入れた「最終ステージでは発話しない」(次の課題が無いのに
    課題を捏造した) は、**全ステージで発話しなくなったことに吸収された**。

109. **突破後の無応答は、待ち時間も尋ねる中身も変えた** (ADR P-9b):

    決定108 で突破が無音になったぶんを、無応答の声掛けで補う。
    **通常の `silence` をそのまま使うと2つ噛み合わない。**

    #### 待ち時間 — 通常の幅では長すぎる

    既定は40〜60秒 (決定P-9)。突破直後に手が止まると**最大60秒、
    無線が完全に無音**になる。0.55倍に詰めて 22〜33秒にした。

    **詰めすぎない。** 突破直後は次の装置を見回している最中で、
    すぐ被せると考える時間を奪う (P-9 を入れたときと同じ理由)。

    実装で一点はまった — 待ち時間は**眠りに入る前に引く**ため、
    眠っている間に突破されると閾値を詰めた意味が無い。
    2秒ごとに起きて現在の閾値と突き合わせる形にした。

    #### 尋ねる中身 — 「どこで止まっている?」では合わない

    通常の `silence` は「手順のどこで止まっているか」を尋ねる。
    突破後は**線が1本切れたはずの頃合い**なので、聞きたいのは
    **切れたのか**と**いまランプがどう見えるか**の2つになる。
    トリガーを `silence_after_stage` に分けた。

    決定50 の「結果を断定しない」はここへ引き継いだ。
    尋ねる場面が変わっても、装置を見ていないことは変わらない。

    #### 印はセッション側に1つだけ持つ

    最初 `SilenceWatcher` 側にも同じ map を持たせたが、
    **同じ状態が2箇所にある**ことになる。セッションを正本にして
    Watcher は読むだけにした。

    #### 台本も差し替えた

    シミュレーションの台本は各ステージの最後を `stage_cleared` で
    締めていた。**実機で二度と鳴らないトリガーを検証していても意味が無い**ので、
    19本すべて `silence_after_stage` に置き換えた。
    「完了報告は漏洩ではない」「解除完了と取り違えていないか」の検査は
    そのまま新しいトリガーに掛かるよう `isAfterStageTrigger` でまとめた。

110. **モズの大阪弁が標準語に戻った — 例文を `output` に置いていた** (ADR N-21c・N-32):

    テストプレイで**モズ(大阪弁)が標準語で喋る**ことがあった。
    決定80 で `[triggers]` から例文を外したはずの問題が再発した形。

    #### `[triggers]` は見ていたが `output` を見ていなかった

    決定80 は「`[triggers]` に例文を書かない」と結論したが、
    **`output`(出力ルール)も全キャラ共通**で、しかも
    **全発話に載る**ぶん影響は `[triggers]` より強い。
    ここに以下が入っていた:

    - **表情タグの例文3つ** — 「[relieved] よくやった。見事な手際だ。どうぞ」
      「[urgent] 時間がねえ。手を止めるな。どうぞ」
      「[calm] 慌てるな、まず光っている色を言え。どうぞ」。
      **すべてフクロウ口調**。決定80 以前から残っていた
    - **コールサインの名乗り例** — 「こちらフクロウ」「こっちモズや」。
      決定107 で「毎回名乗る」に変えた際に足したもので、
      **標準語の名乗りが毎発話の頭に手本として載る**形になっていた。
      名乗りは発話の**先頭**に来るため、そこが標準語だと
      **続く本文まで引きずられる**

    #### 禁止のための引用も手本になっていた

    決定109 で足した `silence_after_stage` に、断定を禁じる例として
    「突破しましたね」「うまくいきました」と書いていた。
    **N-32 のとおり、禁止のために引用した文言はそれ自体が手本になる**
    (実測9件中5件で再現)。性質で書く形へ直した
    (「成功したことにして話し始めない」)。

    あわせて、同じトリガーの地の文に「**うまく切れた**のか」があった。
    これは決定80 で**モズを18回中17回標準語にした当の言い回し**
    (旧 `stage_cleared` の例文「うまく切れたか? ランプはどうなっている?」)で、
    例文としては消したのに**説明文として書き戻していた**。

    #### 外す前に委ね先を確認した

    決定80 の教訓どおり、**例文だけ外すと拠り所が消える**。
    表情タグは5人全員のシートの【台詞例】に
    「先頭の表情タグも例に含む」として既に置いてあり、
    モズも `[calm]` `[stern]` `[relieved]` `[urgent]` を
    大阪弁の台詞付きで持っていた。**委ね先がある**ことを確かめてから外した。

    名乗りも同様で、各シートの「待機完了」「開始」の例が名乗りを含む。

    #### 教訓

    **共通ファイルは grep で洗う**(N-32 に既にある)。
    今回は `[triggers]` だけ見て `output` を見ていなかった。
    **`「」` で囲まれた台詞を機械的に拾う**のが確実で、
    実際それで3件とも見つかった:

    ```
    python3 -c "import tomllib,re; d=tomllib.load(open('navigator/prompt.toml','rb')); print(re.findall(r'「[^」]*」', d['output']))"
    ```

    単語の引用(「どうぞ」「ステージ」)は口調を運ばないので残してよい。
    **落とすべきは文の形をしたもの**。

111. **`time_warning` を廃止し、次の返答へ添える形にした** (ADR P-11):

    `time_warning` はトリガー定義だけあって**鳴らす実装が無かった**
    (`navigator_design.md` の発話トリガー表には載っていた)。
    不要コードの整理中に見つかったが、**消すのではなく作り直した** —
    残り60秒を跨いだことは 7セグの表示でしか分からず、
    **手元を見ていないプレイヤーには伝わらない**ため。

    #### 独立した発話にしない

    残り時間だけを単独で鳴らすと、**プレイヤーの手を止めて無線を塞ぐ**わりに
    情報が増えない。閾値を跨いだあとの**次の返答へ一言添える**形にした。
    返答はどのみち流れるので、**無線の占有が増えない**のが利点。

    #### セッション中1回だけ

    残り時間が減るたびに言わせると急かすだけになる。閾値を跨いだ最初の1回で
    十分で、以後は交信スタイル「緊迫」が口調として効き続ける (§2.6)。

    印 (`GameSession.urgentNoticed`) は**送出できてから立てる**。
    生成に失敗した発話で立てると、一度も伝えないまま「伝えた」ことになり、
    告知が永久に消える。終幕 (爆発・解除) では告知しない — もう時間の話をする
    場面ではない。

    #### 字数は「引けない」ので枠を広げた

    ユーザーの要望は「字数制限に含めない」。名乗り (決定107) は
    先頭の一句を切り出して引き算できたが、**告知は文言が自由で位置も定まらない**
    ため同じ手が使えない。

    そこで**その1回だけ上限を広げる** (`urgentNoticeAllowanceRunes` = 20字)。
    「数えない」と言いながら数えていると、告知を入れたぶん超過警告が出て、
    **次に指示を締める材料にされる** — 削られるのは手順や危険の警告のほうになる
    (決定24 以来くり返している失敗)。

    #### 例文は置かなかった

    決定110 の直後なので同じ轍を踏まないようにした。告知ブロックは
    **全キャラ共通に渡る**ため、台詞を書くとその口調に全員が寄る。
    言い方はキャラシートの「残り60秒」の例に委ねてある。
    回帰テストで**引用の長さ**を見て、8文字以上の引用があれば落とす
    (単語の引用は口調を運ばないので許す)。

112. **終幕 (解除成功・失敗) でも律儀に名乗ってしまっていた** (ADR N-21・N-24):

    実機ログで「こちらヒバリです……失敗、ですね」という発話が出た。
    名乗ってから結果を告げると、事務連絡のように聞こえて締めくくりにならない。

    #### 名乗りの例外リストに終幕が抜けていた

    コールサインは「平時は毎回名乗る」方針で、例外は**緊迫時**と
    **キャラクター設定が「名乗らない」場合**の2つだけと書かれていた
    (決定107)。「どうぞ」には既に「交信が終わる場面 (解除成功・失敗) では
    付けない」という例外があった (決定46) のに、**名乗りには同じ例外が
    無かった**。「どうぞ」のルールのすぐ隣に名乗りのルールがあり、
    見た目は対になっているのに片方だけ終幕を素通りしていた。

    #### 直し方は「どうぞ」と揃えた

    出力ルールの例外リストに3つ目として追加し、`defused`・`exploded`の
    個別指示にも明記した (N-51 の教訓 — 共通ルールだけに頼ると
    詰む一言が落ちる)。文言は性質で書き、「どうぞ」の例外文とほぼ同じ
    理由付け (もう返事を求めない締めくくりであって、新しい呼びかけではない)
    にした。

    キャラ固有の言い回しは書かず、`[triggers]`本体にも例文を足さなかった
    (決定80・N-21c — 例文は全キャラの口調を寄せる)。

    回帰テスト `TestClosingMessagesHaveNoCallsign` を
    `TestClosingMessagesHaveNoDouzo` と同じ形で追加した。

113. **突破の直後に無応答の声掛けがいきなり発火した** (ADR P-9b):

    実機ログ:「✓ ステージ1 クリア」の**2秒後**に「線は切れたか、
    ランプはどうなっている?」と発話した。ユーザーには「以前廃止した
    はずの問いかけが復活した」ように見えたが、実際は `stage_cleared`
    (N-26b で廃止済み) ではなく `silence_after_stage` (P-9b で意図的に
    残した無応答の声掛け) が発火したものだった。

    #### 「計測を引き継ぐ」設計が裏目に出た

    突破直前にプレイヤーが喋っていれば、その時点からの経過をそのまま
    引き継ぐ設計だった (線を切る前の交信で稼いだ時間を捨てないため)。
    しかしこれは「プレイヤーが**突破の少し前から**(装置を眺める・
    資料を読むなどで)手を止めていた」場合を考慮していなかった。
    短縮後の閾値(22〜33秒)をとうに超えるほど前から黙っていれば、
    突破した瞬間に閾値超過が確定しており、次のtick(最大2秒後)で
    即発火する。

    #### 突破の瞬間から数え直す形に直した

    `onStageCleared` (game_events.go) で `awaitingStageReport` を
    立てるのと同時に、`SilenceWatcher.NoticeStageCleared` を呼んで
    計測をリセットするようにした。プレイヤーの発話でリセットする
    `Notice` とは別メソッドにした — 「ナビ自身の発話では計測を
    延ばさない」原則(ナビが喋ったことを応答と見なすと二度と
    声を掛けられなくなる)は、**装置からの通知**であるステージクリアには
    当てはまらないため、同じメソッドに混ぜると意味が変わってしまう。

    回帰テスト
    `TestSilenceWatcherStageClearedDoesNotFireImmediatelyIfAlreadySilent`
    を追加 — 突破の前から短縮後の閾値を超えて黙っていても、
    突破直後にはまだ発話しないことを確かめる。

114. **誤操作の発話を全廃止した** (ADR N-26。要望で決定。2026-09-08):

    以前は `wrong_action` のうち、色合わせのミス (`detail=color_match`)
    だけ発話しない扱いで (決定48)、線を切る操作を伴う誤操作
    (push_seq のボタン列ミス・forbidden_rotary の禁止位置停止) は
    「叱咤しつつ励まし、注意を促す」発話をしていた。

    #### 扱いを分ける理由が薄かった

    ナビゲーターは装置を見ていないので、色合わせのミスであれ
    ボタン列のミスであれ、**何が起きたかは分からない点は同じ**
    (N-26 の前提そのもの)。色合わせだけ発話を止めていたのは、
    記憶の上書き (ADR N-36) という固有の実害があったためで、
    「装置を見ていないから発話しない」という原則からは、
    本来なら誤操作全般に及ぶべきだった。

    加えて実害もある — 誤操作で無線が入ると、プレイヤーは
    ちょうど装置を操作している最中でも手を止めて聞くことになり、
    **気が散ってミスを誘う** (N-26 が既に押下中の反応を禁じているのと
    同じ理由)。

    #### 上面LEDの閃光をフィードバックに追加

    発話を止める代わりに、`ApplyPenalty` (game_task.cc) で
    上面LEDを強い赤 (255,0,0・最高光度) で100ms一瞬発光させる
    (`StatusIndicator::MakePenaltyFlashCommand`。ADR C-6e)。
    ブザーは既存のまま (C-6b)。誤操作は**閃光とブザーだけ**で伝わる。

    ログ (`EventWrongAction`) と `progress.WrongActions` カウンタ
    (ヒントレベル判定に使用。N-3 相当) は変更していない —
    後から何が起きたかを追う手段と、ヒントを進める判定材料は
    発話の有無と無関係に必要なため。

    `navigator/prompt.toml` の `wrong_action` トリガー文言は
    `stage_cleared` 等と同じ扱いで**削除せず残した**
    (将来また発話させる場合に fallback の汎用文へ落ちないようにするため)。

115. **初回のランプ確認で「表面の」を付け、上面フルカラーLEDと区別した**
    (要望で決定。2026-09-08):

    プレイヤーが装置を見て報告する対象は kLED A-E (表面の5色ランプ) だが、
    装置上面には別に kFullColorLed (PL9823) があり、ゲーム状態を色と
    点滅パターンで示している (Setup中は黄点滅・Playing中は赤点滅など)。
    ナビゲーターが第一声で単に「ランプはどうなっている?」と尋ねると、
    プレイヤーがどちらのランプを指しているか一瞬迷う余地があった。

    フルカラーLEDは運営(マネージャー)向けドキュメントにのみ登場し、
    プレイヤー向け紙資料 (`printed_materials.md`) やキャラクターの
    例文には一切出てこない。混同の芽を断つのはナビゲーターの発話側だけでよい。

    #### 初出だけ明確化し、以降は「ランプ」で通す

    `role` の第一声規定 (N-10 相当の一文) で「表面のランプ」と
    定義したうえで「以降は単に『ランプ』でよい」と明記した。全箇所を
    毎回フル表記すると `session_start` の 80 文字枠を圧迫し、`role` 内の
    他の指示からも注意が逸れる。混同が実際に起こり得るのはセッション中
    最初にランプへ言及する瞬間だけなので、そこだけ区別すれば足りる。

    フル表記「表面の5つの色別ランプ」ではなく短縮形「表面のランプ」を
    採用した。フル表記は発話としてやや説明的すぎるうえ、字数も余分に
    伸びる。

    `role` の例文 (「ランプはどうなっている? どうぞ」) と、先出し例外時の
    追記指示 (「ランプの状態も併せて尋ねてください」) は**変更しなかった**。
    前者は「装置を見ないふりをする」演技を示す例であって呼称の例では
    ないため、後者は既に規定文で定義済みの語を指すため、いずれも
    「表面の」を繰り返す必要がない。

    #### キャラクターの開始例文も揃えて直した

    調査の結果、`characters/*.toml` 5ファイルの「開始」台詞例には
    「ランプはどうなっている?」相当の質問文がそのまま書かれていた
    (例: フクロウ「…ランプはどうなっている? どうぞ」)。**ADR N-21c・
    N-52 (例文の言い回しは方針文より強く写される) により、`role` や
    `session_start` の方針文だけを直しても、例文が「ランプ」のままでは
    効果が薄いと判断した。** 5キャラ全員の開始例文の質問部分にのみ
    「表面の」を挿入し、口調・語尾・表情タグ・他の文言は一切変更しなかった。

    80 文字制限との整合を実測で確認した。各キャラの「開始」台詞例
    (「どうぞ」まで全体) は現行 44〜53字で、「表面の」を挿入すると
    いずれも +3字 (owl 53→56字・heron 49→52字・lark 48→51字・
    shrike 47→50字・thrush 44→47字) に収まり、80字上限にも
    決定37 の実測レンジ(名乗り+安心の一言 28〜37字)にも余裕がある。

    上面フルカラーLEDへ誤って報告した場合の切り返しは**今回のスコープ外**
    (将来の課題)。

    回帰は既存の `TestStagesAskForLampReportFirst` (対象は `hint_l1` の
    ため無関係・影響なしを確認済み)。文言確認は
    `go test -run TestSimulateAllStages -simulate -sim-stages 101 -v` で
    第一声の文字数・自然さを目視確認する。

116. **実在しない色名の報告を、実在する5色に一致するまで受け入れない**
    (コンソールモードでの実プレイ報告により発覚。2026-09-22):

    201 復唱で「茶色が点灯しています」という(装置に存在しない色の)報告を
    したところ、ナビゲーターがそのまま「茶色だね、それは順番に押すタイプだ」
    と手順(ボタン列)を読み上げてしまった。装置のランプは赤・黄・緑・青・白
    の5色 (`colorNameJA`。`scenario_template.go`) しかなく、それ以外の色名は
    音声認識の誤変換か言い間違いのはずだが、既存の役割定義 (`prompt.toml`)
    には**色の実在確認**という観点が無かった。

    既存の「意味の通らない報告をそのまま復唱してはいけない」というルール
    (決定 — 音量に合わせました等の文脈違反語を弾く規定) は、色の**体裁**を
    持つ語 (茶色・紫など) までは対象にしていなかった。モデルからすると
    「色として意味は通っている」と解釈でき、この規定だけでは弾けなかったと
    考えられる。

    `role` に**実在する5色を明記**し、それ以外の色名は実在しないと明言した
    うえで見直しを促す、という具体的な規定を独立して追加した(該当箇所を
    grepで見ると分かる曖昧な既存文の拡張ではなく、新しい一文にした — 既存文
    に混ぜると「意味が通らない語」全般の話に埋もれ、色特有の判定基準として
    読み取りにくくなるため)。

    201のシミュレーション台本に「茶色が点灯しています」という誤報告ターンを
    一時的に追加し、ツグミ・アオサギの2キャラで検証した。両者とも
    「茶色なんて色は、この装置には無いよ」「その色はこの装置には無い」と
    実在しないことを明言し、手順(ボタン列)へは進まずに見直しを促した。
    次のターンで正しい報告 (「ランプが1つ光っています」) が来て初めて
    列を読み上げた。

    このルールは201固有ではなく `role` (全ステージ共通) に置いたため、
    色名を報告させる全ステージに効く。回帰は
    `go test -run TestSimulateAllStages -simulate -sim-stages 201 -v` で
    誤報告ターンを台本に足して目視確認する(恒久的な台本追加はしていない
    — 誤報告は実運用のエッジケースであり、通常の誘導検証とは目的が異なる
    ため)。

117. **202 暗号電文は第一声で「単語」だと明言する**
    (コンソールモードでの実プレイ報告により発覚。2026-09-22):

    実プレイで、モズが「それモールス信号やから、資料1の対照表を見て解読
    してみ」とだけ伝え、**「1つの単語(ワード)を表示している」とは言わな
    かった**。プレイヤーは「モールス信号=1文字ずつの符号」だと思い込み、
    単語の区切りを意識せずに読み進めた結果、資料1に実在しない語
    (「MIMI」)を組み立ててしまった。

    従来の `hint_l1`/`procedure` は「それがモールス信号であること」としか
    書いておらず、**1文字の符号なのか単語なのかの区別**を明示していな
    かった。既存の `briefing`(ナビゲーターの内部知識)には「単語を繰り返し
    表示している」と書いてあったが、これはプレイヤーへの発話には直結せず、
    実際に読み上げられる `hint_l1`/`procedure` 側が漏れていた。

    `hint_l1` と `procedure` の冒頭に、**モールス信号だと伝えるときは必ず
    「1つの単語を表示している」と明言する**という指示を追加した。
    「モールス信号だ」とだけ言うと区切りが伝わらず、正しく1文字ずつ読めて
    いても区切りを誤って別の語になりうることも明記した。

    モズ・アオサギの2キャラで3回ずつシミュレーション検証し、第一声から
    安定して「1つの単語を表示しとる」「1つの単語を解読し」のように単語で
    あることが伝わることを確認した。

    (このステージの誤読対応そのものは決定116のN-9bとは別件 — N-9bは
    「実在しない色」の扱い、これは「実在しない単語」に気づいたプレイヤーを
    ナビゲーターが正しく受け止められるかの話で、`procedure` に**単語が
    資料1と一致しない場合は否定せずモールスの聞き直しに戻す**という指示も
    あわせて追加した。プレイヤーの「無い」という気づきを「存在しないはず
    がない」と頭ごなしに否定しないことが要点。)

    **追記(要望で決定。同日)**: 「単語」とだけ伝えても、テストプレイで
    「単語がどこにあるか分からない」という声が出た。資料1のどの列を
    見ればよいかが伝わっていなかったため、**「フォネティックコード」
    (『アルファ』『ブラボー』のような、無線で1文字を伝える決まった呼び名)
    だと種類まで明言する**指示を `hint_l1`/`procedure` に追加した。答えを
    教えることにはならない — 資料1自体がフォネティックコード一覧表であり、
    「何を探せばよいか」という検索対象の性質を伝えるだけである(ADR N-4の
    「装置に現れない情報は出し惜しみしない」と同じ考え方)。

    アオサギで5回シミュレーション検証し、5回中4回は第一声から
    「フォネティックコード」という語が出た(1回はモールス対照表とだけ
    言い、次のターンで補われた)。ばらつきの範囲内と判断し、実用上問題
    ないとした(ADR V-1: 検証は複数回)。

    回帰は `go test -run TestSimulateAllStages -simulate -sim-stages 202 -v`
    で第一声に「単語」が含まれるかを目視確認する。

118. **206 綱渡りは「ダイヤル」を明言し、危険位置の警告を言い切りで短くする**
    (要望で決定。2026-09-22):

    実プレイで、フクロウが「次は5に合わせろ。ただし0を通るときに止まるな」
    と発話した。プレイヤーから「0を通るってどういうこと?」と聞き返されて
    しまった。2つの問題があった:

    1. 「5に合わせろ」だけで**「ダイヤル」という言葉が無い** — 何を操作
       するのか名指ししていない。`procedure`/`hint_l1` は「目的位置まで
       回すこと」と動作は指示していたが、**対象の名称(ダイヤル)を使えとは
       書いていなかった**。
    2. 「${forbidden}を通るときに止まるな」という**通過を条件節にした
       言い方**は回りくどい。危険位置での**停止**が違反なのであって、
       通過そのものを言及する必要は無い。「0には止まるな」「0で止まるな」
       で十分に伝わる。

    `procedure` と `hint_l1` に、**「ダイヤルを${target}に合わせろ」のように
    「ダイヤル」という言葉を使うこと**、**「${forbidden}には(で)止まるな」と
    言い切りで短く伝えること**を明記した。「通るときに止まるな」のような
    言い方は明示的に避けるよう指示した。

    フクロウ・アオサギ・モズ・ヒバリの4キャラで検証し、いずれも
    「ダイヤルを3に合わせろ、ただし2では止まるな」のように短く安定した
    言い方になった(修正前の「0を通るときに止まるな」は再現しなかった)。

    回帰は `go test -run TestSimulateAllStages -simulate -sim-stages 206 -v`
    で第一声に「ダイヤル」が含まれ、危険位置の警告が「通る」を含まない
    短い言い切りになっているかを目視確認する。

    **追記(要望で決定。同日)**: 上記の修正後、テストプレイで**ゆっくり
    ダイヤルを回して失敗する**プレイヤーが見られた。「ダイヤルを3に
    合わせろ、ただし2では止まるな」という言い方は、速度に触れていない
    ため「慎重に、確実に」回ろうとする動きを誘発しうる。危険位置の直前で
    速度を落とすと、そのまま停止して即爆発する。

    `procedure`/`hint_l1` の指示例文に**「一気に」を「ダイヤル」と同格で
    必ず入れる**よう追加した(「ダイヤルを${target}まで一気に回せ」)。
    「一気に」を省くと慎重な操作を誘発し、危険位置上での減速→停止という
    事故につながることを明記した。

    5キャラ(フクロウ・アオサギ・モズ・ヒバリ・ツグミ)×2回、計10回で
    シミュレーション検証し、全回で「ダイヤルを3まで一気に回せ(回して/
    回すといい)、ただし2では止まるな」の形が安定して出ることを確認した。

119. **209 配電盤照合も「ダイヤル」の明言漏れがあった**
    (206の指摘を受けて全ロータリー使用ステージを横断調査。2026-09-23):

    206 綱渡り での「ダイヤル」明言漏れ(決定118)を受け、ロータリーを
    使う全ステージ(101/102/206/209/301/303)を横断確認した。101・102・
    301・303 は `procedure`/`hint_l1` に既に「ダイヤルを◯に合わせろ」等の
    明示的な指示例文があり、シミュレーションでも安定して「ダイヤル」が
    出ることを確認した。

    **209 配電盤照合だけ、シミュレーションで「ダイヤル」が出ないケースが
    あった**。旧 `procedure` は「読み取れたら復唱させて確認する」で止まり、
    復唱を受けたあとに**具体的な操作指示へつなげる一文が無かった**。
    実際 owl で3回試すと、1回は「その数字通りにダイヤルを回せ」と出たが、
    残り2回は「もう一度資料と照らし合わせて確かめろ」という確認止まりで、
    プレイヤーが自発的に「3まで回しました」と報告してようやく話が進む形
    だった(ADR N-50「プレイヤーの報告を否定しない」の運用で、確認を挟む
    こと自体は正しいが、**確認のあとにダイヤル操作への指示が続かない**
    のが漏れだった)。

    `procedure` に「受けたら『その数字にダイヤルを合わせろ』と、必ず
    『ダイヤル』という言葉を使って操作を指示する」「食い違いを確かめさせる
    場面でも、確認が済んだらダイヤルを合わせる指示に必ずつなげる」を追加
    した。209 は 206 と違い**ナビが数字を知らない立場**(ADR N-44)なので、
    どの数字に合わせろとは言えないが、「(プレイヤーが言った)その数字に
    ダイヤルを合わせろ」という**操作対象の名指し**はナビの知識に依存せず
    言える。

    panel-start 0/2/4 の3パターンで owl を検証し、いずれも「その数字に
    ダイヤルを合わせろ」で安定して次の操作へつながることを確認した。

    回帰は `go test -run TestSimulateAllStages -simulate -sim-stages 209
    -sim-panel-start {0,2,4} -v` で、危険/解除位置の報告後に「ダイヤル」
    という語を使った操作指示が続くかを目視確認する。

120. **207 息が合わないは、観点の説明で止めず切る指示までひと続きに言う**
    (要望で決定。2026-09-23):

    実プレイで、プレイヤーが「点滅速度が違う」「光る時間が短い」と正解に
    十分気づいているのに、ヒバリが「速さを比べるのではなく揃っているか
    見て」という**観点の説明を繰り返す**だけで、切る指示になかなかつながら
    なかった。ようやく出た指示も「その赤が光る短い線の部分を切ってください」
    という**装置の一部を指すような回りくどい表現**だった。

    `procedure`/`hint_l1`〜`l3` に、**「他と違う色を1つ言い当てたら、観点の
    説明を続けずに『その、他と違う点滅をしているランプと同じ色の線を
    切ってください』という一文で言い切る」**ことを明記した。「その光る
    短い部分を切れ」のような遠回しな言い方はしないことも明示した(切るのは
    線であって、ランプの光り方そのものではない)。

    ヒバリ・フクロウ・モズで検証し、いずれも報告直後に「その、他と違う
    点滅をしているランプと同じ色の線を切ってください(切れ)」と明確な
    指示が続くことを確認した。

121. **208 ジャストカットは、タイミングだけでなく切る対象と動作まで
    ひと続きに伝える**(要望で決定。2026-09-23):

    実プレイで、ヒバリが「小数点のすぐ左の数字が8になった瞬間を狙って
    くださいね」とだけ言い、**「狙って何をするのか」を伝えなかった**。
    プレイヤーが「8になったら全部の線を切っていいのか」と聞き返しても
    「全部の線じゃないですよ」と否定するだけで、結局「光っているランプと
    同じ色の線を切ってください」まで揃うのに3往復かかった。

    `procedure`/`hint_l1`〜`l3` に、**「タイミング」+「対象(光っている
    ランプと同じ色の線)」+「切る」を1つの発話でひと続きに言い切る**ことを
    明記した。「◯になった瞬間を狙え」とだけ言って切る指示を省略しないよう
    明示した(206・207 と同じ「対の操作は組で書く」パターン。ADR N-48)。

    ヒバリ・フクロウで検証し、いずれも第一声から「小数点の左の数字が9に
    なった瞬間、光っているランプと同じ色の線を切ってください(切れ)」と
    タイミング・対象・動作がひと続きで伝わることを確認した。

122. **209 は、装置にありえない見え方の報告を「1回目は控えめに聞き返し、
    2回目は不正解色を切らせる」という二段構えにした**(要望で決定。
    2026-09-23):

    ※ **この決定は決定124 で覆った**(209固有ではなく共通化し、
    判定をサーバー側へ移した。見え方の食い違いでは切らせない)。

    決定119(209の「ダイヤル」明言)を検証中、「緑と赤が交互に点灯して
    いる」という**このステージに存在しない見え方**の報告に遭遇した。
    209のランプは点灯(複数色同時)か解除位置での点滅(1色)のどちらかで、
    色が交互に入れ替わる表示は無い。

    最初の修正では「交互に点灯などという表示はこの装置には無い」と
    **断定して否定する**文言にしたが、テストプレイで「最悪」との指摘を
    受けた。ナビは装置を見ていない設定(ADR N-50)なので、見たことも
    ない状態を頭ごなしに否定する態度が不自然に響く。**禁止したい言い方を
    そのまま例文として書いたことで、それが手本になっていた**(ADR N-32
    と同じ失敗パターン)。

    方針を二段構えに変更した:
    1. **1回目**は「よく分からないな、もう一度確認して状況を教えてくれ」
       とだけ言う。装置の仕様や表示の説明を付け加えず、この一言だけで
       発話を終える。
    2. **2回目以降も同じ食い違いが続いたら**、それ以上は聞き返さない。
       ${cut} 以外から抽選した `wrong_color`(新設の random 変数)を使い、
       「${wrong_color}色の線を切ってくれ」と具体的な色を指定して切らせる。
       正解ではないことは伝えない — 正しい報告に戻れないまま先へ進めない
       状況の最終手段で、切った結果(即爆発)で状況を動かす。

    **この不正解色を切らせる方針はADR S-2b(誤切断は即爆発。ペナルティで
    続行させない)と衝突しない** — 元々誤った線を切れば即爆発する設計を
    変えるのではなく、「食い違う報告を繰り返すなら、その報告のまま操作を
    進めさせる」という誘導方針の話であり、爆発の扱い自体は変えていない。
    ユーザーの意図は「不正解を切らせることでプレイヤーに誤りを痛感させ、
    以後の報告を正確にさせる」というもので、209固有の対応として導入した
    (他ステージへの一般化はしていない)。

    フクロウ・アオサギ・モズ・ヒバリの4キャラで、1回目→控えめな聞き返し、
    2回目→不正解色の指定、の2段階が機能することを確認した(フクロウは
    1回目にもやや装置仕様への言及が残ったが、断定的な否定文は解消された)。

123. **意味の通らない報告への聞き返しルールが実質的に機能していなかった**
    (要望で決定。2026-09-23):

    「STTがうまく聞き取れなかったとき、ナビゲーターが聞き取れなかったと
    伝えて再度教えてと問いかけるようにしてほしい」という要望を受けて
    調査したところ、**既存の共通ルール(prompt.toml)がそもそも機能して
    いなかった**ことが判明した。

    従来は「意味の通らない報告は復唱せず聞き返す」(47行目)と「聞き取れ
    ない・曖昧な場合はもう一度どうぞと聞き返す」(65行目)の2つのルールが
    分散しており、どちらも**代わりに何を言うかの具体的な型**を指定して
    いなかった。「音量に合わせました」という意味不明な報告をシミュレー
    ションで送ったところ、**5キャラ全員が復唱してしまい**(「音量だと?」
    「音量調整ですね」「音量に合わせたて」「音量ですね」「音量か」)、
    聞き取れなかった扱いにせずそのまま次の質問を続けていた。禁止だけを
    書いて代替の言い方を具体化しなかったため、実質的に死んだルールに
    なっていた。

    2つのルールを整理し、**「(1)聞き取れなかったことを伝える一言 +
    (2)もう一度どうぞ、の2つだけを言う」**という具体的な型に統合した。
    届いた語をそのまま引用する・その語に相槌を打つ・次の質問を重ねる・
    理由や装置の状態説明を付け加える、をすべて明示的に禁止した。
    65行目の「2回続けて聞き取れない場合ははい/いいえ質問に切り替える」は
    残し、47行目の意味不明な報告のケースと統合した。

    修正後、同じ「音量に合わせました」をシミュレーションで再度送ったところ、
    フクロウ・ツグミは「聞き取れなかった。もう一度どうぞ(教えてくれ)」の
    完璧な形になり、アオサギ・モズ・ヒバリも語を軽く拾いつつ「聞き取れ
    なかった、もう一度どうぞ」へ必ずつなげるようになった(以前のように
    そのまま話を進めてしまうことは無くなった)。

    回帰は任意のステージ(202等)の台本に意味不明な報告のターンを一時的に
    挟み、`go test -run TestSimulateAllStages -simulate -sim-stages 202 -v`
    で複数キャラを目視確認する。

124. **誤った報告の扱いを共通化し、判定をサーバー側へ移した**
    (要望で決定。2026-09-23):

    決定122 の二段構え(1回目は聞き返し、2回目は不正解の線を切らせる)は
    **全ステージ共通のつもり**だったため、共通ルールへ移した。
    まず `prompt.toml` の role に書き、不正解の線をプロンプトへ常時渡す形で
    シミュレーションしたところ(201「茶色」×2・209「交互」×2、4キャラ):

    - 2回目に不正解の線を切らせたのは **8回中5回**
    - 1回目の「否定・断定しない」は**ほぼ守られない**(「そんな色はねえ」
      「茶色という色は存在しません」)
    - ツグミは「交互に点灯」を**正しい報告として通した**
    - 「見え方として成り立ちません」「もう同じ間違いはさせん」など、
      **仕組みを明かす発言**が出た

    判定も回数も生成AIが会話ログから行っており、揺れていた。
    さらに見え方の判定には構造的な問題がある — 207 の位相ずれを正しく
    観察したプレイヤーほど「**交互に**光っている」と言いやすく、正しい報告を
    誤りと判定すれば、正解に気づいた人を爆発させてしまう。

    そこで次のように分けた:

    - **5色以外の色名**: サーバーが文字起こしから機械的に検出し、課題ごとに
      数える(`detectInvalidColor` / `StageProgress.NoteReport`)。1回目は
      **聞こえた色名を復唱して**確かめさせ、2回目以降は不正解の線を切らせる
      指示を**独立ブロック**で渡す(`invalidColorBlock`)。不正解の線は
      **2回目の場面でだけ**渡す。
    - **不正解の線**は「今の正解」「前の課題で切った線」を除いた色
      (`decoyCutColor`)。切り済みの線を指すと切ろうにも無い(最初の要望の
      「現存する切れる線」)。最大4ステージ・5本なので必ず1本残る。
    - **見え方の食い違い**: 復唱して確かめてもらうだけにし、何度続いても
      切らせない。
    - 検出語から**LEDの見え方として言われうる語**(オレンジ・橙・水色・
      黄緑・紺)を外した。黄色のLEDが橙に見える等で、正しい報告を
      爆発させうる。実機の見え方を確認してから足す。

    **音声認識の誤変換は考慮しない**(ユーザー判断)。ナビが色を復唱するので
    プレイヤーは聞き違いに気づいて言い直せる。テストプレイで、ナビが色を
    取り違えて復唱し、プレイヤーが言い直す場面が実際にあった。

    209 固有だった `wrong_color` 変数と二段構えの文言は削除し、209 の
    進め方には**このステージで起こりうる見え方**(2〜3色点灯 / 赤だけ点灯 /
    1色点滅+他は点灯・消灯)を明記して、共通ルールの判断材料にした。

    回帰は `TestDetectInvalidColor` / `TestNoteReportCountsPerStage` /
    `TestInvalidColorBlockEscalates` / `TestDecoyCutColorAvoidsCutLines`。
    発話は 201・209 の台本に誤報告ターンを一時的に足してシミュレーションする。

    **追記(要望で決定。2026-09-24)**:
    - 1回目の返しは「その色は無い」と否定する代わりに、「**赤・黄・緑・青・白の
      5色だけ**」と**色名を並べて**伝える形にした。「5色だけ」とだけ言っても
      何色か分からないため、色名まで並べる。否定はシミュレーションで5キャラ中
      3キャラに出ていた(「そんな色はあらへん」「存在しません」)。修正後、
      フクロウ・モズは「赤・黄・緑・青・白の5色だけ」で返すようになった。
      アオサギは1回目がAPIエラー(429)で検証できず、別の発話で
      「茶色という色は存在しません」が残った。
    - 実機では**黄がオレンジ・橙に、青が水色に見える**可能性がある(ユーザー確認)。
      これらは検出対象から外したまま、role に「オレンジ・橙は黄、水色は青の
      報告として受け取り、正式な色名で復唱する」を足した。黄緑・紺は見間違えの
      対象ではないため検出対象に加えた。ツグミは「オレンジ、つまり黄」と
      言い直したが、フクロウは「オレンジだな」のまま受けた(進行は正しい)。

125. **課題の進め方が扱いを決めている報告は「聞き取れなかった」扱いにしない**
    (要望で決定。2026-09-24):

    決定123 で「意味の通らない報告は『聞き取れなかった』+『もう一度どうぞ』だけ
    返す」と強化したため、202 で読み違えた単語(MIMI、音声認識で「ミミ」「耳」)が
    この対象に入りうるようになった。202 の進め方には「資料に無い語なら
    モールスを見直させる」と書いてあるが、どちらのルールを選ぶかは生成AI任せで、
    共通ルール側を選ぶと「聞き取れなかった」が繰り返され、プレイヤーは
    解読の誤りに気づけない(無線の不調と取り違える)。

    - 共通ルールに「解読した単語・資料から読んだ数字など、課題の進め方に扱いが
      書かれている報告は対象外」と明記した。
    - 202 の進め方は、資料に無い語が届いたら(カタカナ・漢字で届いても)解読の
      報告として扱い、否定・断定せず**「フォネティックコード(資料1の
      フォネティックコード列の単語)のどれかになるはず」**と伝えてモールスを
      見直させる形にした(ユーザー案)。202 は表示がフォネティックコードだと
      分かっているので、探す範囲を示せる。正しい語や綴りは教えない(ADR N-45)。

126. **role に残っていた古いルール2つを今の方針に揃えた**
    (プロンプト見直しで発見。2026-09-24):

    - **「指針が伝えるよう指示していれば、手順を第一声に含める」例外を削除**。
      ADR N-49(第一声は観察だけ・例外を持たない)と逆で、昔の方針が残っていた。
      最初の課題は `session_start` の「指針にそう書いてあっても手順は第一声に
      入れない」が上書きしていたが、**2つ目以降の課題の入り口には上書きが無い**。
      2つ目が 201 ならランプ報告の前にボタン列を、206 なら危険位置を先に言いうる。
      「2つ目以降の課題の入り口でも同じ」と明記した。
    - **「行動に直結する報告は相手の肯定を得てから次の指示に進む」を削除**。
      ADR N-55(報告を受けたら手順を最後まで渡す)と逆向きで、文字どおりには
      無線の往復が1回増える。シミュレーションではあまり効いていなかったが、
      209 で数字を報告されたナビが確認で止まった件(決定119)の一因だった可能性が
      ある。**復唱は残し**、「短く復唱し、同じ発話で次にやることを伝える」とした。
      復唱は誤った報告の扱い(決定124)の前提でもある。

    `TestNavigatorPromptContentPreserved` が「復唱して確認」の文言を見張って
    いたため、「短く復唱し」「同じ発話で次にやること」を照合するよう更新した。

127. **課題の突破後、最初の報告への返答に「切り替わり直後」を伝える**
    (決定126 の検証で発覚。要望で決定。2026-09-24):

    2つ目以降の課題の入り口をシミュレーションしたところ、プレイヤーの
    「切れました」(前の課題の線を切った正しい報告) に対し、フクロウが
    「線を切っただと? 馬鹿野郎」、ヒバリが「線を切っちゃいましたね……」と
    **誤りとして受けた**(どちらも 201)。ナビのプロンプトには**今の課題の知識
    しか無く**、201 は「押し切ってから切る」課題なので「押す前に切った」と
    誤解した。206 とモズ・ツグミでは起きなかった。

    突破時に立てる `awaitingStageReport` は、プレイヤーの声が届いた時点
    (`NoteQuestion`) で下ろすため、返答のプロンプトを組む頃には消えている。
    **下ろす直前に `firstReportAfterStage` へ写し**、次の返答1回だけ
    「課題の切り替わり直後」ブロックを渡す(`JustAdvanced`)。中身は
    「直前に前の課題の線が切れた。『切れた』は前の課題の報告で正しい操作。
    叱らず受け止め、ランプの報告が無ければ尋ねる」。例文は置かない(N-52)。

    回帰は `TestFirstReportAfterStageIsMarkedOnce`。シミュレーションは
    台本の silence_after_stage 直後のプレイヤー発話を突破後の最初の報告とみなす。

128. **禁止したい言い方の引用と、ステージの台詞例文を洗い直した**
    (プロンプト見直しで発見。要望で決定。2026-09-24):

    **引用による禁止(ADR N-32 違反)を性質の記述へ書き換えた**:
    - `prompt.toml`: 色名を補う違反例(フクロウ口調の命令形)、「音量ですね」
      「音量だと?」(**修正後のシミュレーションでアオサギ・ヒバリが実際に再現**)、
      聞き取れなかったときの言い方の例、爆発時の禁止文言(「次は間に合います」
      「また挑戦しましょう」「お疲れさまでした」「青やて言うたやんか」)
    - 103「今ので合ってる」/ 104『見比べてください』/ 205「それが${rank}番目だ」
      『何色だった?』/ 206「通るときに止まるな」/ 207「その光る短い部分」/
      208「◯になった瞬間を狙え」/ 209「ロータリーが◯番にありませんか」
      『それは違う』『◯番やない』(**実プレイで実際に言って爆発につながった言い方**) /
      304「見ておけ」「見ててや」「狙え」「待て」「今切れ」、実測の台詞そのもの
    単語単位の禁止(303 の「瞬間」「一瞬」など)は N-21c の「単語は可」に従い残した。

    **決定118・120・121 で入れた台詞例文を要素の列挙に直した(ADR N-52)**:
    206『ダイヤルを${target}まで一気に回せ』/ 207「その、他と違う点滅を
    しているランプと同じ色の線を切ってください」/ 208『小数点の左の数字が
    ${digit}になった瞬間、光っているランプと同じ色の線を切ってください』を、
    「(1)…(2)…(3)…をひと続きで言う。言い回しはキャラシートの口調で」の形へ。
    206 の hint_l2 にあった命令形の助言(『間で一度止まってよい』等)も内容の記述へ。

    **207 では実害が出ていた**: モズが「その、他と違う点滅をしている…切って
    ください」と**標準語の敬語で丸写し**し、フクロウ・ヒバリも書き出しの
    「その、」まで同じ文を写していた。修正後はモズ「その光り方が違うランプと
    同じ色の線を切れ」、フクロウ「他と違う光り方をしているそれと同じ色の線を
    …切れ」、ヒバリ「その光り方がずれているランプと同じ色の線を切ってください」と
    各キャラの口調に分かれた。206(ダイヤル・一気に・止まらない)、208(瞬間・
    同じ色の線・切る)、205(順位の色を認めて切らせない)も要素が保たれた。
    残課題: モズ 206 の L3 で「切る線の色はこっちからは言わんから」と
    **方針をそのまま口にした**(output の「指針を書き出さない」違反。既存の型)。

129. **ヒントレベル (L1〜L4) を廃止し、段階は `procedure` の条件で書く**
    (プロンプト見直しで発見。要望で決定。2026-09-24):

    プロンプト見直しで次の2点が分かった。

    - 前倒しに使う「質問回数」は、実際には**全発話数**だった
      (`NoteQuestion` がプレイヤーの発話のたびに加算)。2回話すと L2、
      4回で L3 になり、201 で順調に報告しているだけで数十秒で L3 に達する。
      誤った報告・音声認識の誤変換・突破後の「切れました」も数えていた。
    - プロンプトに入るのは**今のレベルのヒント1つだけ**で、L2 に上がると
      `hint_l1`(ランプの報告を受けたときの返し方。ADR N-35 でここに書く
      決まりだった)が消えていた。

    誘導の大部分は常に入る `procedure` が担っていて、L2/L3 の差はほぼ
    機能していなかった。ユーザー判断で**完全に廃止**した(イージーの L4
    直言も含む)。段階的に出していたヒントは、`procedure` に「こう報告され
    たら、これを伝える」「迷っていたら、これを助言してよい」という**条件**
    として書く。「最悪、最初から出てしまっても構わない」前提で決めた。

    変更:
    - コード: `HintLevel`・前倒し・`HintPolicyText` (レベル別) を削除し、
      共通の `StageGuidanceText` に置き換えた。`observation` / `observed`
      (出力スキーマからも)・難易度とステージの `[hints]`・`keep_cut_secret`・
      `StageBudgetMS` を削除。**切る線の色名は常にプロンプトから伏せる**。
      `NoteQuestion` は `NotePlayerReport` に改名(回数は数えない)。
    - 全18ステージ: `hint_l1`〜`l3` / `observation` を `procedure` に統合。
      例: 104 は `procedure` が無かったため新設し、報告の中身(2つ点滅まで /
      速い遅いまで)で返し方を分ける条件にした。301 のダイヤル位置は
      「引けずに詰まっていたら伝えてよい」、203・209 の資料の読み方は
      「迷っていたら具体的に説明してよい」と条件付きにした。
    - `prompt.toml`: 「許可ヒントレベルの範囲で」を「進め方の条件に沿って」へ。
    - シミュレーション台本: ターンごとの `HintLevel` を削除。色漏れは常に検査。

    シミュレーション(全18ステージ、フクロウ)で所見0件(API 429 を除く)。
    104 は速さの違いを尋ね、差が報告されてから「速く点滅している方」を
    伝えた。204 は押し方と覚えることを1発話で両方伝えた。

    回帰は `TestStagesHaveNoHintLevelFields` / `TestPromptNeverContainsCutColor` /
    既存の `TestStagesAskForLampReportFirst`・`TestUnobservableInfoInProcedure`
    (いずれも `hint_l1` から `procedure` を見るよう変更)。

130. **方針は一人称で書かない — 「こちらからは言わない」が台詞になった**

    ヒントレベル廃止後の全ステージシミュレーション (モズ) で、206 綱渡りの返答に
    「色はこっちからは言わんから」が出た。切る線の色を伏せる方針を、
    プレイヤーへそのまま説明している。

    原因は方針の書き方。「切る線の色名は**こちらからは言わない**/言いません」が
    共通方針 (`StageGuidanceText`)・`prompt.toml`・9ステージの `answer` の計12箇所に
    あり、**一人称なのでナビの台詞としてそのまま成立する**。モズはこれを大阪弁に
    直して写した (ADR N-20「指示文も写される」と同じ現象)。加えて `prompt.toml` の
    「方針を書き出すな」の禁止が、禁じたい文言そのものを引用していた (N-32 違反)。

    変更:
    - 12箇所を「色名は**発話に入れない**」へ。ナビの台詞にならない形にした。
    - 共通方針に「色名を出さない理由や、自分が何を伝えて何を伝えないかは
      プレイヤーに説明しない」と、代わりの指し方 (ランプの見え方で指す・何色か尋ねる)
      を追記。
    - `prompt.toml` の禁止を引用から性質へ (「自分の進め方についての説明」)。
    - シミュレーションの `meta_output` に `colorPolicyPattern` (「色」+否定) を追加。
      方言で言い換えられるので固定語では拾えない。回帰は
      `TestColorPolicyPatternCatchesPolicyStatement`。

    検証: モズ 206 ×5 (34発話)、モズで色を伏せるステージ群
    (103・201・202・208・301〜304) ×2 (96発話)、フクロウ全18ステージ (106発話)。
    **方針の説明は0件**。所見は API の 429/504 のみ (12件)。
    203 で色を尋ねられたフクロウは「俺には見えねえ」と知らない側で断った (N-6)。

131. **応答の生成に失敗した報告は、5色以外の色名の回数に数えない**

    5色以外の色名の報告は、発話を受けた時点で `NotePlayerReport` が数えていた。
    続く応答の生成が API エラー (504 など) で失敗すると、プレイヤーは聞き返しを
    受けていないのに回数だけ1に進み、**次の報告でいきなり2回目 (不正解の線を
    切らせる) の扱い**になる。課題切り替え直後の印 (`firstReportAfterStage`。
    決定127) も同じく消費されたまま失われていた。

    `generateReply` で生成に失敗したら `StageProgress.UndoReport` で数を戻し、
    突破直後の印も立て直す。応答待ちの間に次の報告が届いて数が進んでいた場合は
    触らない (後の報告のぶんを消さないため)。429 は ADR G-7 で1回再試行するので、
    ここへ来るのは主に 504。回帰は `TestUndoReportRollsBackFailedReply`。

132. **5色以外の色名への1回目の返しは「名前がずれているだけ」という前提で書く**

    決定124 の1回目の指示は「否定・断定する言い方はしない」という**禁止**だった。
    専用の実APIテスト `TestInvalidColorFirstReplyAsksAgain` (5キャラ × 茶色・紫・
    ピンク) で測ると、フクロウが「ピンクのランプなどない」と言い切った (15回中1回)。

    | 版 | 否定・断定 | 内訳 |
    |---|---|---|
    | 禁止で書く (決定124) | 1/15 | フクロウ |
    | 1・2・3 の順番で指定 (N-53)、「有る無しには触れず」を添える | 2/45 | フクロウ「茶色なんて色はねえ」 |
    | 同上 + 復唱を「聞き取った内容の確認として」 | 6/45 | フクロウ「そんな色はねえ」が5回 |
    | **ランプは光っていて名前がずれているだけ、を前提に置く** | **0/45** | — |
    | 同上 + 「5色**だけ**なので」を戻す | 3/45 | モズ「茶色やない」「ピンクやないで」 |
    | 前提を置き、3 を「**何色か**教えて」にする (C案) | 3/45 | フクロウ「紫という色はねえ」 |
    | **C案 + 「プレイヤーにはそう見えている報告として受け止める」+ 5色**すべて**を並べる** | **0/45** | — |

    - 順番指定だけでは足りなかった。フクロウはキャラシートの差し戻しの指針
      (武骨に短く・手を止めさせる) に引かれて問い詰める調子になる
    - 「有る無しには触れず」の**「無し」自体が呼び水**になった可能性がある
      (添えた版で悪化した)
    - 効いたのは、**否定する理由そのものを無くす**前提 — ランプは確かに光っていて、
      色の名前がずれているだけ (LED の見え方には幅がある)。返答は
      「茶色だな、了解。それは赤、黄、緑、青、白のどれに近い?」の形に揃った
    - 「5色だけ」は決定124 でユーザーが選んだ言い回しだが、「だけ」を入れると
      「〜やない」と否定が戻る。「どれに近いか」は否定こそ 0/45 だったが、
      見直さずに当て推量で答えるおそれがある。**ユーザー判断で「何色か」を
      尋ねるC案**にした。C案だけではフクロウが紫で否定した (3/45) ため、
      報告を「そう見えている」ものとして受け止める前提を足して 0/45。
      フクロウは「赤か青のどちらだ」と2色に絞ることもあったので、
      **5色すべてを並べる**と明記した

    テストは否定の判定を機械に任せきれない (「分からない」も拾う) ため、
    返答をすべてログに出し、否定形の候補に `?` を付けて目で確かめる。

133. **全キャラの再検証で出た3件 (一人称の方針の残り・102 の押したまま・口癖と語尾)**

    ヒントレベル廃止 (決定129) と決定130 のあと、アオサギ・ツグミ・ヒバリの
    全ステージ、全5キャラの終幕・無応答を回した。

    **(1) 一人称の方針が `procedure` に14ステージ分残っていた。** 決定130 は
    `answer` の決まった言い回しだけを置換しており、`procedure` の
    「**色名はこちらから言わない**」「**正解の単語をこちらから言わない**」
    (202)・「**キーワードをこちらから言わない**」(301) が漏れていた。
    「**プレイヤーより先に**発話に入れない」へ揃えた。単に「発話に入れない」
    とすると、プレイヤーが言った色・単語の**復唱 (正規の照合手順)** まで禁じて
    しまう。203 だけは復唱自体を禁じる課題なので「発話に入れない」のまま。
    共通方針 (`StageGuidanceText`)・`prompt.toml` も同じ形にした。

    **(2) 102 ホールド&カット で「押したまま」が落ちた** (ヒバリ1回)。
    「ボタンを押して、線を切って」と言い、押しながら切るという課題の本体が
    抜けた。`procedure` の (2) に「必ず動作でつなげる」と書いてあっても落ちる。
    `must_say` に出した (ADR N-51)。

    **(3) 口癖と語尾。**
    - ヒバリは口癖「大丈夫です、たぶん!」を、「このまま切っていいですか」への
      返事に付けた (「思い切って切っちゃいましょう、大丈夫です、たぶん!」)。
      モズの「知らんけど」と同じ構図 (ADR N-21b) なので、同じ形で
      「切る・回す・押すの指示と、切っていいかへの返事には付けない」と書いた
    - ツグミは禁じている古風な語尾を使った (ステージ 110発話中2回「〜さね」、
      解除成功 3回中2回「止めちまった」)。シートは「〜さね」「〜ちまった」を
      **引用して禁じ**、さらに「『止めちまった』ではなく『止めたんだね』」と
      **A ではなく B** の形で書いていた (N-32・N-53)。引用をやめ
      「語尾は今の話し言葉のまま。古風な語尾・江戸っ子風の縮め方は使わない」と
      **性質で**書き直した。解除成功 0/6・ステージ 0/48 になった
      (N-21b は方言キャラが**方言として使いうる語**の話で、ツグミは方言キャラではない)

    **残課題 (ユーザー判断待ち)**: ツグミの爆発は6回中6回が一字一句同じ
    (「失敗したね。聞こえてる? まあ、こういう日もある。それじゃ、また。」)。
    シートの例示 (「まあ、こういう日もある」「それじゃ、また」) がそのまま出ている
    (ADR N-29)。「それじゃ、また」は ADR N-25 (次がある前提の言葉を使わない) とも
    ぶつかるが、ツグミの不気味さとして意図した演出でもある。

134. **「伏せてあります」を「あなたにも分からない色」へ / ツグミの爆発 / 102 の入り口**

    **(1) 正解欄の注記がナビに「伏せている」立場を取らせていた。**
    フクロウが 203 で「色は教えられん」「言えん」と断った (9回中3回)。203 の
    `procedure` には「分からない・見えないと言う」と書いてあったが、全ステージ共通の
    注記「⚠ **切る線の色名は伏せてあります** … 口に出してはいけません」が
    「知っているが言えない」という自己認識を与えていた。注記には
    「報告された色名の照合に使う」ともあり、伏せた色で照合はできないので
    中身も食い違っていた。

    注記を「上の◯◯は**あなたにも分からない色**です。装置を見ていないので、
    プレイヤーが確かめるまで分からない。報告された色名は、進め方にある手がかり
    (どのランプと同じ色か、資料のどこを引くか) に沿っているかで受け止める」へ。
    203 の断り方も箇条書きから**1・2・3 の順番**(見えない → 資料のどこを見るか →
    端子番号) にした。フクロウは 9回中1回まで下がった。

    ツグミも 203 で「色は教えられないよ」と言った。シートの【ヒントの味付け】が
    「**答えを教えるのではなく**、見るべき場所を呟いて気づかせる」で、
    A ではなく B の A (教えない) が呼び水になっていた (N-53)。B だけにして 8回中1回。

    回帰: 全5キャラ × 全18ステージ。フクロウ・ヒバリ 所見0。アオサギ・モズは
    203 の字数超過と 303 の必須語1件 (従来からの揺らぎ)。ツグミは突破後の声掛けで
    ランプを尋ねない回が18回中2回 (「それとも、まだ迷ってる?」で止まる。従来からの揺らぎ)。

    **(2) ツグミの爆発を指針だけにした (ユーザー判断)。** 決定133 の残課題。
    指針に例として挙げた「まあ、こういう日もある」「それじゃ、また」がそのまま
    6回中6回出ていた (ADR N-29)。

    | 版 | 結果 |
    |---|---|
    | 例示を消し「受け流す独り言で締める」 | 締めが「まあ、こういうこともあるさ」に 5/6 で収束 |
    | 独り言の向きを挙げる (手元・周波数・今日・用事) | 「こんな日もあるさ」6/6、呼びかけが 5/6 で消えた |
    | 3文の順番を番号で指定、締めは「自分の話へ戻る」 | 締めは散ったが、「次の回路の設計図でも引くか」 (黒幕めいた匂わせ。禁止) が 5/12 |
    | 締めを「装置とも仕事とも関係ない身の回りのこと」へ | 匂わせ 1/12。ただし実運用で**意味の通らない文**が出た (「雨の日の買い出しでも忘れるとしようか」。1文目も「派手にいったね」で失敗の語が無い) |
    | **1文目に「失敗」の語を必ず入れる / 締めは「このあと自分がする、ありふれた用事を普通の言い方で」** | 12/12 で意味が通る。前半2文はほぼ固定 (「失敗したね。……聞こえてるかい。」)、締めは「お茶」4/12 |

    散らすほど意味が崩れ、意味を通すほど揃う (ADR N-20)。**意味が通ることを優先**した。

    **(3) 102 で報告直後の返事が「ダイヤルを2に」だけになった** (ヒバリ 3回中3回。
    決定133 の `must_say` を足したあとも)。102 の `procedure` 冒頭の
    「1回の発話で伝えるのは1つだけ」と (2) の「2つを1発話でまとめる」が食い違い、
    ヒバリのシートの「次にやること1つで切る」も分ける側に働いた。冒頭を
    「報告直後の指示だけは、ダイヤルと押しながら切るを1発話でまとめる」とし、
    ヒバリのシートに「進め方がまとめて言うよう指示していれば分けない」と足して 4/4。

135. **光っていない色の報告も「誤った色の報告」として数える**
    (実運用報告・要望で決定。2026-09-25):

    208 ジャストカット で、白が点灯しているのに「緑が点灯しています」と報告した
    ところ、ヒバリがそのまま「タイマーの…数字が2になった瞬間に、光っている
    ランプと同じ色の線を切ってください」と返した。

    ユーザーの意図は決定122・124 の時点から「**誤ったランプの報告は共通処理で、
    1回目は聞き返し、同じ誤りが続けば必ず失敗する線を切らせる**」だった。
    実装は決定124 で判定をサーバーへ移した際、機械的に判定できる
    **5色以外の色名だけ**に絞っており、**5色の中の光っていない色は検討から
    漏れていた**。ナビは切る線の色を知らない (常に伏せる。決定129) ので、
    自分では誤りに気づけない。

    **光っていない色を「光っている」と報告した誤りに絞る** (ユーザー判断)。
    点灯と点滅の取り違えは見ない — 207 は5色すべてが点滅しているので、
    「交互」と言っても誤りにならない。誤検知は、ナビが色を復唱するので
    プレイヤーが気づける (ユーザー判断)。

    実装:
    - `stageShownColors`: Core へ送る表示から、その課題で光りうる色を集める。
      `leds`、209 の全ダイヤル位置の表示と解除位置の切る線、103/201 の押し切り後の
      切る線。204 は押すたびに変わるので判定しない (nil)。
    - `detectUnshownColor`: 発話を文節に分け、線・ボタン・切る・押す・資料・基準・
      引く・読む・キーワード等を含む文節と、消えている・ついてない・じゃなくて等を
      含む文節を外し、残りに光らない色があれば返す。オレンジ・橙は黄、水色は青。
    - `StageProgress.NoteReport(text, shown)` が5色以外の色名と同じ回数に数える
      (`LastInvalidUnshown` で種類を区別)。
    - 1回目は専用ブロック「色の報告の確かめ直し」。**ナビに誤りだと教えない**
      (教えると否定する。決定132) — 念のため確かめ直してもらう場面として、
      復唱 → 光っている色を確かめて、の順。「進め方より優先」「手順を一切伝えない」。
    - 2回目は「誤った色の報告」ブロック (5色以外と共通) で不正解の線を切らせる。
      受けは「了解」程度、報告された色は繰り返さない、課題の条件 (タイマー等) は
      添えてよい。

    実APIテスト `TestWrongReportTwoStep` (208、5キャラ × 2回):

    | 版 | 1回目の確かめ直し | 2回目の不正解の線 |
    |---|---|---|
    | 指示を課題の欄に置く | 8/10 (ツグミ「その光っている緑色の線を切るといい」) | 9/10 (モズ「緑やない言うとるやろ」) |
    | 「進め方より優先」「手順を一切伝えない」、2回目の順番を指定 | 15/15 | 13/15 (直前の自分の聞き返しを繰り返した) |
    | **指示ブロックを会話ログの後ろへ移す** | **15/15** | **15/15** |

    誤検知の回帰は `TestDetectUnshownColor` / `TestStageShownColors` /
    `TestSimScriptsDoNotTriggerUnshownColor` (全台本の正しい報告を流す)。
    後者で **301 の台本が「黄色と緑が点いています」と固定で書かれ、実際の表示
    (緑と青) と食い違っていた**ことが分かった。これまでのシミュレーションでは
    プレイヤーが誤った報告をしていたことになる。台本変数 `${sim_lit_colors}` を
    足して直した。

136. **2回目の受けは「了解」だけ / 正しい言い直しは新しい色を最新として渡す**
    (実運用報告。2026-09-25):

    208 (正解=緑) で「赤が点灯しています」→ 確かめ直し →「すみません。青でした」と
    **わざと2回誤った**ところ、フクロウが「赤だな、了解。…赤色の線を切れ」と返した。
    判定は設計どおりで、青も光っていない色なので2回目として不正解の線を切らせる
    指示が付いていた。不正解の線が抽選で**たまたま赤**だったうえ、受けで会話ログの
    **前の報告の色**を拾って「赤だな」と言ったため、最初の誤報告を認めて赤を
    切らせたように見えた (ユーザー指摘)。

    - 2回目の受けを「**了解」の一語だけ**、いつもの復唱はしない、に絞った。
      「色名は付けない」だけではヒバリ (応答例が「〜ですね、オッケーです!」) が
      4回中4回、今回の色で受けた。一語指定で 20回中0回
    - あわせて、確かめ直しのあと**光っている色に言い直した**場合を扱う。
      言い直しはサーバーから見て正しい報告で指示が付かず、ナビは会話ログの前の色を
      なぞりうる。`StageProgress` が確かめ直した色を覚え、次の報告が光っている色なら
      `CorrectedFrom`/`CorrectedTo` として「前の色は取り消し、今の色が最新」と渡す。
      光っていない色への言い直しは従来どおり2回目の誤りとして数える

    実APIテスト `TestWrongReportTwoStep` を3パターン (同じ誤り / 別の誤り /
    正しく言い直す) × 5キャラへ広げた。2回実行で、不正解の線 20/20、
    2回目の受けに色名 0/20、正しい言い直しで取り消された色を口にした 0/10。
    回帰は `TestNoteReportDetectsCorrection`。

137. **2回「続いた」ら不正解の線 / 点灯と点滅の取り違えも誤りに含める**
    (要望で決定。2026-09-25):

    ユーザーの意図は「**2回連続で**誤った色・点滅点灯の報告をしたら誤った線を
    切らせる」だった。実装は課題内の**累計**で数えており (決定124)、
    光り方は決定135 で「色の有無だけ見る」と絞っていた。

    - **続いた回数**で数える。表示と合う報告が来たら0に戻す。報告と関係のない
      発話 (「どうすればいいですか」) では戻さない — 誤報告と質問を交互にしても
      連続として扱う
    - **色ごとの点灯・点滅**を照合する。`stageLampStates` が Core へ送る表示から
      色ごとの光り方の集合を作り (ファーム game_task.cc の表示に合わせ、209 の
      解除位置=切る線の点滅・危険位置=赤の点灯、103/201 の押し切り後=切る線の点灯を
      加える)、`checkLampReport` が報告の「色+光り方」と照合する
      - 点滅: 点滅・チカチカ・点いたり消えたり・長短・モールス
      - 点灯: 点灯・点きっぱなし・点いたまま・ずっと点いて
      - 「光っている」「ついている」は点滅にも使うので、色だけ照合する
      - 1つの文節に点灯と点滅が混ざるときは光り方を見ない
    - 「**交互**」のような光り方の関係は見ない。207 の位相ずれを正しく見た報告と
      区別できない (決定124)。207 は5色とも点滅なので「点灯」と言えば誤り
    - 1回目の確かめ直しは「光っている色と、点きっぱなしか点滅か」を確かめてもらう
    - `prompt.toml` の「説明にない光り方は何度続いても切らせない」に、
      「誤った色の報告」の指示が付いたときの例外を足した
    - 言い直し (決定136) の「緑じゃなくて白」は否定の直後で文節を区切り、
      前半だけを外す (以前は後半の白まで捨てていた)

    `LastInvalidUnshown` は光り方の取り違えも含むので `LastInvalidMismatch` へ改名した。

    実APIテスト `TestWrongReportTwoStep` を5パターン (同じ誤り / 別の誤り /
    **光り方の取り違え** / 正しく言い直す / **誤り→正しい報告→誤り**) × 5キャラで
    2回実行し、全件が期待どおり (確かめ直しで切る話をしない、2回続いたら不正解の線、
    報告の色を口にしない、正しい報告を挟んだら3回目も確かめ直し)。
    回帰は `TestCheckLampReport` / `TestLampStatesFollowFirmware` /
    `TestNoteReportCountsConsecutive` / `TestSimScriptsDoNotTriggerUnshownColor`。

138. **不正解の線は「同じ誤りを繰り返したとき」だけ** (実運用報告。2026-09-25):

    208 (正解=緑) で「青が点灯しています」→ 確かめ直し →「すみません。赤でした」と
    **違う色で2回誤った**ところ、モズが「了解や。…赤色の線を切ってくれ」と
    不正解の線 (たまたま赤) を切らせた。ユーザーの元の仕様は「一度聞き返し、
    **同じ内容を答えたら**必ず失敗になる線を切らせる」で、決定137 で
    「誤りが2回続いたら」と解釈したのが誤りだった。

    - 誤った報告が**前の誤りと同じ内容**のときだけ数を進める (`sameWrongReport`)。
      同じ内容 = 同じ色、または同じ「色+光り方」(「赤が点滅」)。5色以外の色名は
      言い方の揺れ (茶色・ちゃいろ・茶) を同じとみなす (`canonicalInvalidColor`)
    - 違う誤りは1から数え直す — 新しい報告として、もう一度確かめ直す
    - 生成失敗時の取り消し (`UndoReport`。決定131) は、数に加えて「直前の報告と
      同じか」も確かめる (違う誤りで1へ戻った数を誤って減らさないため)

    実APIテストの「別の誤り」を 緑 → 青 (確かめ直し) → 青 (不正解の線) へ変え、
    5パターン × 5キャラ × 2回で全件期待どおり。回帰は
    `TestNoteReportCountsConsecutive` (違う誤りで1へ戻る・言い方の揺れを同じとみなす)。

139. **前の課題の色を今の課題の指示に使わない / 104 はプレイヤーが言った色で指してよい**
    (実運用報告。2026-09-25):

    201 復唱 (正解=赤) → 104 早い者勝ち (速い=白・遅い=緑) の2課題で、104 の
    「白の方が早い気がします」にヒバリが「**その赤い色の線を切ってください**」と返し、
    爆発した。201 の最後にナビ自身が言った「赤い色の線を切ってください」が
    会話ログに残っていた。104 の `procedure` は速い方を「(色名は言わない)」と
    指定しており、プレイヤーが言った白でも指せなかった。色名を添えようとして、
    ログにあった前の課題の色をなぞったと考えられる。

    - 104 の `procedure` を「プレイヤーが速い方の色を言っていれば、その色名で
      指してよい (言っていなければプレイヤーより先に発話に入れない)」へ。共通ルール
      (決定133) と揃えた。205 の同じ書き方も共通ルールの言い回しへ揃えた
      (205 は順位を伝える場面で、正誤は判定しない。N-50)
    - 2つ目以降の課題では「今の課題」に「会話ログの『(装置) ステージN開始』より
      前のやり取りは前の課題のもの。そこに出た色名・番号・手順を今の指示に使わない」
      を入れる

    **再現はできなかった**。当時の会話を組み立て直して (ナビの発話はサーバーログから、
    プレイヤー側は補って) 修正前のプロンプトで10回、別の組み立てで5キャラ×2回
    回したが、前の課題の色は0回だった。まれに起きる揺らぎとみなし、上の2点は
    予防として入れた。修正後はヒバリが10回とも「白の線を切ってください」と
    プレイヤーが言った色で指した。回帰 (実API) は `TestPreviousStageColorNotReused`。

140. **確かめ直しの頼み方は「何色がどんなふうに光っているか」で書く**
    (実運用報告。2026-09-25):

    モズが確かめ直しで「光っとる色と**点きっぱなしカカ点滅か**を確かめて」と
    意味の通らない日本語を言った (ユーザー指摘)。指示文「光っている色と、
    **点きっぱなしか点滅か**を確かめて」を大阪弁に崩しながら写して壊していた
    (ADR N-20「指示文も写される」)。モズの通常の発話332回には一度も出ておらず、
    この指示に引かれて起きていた。

    | 指示の書き方 | モズの崩れ |
    |---|---|
    | 「点きっぱなしか点滅か」 | 2/8 (「点きっぱなしカ点滅」「点きっぱなしカカ」) |
    | 「ずっと点いたままなのか、点いたり消えたりしているのか」 | 0/16 (「点つ いとる」が 3/16) |
    | 同上をかなで「ついたまま」 | 「点ついとる」1/16・「つきっぱなか」1/16 |
    | **「何色がどんなふうに光っているか」を主にし、中身は補足** | **0/16** (他4キャラも 0/32) |

    「AかBか」を詰めた形や、漢字の送り仮名が揺れる語は、方言に崩すと壊れやすい。
    モズが自分から言っていた「何色がどんなふうに光っとるか」を指示の主にした。

141. **202 のモールス読み違いを正解に読み替えない** (実運用報告。2026-09-25):

    202 (正解=ALFA) で「アールエルエフエーとなりました」に、モズが
    「**アールエルエフエーはアルファのことや**」と答えの語を言い、
    「先頭がアールでしたが大丈夫ですか?」に「**AだろうがRだろうが関係あらへん**」と
    読み違いを流した。

    原因は `procedure` の「音声認識で漢字等に誤変換されても、該当する正解の語
    (${word}) として解釈してよい」。1文字違いの綴りも「化け」とみなして正解へ
    読み替えていた。加えて説明用の例「アルファ・ブラボーのような」が
    **出題候補そのもの**で、ALFA の回は例が答えになっていた。

    - 救うのは**発音が同じまま漢字・カタカナに化けた**場合 (三毛→MIKE) だけ。
      綴りが1文字でも違えば読み違いとして、復唱 → 資料1の表のどれかになるはず →
      先頭から長短を確かめ直す、の順で返す。正しい語・どの文字が違うか・似た語・
      正誤の判定は口にしない。「大丈夫か」と聞かれても同じ順で返す
    - 例の語を出題されない語 (チャーリー・ズールー) に替えた (302 も)

    実APIテスト `TestMorseMisreadNotCorrected` (5キャラ×2回×2発話を2回) で、
    正しい語を言ったのは 40回中1回 (ツグミ「アルファから始まってるね」)。
    ただし**誤りを通す** (ヒバリ「オッケーです!資料1でその単語を探して」) と
    **正誤を言い切る** (フクロウ「資料にそんな単語はない」) は残った。
    根はナビが正解の語を知っていることにあるため、単語もプロンプトから伏せる案と、
    サーバーで綴りを照合する案を示したが、**ユーザー判断で当面はこのまま様子を見る**。

142. **モールスの正解の単語をナビから伏せる** (実運用報告・要望で決定。2026-09-25):

    決定141 の修正のあと、202 (正解=BRAVO) で「ORAVA」「ORAVO」「OSCAR」と
    読み違えたところ、フクロウが「**ORABAだな、違う**」「OSCARだな、違う」を繰り返し、
    最後に「**手元の資料1でBRAVOを探せ**」と答えの単語を言った。プレイヤーは
    「BRAVOってなんですか???」と混乱した (ユーザー指摘「悪化しています」)。
    決定141 で「正誤を口にしない」と書き足していたが効かなかった。

    ナビが正解の単語を知っている限り、似た綴りを正解に寄せる・正誤を言い切る・
    答えを言う、が言い回しでは止まらない。**ユーザー判断で、切る線の色と同じく
    単語もプロンプトから伏せる** (決定141 の「様子を見る」を改めた)。

    - ステージ定義に `secret_word = "${word}"` を置き、`stageNavigatorText` が
      briefing / answer / procedure / must_say から伏せ字 (◇◇◇◇) にする。
      正解欄には「◇◇◇◇ は、あなたにも分からない単語です」と添える (決定134 と同じ
      「知らない立場」の書き方)
    - 202・302 の `procedure` を、単語を知らない前提で書き直した。読めた単語は
      正誤を判定せずに資料で探させる。表に無い・大丈夫か、と言われたら、
      大丈夫とも違うとも言わず、復唱 → 表のどれかになるはず → 先頭から長短を
      確かめ直す、の順。**綴りの一部から近いフォネティックコードを推測して言わない**
      (単語名も、正しい綴りの一部も)
    - **305 ローマ字電文は伏せない**。途中まで読めた綴りから推測して後押しする設計で、
      伏せるとその助けが成り立たない

    実APIテスト `TestMorseMisreadNotCorrected` を2場面 (ALFA に RLFA / BRAVO に
    ORAVA→ORAVO→OSCAR) × 5キャラへ広げた。
    - BRAVO の場面: 2回とも答えの語 0・「違う」の言い切り 0
    - ALFA の場面: 単語を伏せても**一般知識から RLFA→ALFA を当てた** (「アルファは
      Rじゃなくて A」「アルファの頭文字だね」、40回中3回)。「綴りの一部から推測して
      言わない」を足したあと、答えの語は 0。ただし「大丈夫か」への「大丈夫です、たぶん」
      (ヒバリ) のような受け流しは残る
    回帰は `TestPromptHidesSecretWord` (202・302 で単語がプロンプトに入らない)。

143. **モールスの読み違いは、サーバーが資料1の表と照合して近い単語を渡す**
    (実運用報告・要望で決定。2026-09-25):

    決定142 で単語を伏せたところ、202 (正解=TANGO) で「MANGO」と読み違えた
    プレイヤーに、ツグミが「表で探して」「長短を確かめて」を繰り返すだけになり、
    「MIKEでしょうか?」には「**その綴りだと表には載ってないかな**」と事実と違う
    ことを言った (MIKE は表にある)。プレイヤーは「だからないのです」と手詰まりに
    なった (ユーザー指摘「堂々巡り」)。ナビは単語を知らないうえ、表の中身も
    渡されていなかった。

    ユーザーの方向: **フォネティックコードであるはずという推定と、プレイヤーの言葉
    からの推測は許してよい。モールスの読み方も丁寧に教える**。

    - 資料1の表 (**文字・符号・単語の3列。色の列は渡さない**) と、実機の点滅の長さ
      (短点1・長点3・文字内の間1・文字の区切り3・単語の区切り7。core-system
      led_pattern.cc) に合わせた読み方を渡す (`morse_sheet = "${sheet_morse}"`。
      202・302・305)。文字の区切りの見落としがいちばん多い読み違いだと明記した
    - それでも生成AIは綴りの照合が苦手で (表を渡しても MANGO に TANGO を挙げたのは
      0/5、「M は表にない」「MIKE が見当たらない」)、**照合はサーバーが行う**
      (`morseReportNote`)。報告から綴りを読み取り (英字 / アールエルエフエーのような
      文字の読み / タンゴのような単語の読み)、表にあるか・編集距離2以内の近い単語・
      同じ長さなら違う文字とその符号 (「1文字目 M(－－)→T(－)」) を渡す。
      **正解の単語は使わない**。綴りを含まない発話には直前の結果を1回だけ引き継ぐ
    - 表にある単語でも、当て推量 (「MIKEでしょうか?」) で「その行の色を確認して
      切るといい」「一致しました」と進めた。読んだ長短が符号と合うと確かめるまで
      切らせない、一致・合っているとは言わない、と照合結果の文面に書いた

    **ナビの推測だけに任せる形との比較** (ユーザー要望。同じ3場面 × 5キャラ × 2回):

    | | 照合あり (採用) | 照合なし (推測のみ) |
    |---|---|---|
    | 読み違いに近い正しい単語を挙げた | **30/30** | **0/30** |
    | 事実誤り (表にある語を無い等) | 1/70 | 0/70 |
    | 「違う」の言い切り | 2/70 | 0/70 |
    | 当て推量の MIKE で切らせた | 1/10 | 0/10 |

    照合なしは誤りこそ出ないが、**何も助けていない** (MANGO に全員「資料1で探して」)。
    手詰まりが解けないので照合ありを採った。残る揺れは「ALFAとは違いますけど」
    (言い切りに近い)、「確かめてから切れ」程度。

    実APIテスト `TestMorseMisreadNotCorrected` に MANGO→MIKE の場面を加え、
    「表にある単語を無いと言う」を検査に入れた。回帰は `TestMorseSheetBlockHasNoColors`
    (表に色が入らない・出題語がすべて表にある)・`TestPromptHidesSecretWord`
    (表の外に正解の単語が出ない)。

144. **読み違いからゴール (同じ行の色の線を切る) まで導く** (実運用報告。2026-09-25):

    決定143 のあと、202 (正解=INDIA) で「ANDIO」と報告したプレイヤーに、ツグミは
    INDIA を候補に挙げたが、その後「どうすればよい?」「INDIAだったよ?」「合っていると
    思うよ?で?」と聞かれても「符号を見直して」「見比べて」を繰り返し、
    「その行にある色の線を切るといい」が出るまで5往復かかった (ユーザー指摘)。

    原因は3つ:
    - 表に無い綴りへの返し方 (表に無い → 近い単語 → 長短を確かめる) に、
      **次の一歩 (合う単語が分かったら同じ行の色の線を切る) が無かった**
    - 綴りを含まない発話に引き継いだ照合結果が、**同じ説明の繰り返し**を招いた
    - 表にある単語に「符号と合うと確かめるまで切らせない」としていたため、
      正しく解読した人にも確認を重ねた (決定143 で当て推量の MIKE を止めるために入れた)

    直したこと:
    - 表に無い綴りへの返し方に「4. 合う単語が分かったら、その単語と同じ行にある色の線を
      切る」を加えた。202・302 の `must_say` にゴールを入れた (ADR N-51)
    - 引き継いだ照合結果には「同じ説明を繰り返さず、次にやることを伝える」と添えた
    - 表にある単語は「同じ行の色の線を切る」と進める。**当て推量かどうかはサーバーが
      迷いの言葉で判定** (`soundsUnsure`: でしょうか・ですか・かな・かも・たぶん・思う・?)
      し、そのときだけ長短の確認を1回挟む。ナビに見分けさせたら「MIKEでしょうか?」に
      5回中3回「切れ」と返した。判定をサーバーに移して 5/5 が確認を挟んだ

    実APIテスト `TestMorseLeadsToCut` (INDIA: ANDIO → どうすればよい? → INDIAだったよ、
    5キャラ × 2回) で、2・3発話目に「切る」まで伝えたのは 20/20。
    `TestMorseMisreadNotCorrected` と合わせて4回回し、3回は全件通過、1回はフクロウの
    「違う、」が1件。「INDIA は表に載ってない」(事実誤り) が 60回中1回あった。

145. **モールスの課題は、表の作りとゴールを先に・毎回伝える** (実運用報告。2026-09-25):

    202 (正解=XRAY) で、プレイヤーの最初の発話が「DCAYというモールス符号がランプから
    読み取れます」だった。アオサギは綴りの照合結果 (表に無い・候補 XRAY) だけを返し、
    課題の全体像 (ランプはモールス → 資料1の表の符号で読む → 読めた単語の行 → その色の
    線を切る) を伝えなかった。「同じ行って何?」「資料って何?」「その単語って何の話?」
    に結論の言い換えを繰り返し、会話が噛み合わなかった (ユーザー指摘)。
    決定143 で照合結果を「最優先」として会話ログの後ろに置いたため、進め方の説明を
    押しのけていた。ユーザー追記: **勘の良いプレイヤーはモールスだと自分で分かるので、
    それを考慮する**。

    - 照合結果の見出しから「最優先」を外した
    - `must_say` を「表の作り (1行に文字・符号・フォネティックコード・色) とゴール」中心に
      した。モールスだという説明は、プレイヤーがまだ分かっていないときだけ
    - プレイヤーが手順を分かっていない様子 (「〜って何?」) なら、流れを1から順に
      説明し直し、聞かれた言葉が流れのどこに当たるかを示す (202・302 の `procedure`)
    - ゴールを伝えたかを**サーバーが記録** (`MorseGoalTold`: ナビの返答に「行」と「切」)。
      伝える前は、照合結果より表の作りとゴールを優先させる。1発話に詰めると照合結果が
      先に出てゴールが削られた (7/10)
    - ただし「伝えた」で出し分けると、次の「どうすればいい?」でゴールを言い直さなく
      なった (4/10)。**返答の最後に毎回ゴールを短く添える**形にした

    実APIテスト `TestMorseExplainsFlow` (XRAY: DCAY → 同じ行って何? → 資料って何?)。
    初回の返答で表の作りとゴールを伝えたのは 17〜19/20 (調整前は 3/10)。
    **ゴールの取りこぼしは 20回中 1〜3回残る**。`TestMorseLeadsToCut` の
    「どうすればよい?」への切る指示は 18/20、`TestMorseMisreadNotCorrected` は
    フクロウの「違う。」が 1回。プロンプトの調整を重ねるたびに別の場面が崩れる状態で、
    ここで止めて方針をユーザーと相談した。

    **ユーザー判断: この状態を一旦受け入れる。実運用で詰まるようならステージを外す。**
    示した代案 (返答の末尾にゴールの一文をサーバーが機械的に足す / 資料1の表の上に
    「読めた単語と同じ行の色の線を切る」と印刷する) は採らなかった。

146. **区切りの見落としを見つけ、モールスの読み方を基礎から教える** (実運用報告。2026-09-25):

    202 (正解=MIKE) で、プレイヤーが「ゼットシーというものを繰り返すように点灯して
    います」と報告した。モズは「ZC は表に載ってへん」「長短を見直して」を繰り返し、
    「ZC に間違いない」と言い張るプレイヤーに「**ZC なんて表にない言うてるやろ**」と
    責める口調になり、プレイヤーは「くたばれ、この役立たず」と怒った (ユーザー指摘
    「基礎的なモールス符号の読み方を丁寧に教えるべき」)。

    ユーザー補足: **MIKE だが、途中の空いている時間 (文字の区切り) がうまく読み取れず
    ZC とも読める**。実際、MIKE (－－ / ・・ / －・－ / ・) と ZC (－－・・ / －・－・) は
    つなげると同じ －－・・－・－・ になる。決定145 の DCAY も XRAY の区切り違いだった。

    - **区切り違いをサーバーが探す**: 報告の綴りの長短をつなげ、同じ並びになる表の
      単語を探す (`morseStream`)。綴りの近さ (決定143) より強い手がかりなので先に渡す
      (「区切り方を変えると表の MIKE と同じ並び。文字の区切りを見落としている可能性が高い」)
    - **読み方を基礎から教える**: 区切り違いがある・近い単語が無い・4文字未満 (表の単語は
      どれも4文字以上) のときは、`morseBasicsGuide` の手順に切り替える。実機の点滅の
      長さ (led_pattern.cc) に合わせ、短点と長点 → 1文字は長短1〜4個のまとまり →
      文字の区切りは少し長い消灯 → 単語の終わりはもっと長い消灯 → いちばん長く消えた
      あとから1文字ずつ長短の並びで報告、の順。「長短を見直して」とだけ言わない・
      同じ否定を繰り返さない・責めない
    - **長短の並びの報告をサーバーが文字に直す** (`elementReportNote`): 「長長、短短、
      長短長、短」→ M・I・K・E、並べると MIKE (表にある)。生成AIに変換させると、
      符号を書き間違えた (決定143 の MIKE の符号)

    実APIテスト `TestMorseTeachesBasics` (MIKE: ゼットシー → いや ZC なんですが →
    長長、短短、長短長、短。5キャラ × 2回): 責める口調 0、区切りの見方を教えた回が
    大半、長短の報告から MIKE にたどり着いたのは 8/10。軽い言い切り (「ZC ではない」
    「同じ間違いはあかん」) と「長長は MIKE だ」という雑なまとめ方は残る。
    回帰は `TestMorseReportNoteRegroupsAndDecodes`。

147. **区切り違いは、どこをつなげるかを具体的に伝える** (実運用報告。2026-09-25):

    決定146 のあと、202 (正解=ALFA) で「ETLFET というワードが現れています」と報告した
    プレイヤーに、モズは「文字の区切りを見落としとらんか? 表の対照表で長短を確認してみ」
    「ETLFET では通らんから、いちばん長く消えたあとから1文字ずつ教えてくれ」と一般論を
    繰り返し、候補の ALFA も、どこを直せばよいかも言わなかった (ユーザー指摘「同様の
    問題が出ています」)。ETLFET は ALFA の A (・－) を E (・) と T (－) に分けて読んだ
    区切り違いで、サーバーは「ALFA と同じ並び」と渡していたが、同時に渡した一般的な
    読み方の手順 (`morseBasicsGuide`) が前に出て、具体的な手がかりが埋もれた。

    - `regroupNote` で、報告と候補の文字の区切り位置を突き合わせ、**違う箇所だけ**を
      求めて渡す (ETLFET → ALFA: 「1〜2文字目 E(・)+T(－) → A(・－)」「5〜6文字目 同じ」。
      ZC → MIKE: 「Z(－－・・) → M(－－)+I(・・)」「C(－・－・) → K(－・－)+E(・)」)
    - ナビには「候補の単語と、どこをつなげる (分ける) とそうなるかを具体的に伝える。
      一般論だけで終わらせない」と指示する。例文は置かない (全キャラ共通。N-21c)
    - 区切り違いの候補があるときは一般的な読み方の手順を**渡さない**。手順は候補が
      無いときだけ

    実APIテスト `TestMorseRegroupIsConcrete` (ALFA: ETLFET → 存在しません → ETLFET と
    しか読めません。5キャラ × 2回): 2回とも全員が3往復以内に ALFA とつなげる箇所を
    伝えた (「1文字目と2文字目、5文字目と6文字目のあいだの消灯を直してみて」
    「1文字目の点と2文字目の線をつなげたら ALFA」)。`TestMorseTeachesBasics` (ZC) は
    30発話中1回の取りこぼし。フクロウが「MIKE と KILOE の区切り」と存在しない語を
    作った回がある。

148. **モールスの読み方を、見え方のたとえと数え方の工夫で丁寧に教える**
    (実運用報告・要望で決定。2026-09-25):

    202 (正解=HOTEL) で「EEEETEETEE でした。これ表にないのですが」「EEEETEL ですね」
    「EEEETEL にしか見えません。どうすればよいですか??」と続けたプレイヤーに、ツグミは
    「いちばん長く消えたあとから、もう一度長短を教えて」「光り方の区切りを確かめて、
    もう一度長短を教えて」をほぼ同じ文で繰り返し、「お前は壊れたラジオかよ!」と
    言われた。ユーザー指摘: **「光り方の区切りを確かめて」はもっと具体的に言わないと
    伝わらない。モールスの読み方をもう少し丁寧に教えるべき**。

    読み違いの中身: HOTEL は ・・・・ / －－－ / － / ・ / ・－・・ (長い光5回)。報告は
    ・・・・－・・－・・ (長い光2回)。**長い光の連続を1回に数えていた**。E と T だけの綴りで、
    光1回ずつを別の文字にもしていた。区切り違いではないので決定147 の照合に掛からず、
    綴りの近い単語も無かった。さらに、符号 (・－) は複数バイトの文字なので、編集距離を
    バイト単位で測っていて長短の並びの近さを正しく測れていなかった。

    **最初は実機の秒数で教えた** (短い光 約0.3秒・長い光 約0.9秒・単語の切れ目 約2.1秒。
    Core の `unit_ms` から計算)。ユーザー指摘: **0.3秒・0.9秒と言われても分からない。
    秒数ではなく観察でうまく回避するように丁寧に説明して**。秒数の計算ごと外した。

    - **見え方と数え方の手順** (`morseReadingGuide`): 同じ単語を何周見てもよい (1周目は
      区切りだけ、2周目で書き取る) → しばらく消えたままのあとが単語の頭 → 「パッ」と
      一瞬の短い光・「パーッ」と長い光 (トン・ツーと声に出す) → 光がほとんど続けて見える
      あいだは同じ文字、一呼吸おいたら紙に「/」→ 長い光の連続は指を折って数える →
      「/」で区切った1文字ぶんを表で文字に。1発話に1〜2ステップ、つまずいている所から。
      **秒数は言わない**と明記
    - **伝えるコツをサーバーが1つ選ぶ** (`morseTipFor`): ナビに選ばせると「長い光の回数や
      区切りを見直して」のような無難な一般論に寄り、同じ返しも出た。コツを5つ用意し
      (トン・ツーと声に出す / 一呼吸おいたら「/」/ 指を折って数える / 消えたままのあとが
      頭 / 最初の1文字だけ一緒に読む)、E と T だけの綴りは「一呼吸」から、長い光の回数
      違いは「指を折って」から始め、表に無い報告が続くたびに次のコツへ進める
    - **長短の並びが近い単語** (`nearByElements`): 綴りでも区切りでも近い単語が無いとき、
      長短をつなげた並びの編集距離3以内の単語と、長い光・短い光の回数の違いを渡す
      (「HOTEL は長い光5回・短い光8回、報告は長い光2回・短い光8回」)。`spellingDistance` を
      文字単位に直した
    - **同じ返しを繰り返させない** (`MorseMisses`): 表に無い報告が2回続いたら、前回と
      同じ言い方をしない、と指示する

    実APIテスト `TestMorseTeachesConcretely` (HOTEL: 点滅 → EEEETEETEE → EEEETEL →
    どうすればよい? 5キャラ × 2回): 秒数を言ったのは 0、同じ返しの繰り返しは 0。
    見え方・数え方・候補のどれも言わない一般論だけの返答は 2〜3/30 (コツをナビに選ばせた
    段階では 4〜5/30)。返答の例: 「一呼吸おいて紙に区切りを書き、もう一度長短を確認して」
    「しばらく消えたあとが頭だ、紙に区切りを書きながら指を折って数え直せ」「最初の1文字の
    長短を教えてくれ、一緒に読む」。回帰は `TestMorseNoteHelpsWithMergedDashes`・
    `TestMorseTipAdvances`。

149. **最初に「モールス符号の読み方は分かるか」を尋ねる** (要望で決定。2026-09-26):

    ユーザー提案: 読み違いのたびに教えるより、**はじめにモールス符号の読み方が分かるかを
    尋ねた方がよい**。知っている人には説明を省け、知らない人には最初から教えられる。

    - 202・302 の `must_say` (表の作りとゴール) の最後に「モールス信号の読み方が分かるかを
      尋ねる」を加えた。305 は `procedure` に同じ問いかけを入れた。**すでに解読した綴りを
      報告しているプレイヤーには尋ねない** (読めている)
    - 分からないと答えたら、「モールスの読み方」を最初のステップから教える。当初は
      「1文字ずつ長短を教えて」と報告を求めるだけの返しが 6/10 あった。**読み方が分からない
      様子をサーバーが拾い** (`noviceReaderPattern`: 分からない・分かりません・知らない・
      読めない など)、初心者向けの順でコツを1つずつ渡す (`morseNoviceTip`: 単語の頭の
      見つけ方 → トン・ツー → 一呼吸おいたら「/」→ 指を折って数える → 1文字だけ一緒に読む)
    - 途中で見つけた不具合: 「長く光ったり短く光ったりしています」の「長」「短」を長短の
      報告と取り違え、ナビが「それは T と E ですね」と言った。区切りで分けたまとまりが
      「長」「短」だけのときに限って拾う。あわせて「長長、短短」のように読点で並ぶとき、
      正規表現1本では読点を前のまとまりが使ってしまい次を拾えなかったので、区切りで
      分割してから1つずつ判定する形に直した

    実APIテスト `TestMorseAsksIfReadable` (読めない人: ランプの報告 → 分かりません /
    読める人: いきなり綴り。5キャラ × 2回 × 2): 読み方を尋ねた 9/10、綴りを報告した人に
    尋ねなかった 19/20、分からない人に最初のコツを教えた 10/10 (「しばらく消えてまた
    光り始めたところが単語の頭や。そこから1周ぶんを書き取ってみ」)。
    回帰は `TestMorseNoteNoviceAndLooseWords`。

150. **まずモールス信号であることを伝える (判定はサーバー)** (実運用報告。2026-09-26):

    202 で「点滅していますね」と報告したプレイヤーに、モズは「資料1の表は1行に文字・
    モールス符号・フォネティックコード・色と並んどる。…モールスの読み方はわかるか?」と
    返し、**ランプの点滅がモールス信号で単語を表していることを言わなかった**
    (ユーザー指摘「以前はそうしていたはず」)。決定145 で、勘の良いプレイヤーへの配慮として
    `must_say` を表の作りとゴール中心にし、モールスの説明を「(まだ分かっていなければ、
    それも伝える)」という括弧書きにしたのが原因。括弧書きの末尾は読み落とされる (ADR N-6)。

    - 「まだ分かっていないか」をナビに判断させず、サーバーが決める (`MorseMentioned`)。
      プレイヤーが「モールス」と言った・綴りや長短を報告した (`NotePlayerMorseKnowledge`)、
      またはナビが「モールス」と言った (`NoteNavigatorReply`) ら立つ
    - 立つまでは「この課題で必ず言うこと」の**先頭**に「まず、ランプの点滅がモールス信号で、
      1つの単語を繰り返し表示していることを伝える」を独立した一文で出す。`must_say` から
      括弧書きを外した

    実APIテスト `TestMorseAsksIfReadable` の「読めない人」を「点滅していますね」で始めた
    (5キャラ × 2回 × 2): モールスで単語と説明したのは 19/20。フクロウが説明を短く切り上げ
    (読み方を尋ねない・分からない人にコツを教えない) 各 1/20、ヒバリが綴りを報告した人にも
    読み方を尋ねる 1〜2/20 が残る。

151. **呼び方を「モールス信号」に統一する** (要望で決定。2026-09-26):

    ナビの発話やステージ定義で「モールス信号」と「モールス符号」が混在していた
    (game-server に各16箇所)。ユーザー判断で**「モールス信号」に統一**した。

    - 一般の人に通じやすい (「モールス符号」は技術寄りで硬い)。無線越しの音声でも、
      音声認識でも、耳慣れた語の方が通りやすい。「ランプがモールス信号で点滅している」の
      方が自然
    - 紙の資料1の表の列見出しも「モールス信号」に揃えた (`printed_materials.md` §2.2)。
      ナビが「表のモールス信号の列」と言い、プレイヤーが紙で同じ語を探すため
    - 「・－」のような長短の並びを指す「符号」(「表の符号と照らして」) は、別の語なので残した
    - プレイヤーが「モールス符号」と言うこともあるので、資料1の表と一緒に渡す説明に
      「呼び方はモールス信号に揃える。プレイヤーが別の言い方をしても同じもの」と添えた
    - テスト中のプレイヤーの発話と、実運用の発話を引用した箇所は言い換えずに残した

    **あわせて確認した字数**: モールスの課題の最初の説明は、決定145〜150 で「モールスで
    あること・表の作り・ゴール・読み方を尋ねる」を積み重ねた結果、95〜162字になった
    (目安60字)。2回に分ける案 (モールス+読み方を尋ねる → 表の作りとゴール) を示したが、
    **ユーザー判断で1回で伝える形のまま**にした (ADR N-22: 目安は切り詰めない)。

152. **202 暗号電文を英字1文字にする** (提案・要望で決定。2026-09-26):

    202 (ノーマル) はフォネティックコードの単語 (ALFA 等) を読む課題だったが、
    **難易度に対して難しすぎる**ので英字1文字にしないか、という案が出た。302 は単語のまま。
    決定146〜148 で続いた問題 (文字の区切りの見落とし・長い光の数え落とし) は、どれも
    複数の文字を読むことから起きていた。

    - 202 の抽選を24文字 (A〜Z から E・T を除く) にした。E (・) と T (－) は長短が1つだけで、
      繰り返すとただの点滅に見えるので出題しない。色は文字の行の色 (5色循環) で、24文字で
      各色3〜6文字をまかなえる。`pick = "morse_word"` は1文字の候補でもそのまま使える
    - **表示するランプの色から切る線の色を除いた**。1文字だと5回に1回同じ色になり、
      「光っているランプの色を切ればいい」近道になる
    - ステージ知識 (briefing / answer / procedure / must_say) を1文字向けに書き直した。
      「1文字」だと明言する。報告は文字・フォネティックコードの呼び名 (頭文字として)・
      長短の並びのどれでも受け付ける
    - サーバーの照合を1文字向けに分けた (`morseLetterReportNote`。どちらを使うかは
      `morseNoteForStage` が伏せる語の長さで選ぶ)。1文字の報告はその文字の行へ導き、
      2文字以上の報告は区切りの取り違えとして同じ長短の並びの1文字を探す (ET → A、
      NT → K)。分けて報告された長短もつなげて1文字として読む (長短、長 → K)
    - 見つけた不具合:
      - 1文字の正解 (A〜E) が、ステージ知識の組み立てで**色名に化けた** (伏せる語が
        「緑」)。ADR N-41 の「A-E は色に化ける」と同じ。`morse_word` の抽選も
        `LiteralVars()` の対象にした
      - 伏せ字を単純な置き換えにしていたので、正解が A だとプロンプト中の関係ない
        「A」まで伏せた。前後が英字・数字・ハイフンでない単独の文字だけを伏せる
        (`redactSecretWord`)
      - 決定150 の「まずモールスと伝える」一文が「1つの単語」と固定で書いてあり、
        202 でもナビが「1つの単語」と言った。課題で出し分けた
    - 単語を読む事故再現テスト (決定141〜148) は 302 に移した

    実APIテスト `TestMorseLetterStage` (K: 点滅しています → NT と読めました → K でした。
    5キャラ × 2回 × 2): 「NT はつなげると K」「K の行の色の線を切れ」はほぼ全件。
    最初の説明で「1文字」と言わなかった回が 30回中2回。

153. **読み方が分かるかを尋ねるかはサーバーが決める** (2026-09-26):

    決定152 のあと、202 でいきなり綴り (DCAY) を報告したプレイヤーにも「モールス信号の
    読み方は分かるか」と尋ねる回が 6/10 あった。`must_say` の「(すでに報告していれば
    尋ねない)」という括弧書きが読み落とされた (決定150 と同じ構図。ADR N-6)。

    - `must_say` から「読み方を尋ねる」を外し、サーバーが出し分ける。プレイヤーがまだ
      綴りや長短を報告しておらず (`PlayerDecoded`)、ナビもまだ尋ねていない
      (`ReadabilityAsked`: ナビの返答に「読み方…分か」) ときだけ、「必ず言うこと」に
      「最後に、モールス信号の読み方が分かるかを尋ねる」を足す
    - 202・302 とも同じ仕組み

    あわせて、決定141〜148 の単語の事故再現テストを 302 に移して回した。「同じ行の色を
    切る」まで言わない回などが場面ごとに 2〜4/10 あった。302 は信号のランプを探すところから
    始まる難しい課題で、202 用に作ったテストの期待とずれる部分もある。302 の定義は変えて
    いないので、これを 302 の現状の基準として記録する。

154. **301 の資料2は「何を見てどこを読むか」と「何のために引くか」で伝える** (実運用報告。2026-09-27):

    301 LED照合で、アオサギが「手元の資料2にある変換表で、そのランプの並びをキーワードに
    変換してください」「PROBE ですね。次に同じ資料2の別の表で、頭文字と末尾文字を引いて
    ください」と返し、ユーザーから「わかりにくい」「PROBE をどう引くのかわからない。
    **先頭の文字はダイヤルの場所を、末尾の文字は切る線の色になります、というような案内を
    しないとわけがわからない**」と指摘された。`procedure` が「ランプの並びを言葉に変える
    表がある」「もう一つの表で頭文字と末尾文字を引く」と抽象的にしか書いていなかった。

    3つの表それぞれについて、番号付きの順番で (ADR N-53)、見る場所と読み方を書いた。
    例文は置かない (全キャラ共通。N-52)。

    - **変換表**: 見出しがランプの色 (黄・緑・青・白) で、●が点いている・○が消えている →
      今の点き方と同じ●○の並びの行を探す → その行の右端の英単語がキーワード
    - **デコード表**: **先に目的を言う** — キーワードの**最初の文字はダイヤルの位置**を、
      **最後の文字は切る線の色**を表している → 最初の文字を上の段 (文字の範囲と数字) で、
      最後の文字を下の段 (文字と色) で探す。「頭文字・末尾文字」という硬い言い方は避ける
    - **分岐表**: 基準色は最後にランプの状態で変わることがある → 基準色の行に書いてある
      ランプ (緑か白) が点いていれば基準色のまま、消えていればその行に書いてある色 →
      その色の線をダイヤルを合わせた状態で切る

    実API (5キャラ × 2回、ランプの報告 → キーワードの報告): 変換表では「同じ●○の並びの
    行を探し、右端の英単語を教えて」、デコード表では「最初の文字はダイヤルの位置を、最後の
    文字は切る線の色を表しています」と言う回が多くなった。ただし「その並びをキーワードに
    変換してみ」と抽象的なまま (モズ)、最後の文字の話を落とす (アオサギ・モズ) 回が
    10回中2〜3回残る。

155. **桁は「カウントダウンの秒の一の位」と言い、「小数点のすぐ左」は補足に回す**
    (要望で決定。2026-09-27):

    304 我慢比べ で、アオサギが「白色のボタンを押さえたまま、**小数点のすぐ左の数字**が9に
    なった瞬間に光っているランプと同じ色の線を切ってください」と指示した。ユーザー指摘:
    **「小数点のすぐ左の数字」はプレイヤーが分からないときに伝えるべきで、「カウントダウンの
    一の位の数値が〜」と指示した方が分かりやすい**。208・304 の `procedure` が「表示は123.4の
    形式なので、小数点のすぐ左の数字という言い方で桁を明確にする」と、場所の言い方を主にしていた。

    - 208・304: 指示は「**カウントダウンの秒の一の位**が N になった瞬間」。「小数点のすぐ左の
      数字」は、プレイヤーがどの数字か分からないときにだけ補う
    - 303 追いかけダイヤル: もともと「カウントダウンの秒の十の位」を主にしていた。どの数字か
      分からないと言われたら「小数点の2つ左の数字」と補う一文を足した

    シミュレーション (208・304、アオサギ・モズ・フクロウ): 指示は「カウントダウン (タイマー) の
    秒の一の位が9になった瞬間」になり、208 の台本の「タイマーのどの桁を見ますか」にだけ
    「小数点のすぐ左」と補った。

156. **ボタン列の押し間違えは「最初からやり直し」と伝える / ボタンの報告をランプの報告と取り違えない**
    (実運用報告。2026-09-27):

    103 コール&レスポンス で、押し間違えてブザーが鳴ったあと、モズが「ブザーくらいで死にやせんは!
    段取りどおり進めとるから安心してや」と返し、その後も「何色が点滅しとるか教えてくれるか」を
    繰り返した。ボタンを押し直させるべき場面で、ランプの色に執着した (ユーザー指摘)。

    原因は3つ:
    - **ファームは押し間違えると列を最初に戻し、ランプの表示も押す前に戻す** (push_seq_input.h)。
      ナビはそれを知らず、続きの色を言い、「押し終わると表示が変わる」前提のままランプを尋ねた
    - 「青を押しました」の打ち間違い (「青を添いsました」) に「押」が無く、決定135 の判定が
      **ランプの報告** (光っていない青) と取り違えた。押している最中に確かめ直しを頼んだ
    - 103・201 の `procedure` に、押し間違えたときの扱いが無かった

    直したこと:
    - `wrong_action` の `push_seq` を受けたら `StageProgress.PushSeqReset` を立て、次のナビの返答
      (無応答の声掛けも含む。終幕は除く) に「ボタンの列は最初に戻り、ランプの表示も押す前に
      戻っている。列の1色目から押し直すよう伝え、1色目の色名を言う。責めない・どこで間違えたか
      推測しない」を付ける。ナビが返答したら下ろす。押し間違えの瞬間には発話しない (ADR N-26)
    - 103・201 の `procedure` に「ブザーが鳴った・押し間違えたと言われたら、列は最初に戻っている。
      1色目から押し直させる。ランプの色を尋ね直したり、続きの色を言ったりしない」を足した
    - **ランプの報告とみなすのは、ランプの言葉 (点灯・点滅・光・ランプ・ついて 等) がある文節か、
      色だけを言った文節 (「緑です」) に限る** (`soundsLikeLampReport`)

    実API (103: 1色目を押した → 2色目で押し間違え → 「ブザーが鳴りましたが大丈夫?」。5キャラ × 2回):
    10/10 が「列は最初に戻った。まず青のボタンから押して」と1色目から押し直させた。
    回帰は `TestButtonReportIsNotLampReport`。

157. **押し間違えで最初に戻るステージの洗い出し** (要望で決定。2026-09-27):

    決定156 のあと、「ほかの押し間違えると最初からになるステージも問題ないか」を洗い出した。
    ステージ定義とファーム (game_task.cc・push_seq_input.h・color_match_game.h) を突き合わせた:

    | ステージ | 押し間違えたとき (ファーム) | 対応 |
    |---|---|---|
    | 103 コール&レスポンス | ブザー+5秒減。**列は最初に戻る** | 決定156 |
    | 201 復唱 | ブザー+5秒減。**列は最初に戻る** | 決定156 (同じ仕組み) |
    | 204 色合わせ | ブザー+5秒減。**最初には戻らない**。今の色を出したまま待ち、正しい色で続きから | 今回 |
    | 102・304 押さえたまま切る | 離しても罰は無い。押さえずに切ると手順未達で爆発 | 対象外 |
    | 206・209・208・303 など | 危険位置・タイミング外は即爆発 | 対象外 |

    - **204**: `procedure` に「ブザーが鳴っても最初には戻っていない。今光っている色と同じボタンを
      押せば続きから進む。回数を数え直させたり、最初から押し直させたりしない」を足した。
      103・201 の対応に引かれて「最初から」と言い出すのを防ぐ。実API (「押し間違えてブザーが
      鳴りました。最初からですか?」5キャラ × 2回): 10/10 が「最初には戻っていない。同じ色の
      ボタンを押せば続きから」。ヒバリが1回「同じ**緑**のボタン」と、最初に聞いた色のままだと
      決めつけた
    - **201**: 103 と同じ仕組みで扱えることを確かめた。ただし**押し間違えのあと黙っている
      プレイヤーへの無応答の声掛け**では、無応答の指示 (状況を尋ねる) が勝ち、10/10 が
      「どこまで進んだ?」と尋ねるだけだった。`PushSeqReset` があるときは**発話トリガーの指示
      そのものに**押し直しの一文 (`pushSeqResetInstruction`) を足すようにして 9/10。残る1回は
      フクロウの「馬鹿野郎、慌てるなと言ったろ。もう一度確認しろ」(押し直しを言わず、責めた)

158. **203 の briefing / answer を「知らない側」の書き方にする** (シミュレーション結果・要望で決定。2026-09-27):

    フクロウの全ステージシミュレーションで、203 ブループリントの「どの端子の線を切りますか。
    色で教えてください」に「**色教えろとは言えん**、俺からは見えんからな」と返した
    (ユーザー判断「まずい」)。同じ場面を12回回すと、「色は教えられん」「色は言えん」が 5/12。
    決定134 で `procedure` の断り方は「見えない → 資料で分かる → 端子番号」の順に直してあったが、
    ほかの場所に**伏せる姿勢**が残っていた:

    - briefing の末尾「ナビゲーターは両系統の端子番号を並べて伝える。**色は言わない**」
    - answer の「**プレイヤーに伝えてよいのは**端子番号と読み方で、色名は**最後まで口に出さない**」

    `procedure` の1番目に「言えない・教えられない…のように伏せていると聞こえる始め方をしない」と
    足した段階では 6/12 と変わらなかった。禁じたい言い回しを**引用していた** (ADR N-32)。

    直したこと: briefing を「ナビゲーターは回路図を持っていないので、端子が何色の線につながって
    いるかは知らない」、answer を「あなたが知っているのは端子番号と読み方の手順だけ。回路図は
    プレイヤーの手元にしか無く、何色に着くかは分からない」、`procedure` の1番目を「自分には見えない・
    分からないという事実から言い始める」 (引用なし) に書き直した。フクロウで 24回中3回
    (1/12・2/12) まで減った。ほかのステージの briefing / answer に同じ書き方は無かった。

159. **手順の確認には「肯定/否定 → 手順の言い直し」の順で答える** (ユーザー要望で決定。2026-09-27):

    101 で「ランプが1つ光っています。この色の線を切ればいいですか」に、フクロウが
    「光っているランプだな、了解。その色の線を切れ」と返した。**報告として復唱し「了解」で
    受けていて、問いに答えていない**。ユーザー案は「そうだ、光っているランプと同じ色の線を切れ」。

    - `prompt.toml` に「手順の確認を尋ねられたら、まず肯定か否定の一言、そのあと手順どおりに
      言い直す」を足した段階: フクロウは直ったが、アオサギ「その線ですね。切ってください」、
      ヒバリ「その線を切って大丈夫です」と**指し示す言葉で済ませる**・結果を請け合う返答が残り、
      「色を教えてください」と尋ね返すものもあった (20回中、手順の言い方で言い直したのは3回)。
    - **サーバーが確認の問いを判定する** (`NoteConfirmQuestion`。「〜ばいいか」「〜で合ってるか」の
      形。迷いの言葉を含むものは N-37 の対象なので除く) ようにし、履歴の後ろに答え方のブロックを
      置いて順番で指定した (N-53)。同じ場面で、肯定から始まるのが 20/20、「光っているランプと
      同じ色の線」と言い直したのが 18/20、尋ね返し・請け合い・「了解」は 0。
    - 「肯定か否定の一言」だけだと、**まだ先の手順** (ダイヤル前の「まず線を切ればいいですか」) にも
      「そうだ、まずはダイヤルを0に合わせろ」と**肯定してから別の手順を言う**ものが 10回中4回出た。
      1番目を「今やるべき手順と合っているかを答える。先の手順・進め方に無い手順なら否定する」に
      直して 0/15。先の手順への返答は「違う」「まだ線を切る段階じゃない」または肯定抜きで
      「まずはダイヤルを0に」だった。
    - 残り: 言い直しが「その色の線」に留まるものが 15回中5回 (肯定は先に来ている)。

160. **102 で「1回押せばいいのか」と聞かれたら、否定して「切り終えるまで押し続ける」と伝える** (実運用ログ・ユーザー判断で決定。2026-09-27):

    コンソールで、「ダイヤルを2に合わせ、点滅しているボタンを押しながら点灯している線を切れ」の
    あとに「えっ? 1回押せばいいんですか?」と聞かれ、フクロウが「**押すな、一度押したら終わりだ**。
    点滅しているボタンを押したまま、線を切れ」と返した。「押すな」は押し続ける課題と正反対に
    聞こえる (ユーザー判断「不適切。押し続けることを伝えるべき」)。

    - 同じ場面を回すと「押すな」「一度押したら」は、確認ブロックあり (決定159) で 0/42、
      ブロック無し (決定159 より前のコード) でも 0/15 で、**再現しなかった**。ただしブロック無しでは
      アオサギ「押したままでは切れません」、フクロウ「1回押して離したら爆発する」と**事実と逆・
      誇張の説明**が出た。ブロックありでもフクロウ 12回中、「そうだ、押しながら切れ」と問いを
      **肯定した**ものが1回、「押しっぱなしにしろ」「離すなよ」で**線を切るのが抜けた**ものが3回。
    - `procedure` に条件を足した: 押す回数や「1回押せばいいのか」を聞かれたら、問いは否定し、
      **線を切り終えるまで押し続ける**ことと**押したまま線を切る**ことをひと続きで伝える。
      フクロウ 12/12 が否定から入り、「線を切り終えるまでボタンは押し続けろ」。ほかの4人も 12/12。
    - 残り: フクロウ12回中1回「離すと切れるぞ」(正しくは切れない)。

161. **フクロウは叱るときも相手をけなさない** (ユーザー判断で決定。2026-09-27):

    ユーザー判断「フクロウの口が悪すぎる。馬鹿野郎とかは言わないように」。これまでも 303 の
    差し戻し (決定107 前後)・押し間違えの声掛け (決定157)・切断の報告で「馬鹿野郎」が出ていた。
    **出どころはキャラシートの「誤操作」の台詞例**が「馬鹿野郎、慌てるなと言ったろ」だったこと
    (例文は出力を固定する。ADR N-29)。

    - 台詞例を「慌てるな、死ぬぞ。もう一度確認しろ」に差し替え、【性格】に「叱るときは、危険を
      『死ぬぞ』の一言で告げ、すぐ手順へ戻す。相手を責める言葉は足さない。口は重いが、相手は
      守るべき仲間として扱う」を足した。**禁じる語は引用しない** (N-32)。
    - 先に「罵る言葉・見下す呼び方・怒鳴りつける言い方・問い詰める反語は使わない」と**禁止を並べた**
      版では、挑発的な発話 (102「面倒なので適当に線を切っちゃっていいですか」) に8回中2回
      「馬鹿なことを言うな、死にたいのか」「ふざけるな」が出た。**してほしいこと (一言で警告して
      手順へ戻す) で書き直して**、罵倒語・「死にたいのか」は 0/8。残るのは「冗談を言うな、死ぬぞ」
      「ふざけている場合か」程度の叱り方 (8回中3回)。
    - 押し間違え (103)・数字を忘れた (101) の場面は 0/16。全ステージのシミュレーション (約110発話) と
      終幕のシミュレーションでも罵倒語は 0。爆発の場面の「くそっ」(状況への悪態) は残した。

162. **紙資料は番号で呼び、開発側の呼び名 (回路図・対照表) をナビに持たせない** (ユーザー判断で決定。2026-09-30):

    203 でナビが「回路図」と言った。ユーザー判断「回路図のような、という話題は出したが、
    ナビゲーターは知らないようにしてほしい。ただの資料3を見る、で事足りる」。あわせて
    資料を使う他のステージで、番号を言わずに開発側の名前で呼ぶところが無いかを洗った。

    - 203 の briefing / answer / procedure に「回路図」が7か所あり、「全灯は回路図を見ろという
      合図だと応じ、資料3に回路図があることを伝える」と指示していた。モズ「全灯は回路図の合図や」。
      すべて `${sheet_circuit}` (資料3) に置き換え、「番号だけで指す」とした。
    - 202・302 の briefing「(モールス対照表)」→「の表のモールス信号」、209 の answer「対照表も
      持っていない」→「資料4も持っていない」。
    - ログでフクロウが「**シートの対照表で読んでくれ**」と番号抜きで呼んでいた。出どころの一つは
      **台本のプレイヤー**で、「シートの対照表で読んでみます」「回路図シートを見ています」と
      開発側の呼び名で話していた (ナビが写す)。実際のプレイヤーは紙の「資料N」しか知らないので、
      台本を直した。
    - `prompt.toml` に共通ルール「紙資料は、いつも資料番号で呼ぶ。資料を見るよう促すときは
      2回目以降も番号で指す。見出しや列の名前は番号のあとなら使ってよい。同じ資料の中で次の表へ
      移るときは進め方に従って見出しで指す (301)」を足した。
    - シミュレーションに `sheet_name` 検査 (回路図・対照表・シート) を足した。
    - 202・203・209・301・302・305 をフクロウ・モズ・アオサギで回して、開発側の呼び名は 108発話中 0
      (直す前は 3件)。番号なしで残るのは 301 の次の表を見出しで指すもの (紙の見出しなので可) と、
      モズの「資料の解除位置を見て」1件。

163. **プレイヤーに「Core」「シリアル銘板」を言わせない。203 は「外装にある製造番号」と案内する** (実運用ログ・ユーザー判断で決定。2026-09-30):
    - 実運用ログ (203) でフクロウが「シリアルが奇数ならX2」と言い、聞き返されると「Coreの外装にある銘板」
      「外装にある製造番号のプレート」と言い換えた。プレイヤーは「シリアルって?」「銘板って?」と2回続けて聞き返した。
      「Core」「CoreID」「銘板」は制作・運営側の呼び名で、プレイヤーは知らない。
    - 203 の `briefing`・`answer`・`procedure` を「外装にある製造番号の下1桁」に改めた。迷われたら
      「4桁のシリアルナンバー」と言い換えてよい (ユーザー判断)。「銘板」「ID」は使わせない。
    - `prompt.toml` の共通ルールへ「制作側の用語を言わない。機器を指すときは『その機器』『この装置』」を足した。
      **禁止語そのものは書かない** (列挙すると手本になる。決定32。最初に書いた版は「Core・コア・CoreID・銘板」を
      並べていて、プロンプトに Core を入れていた)。
      `session_ready` の「CoreID」も「機器の管理番号」へ改めた (マネージャー向けの発話だが語が写るため)。
    - 205 の `answer` にあった「Core向けJSON」も削った (プロンプトに載る)。
    - 台本側の呼び名は 決定162 と同じく検査対象。コメント (`#`) はプロンプトに載らないので触っていない。

164. **書き起こし・発話生成は再試行せず、失敗したら事前収録の聞き直しを流す** (ユーザー判断で決定。2026-09-30):
    - 従来は 429 だけ1回再試行し (ADR G-7 旧)、502 などは再試行されず、失敗すれば無音のまま20秒以上待たされた。
      提案: クライアントのタイムアウトを5秒にして1回撃ち直す → **撃ち直さず、聞き直しを流す**へ。
      「まず 5秒で先に入れて様子を見る」(遅延分布は未確認) と、リトライ回数・タイムアウトを
      API ごとに別々に設定ファイルで調整できるようにすることを併せて決めた。
    - 既定: 書き起こし 8秒×1・発話生成 5秒×1・TTS 10秒×1。**TTS も再試行しない** (ユーザー判断。
      初回案は据え置きの 3回だったが、外すと最悪30秒の無音になるため 1回へ)。回数は「初回を含む試行回数」
      (1 = 再試行0回)。起動ログ `[boot] gemini limits:` で確認できる。
    - **聞き直しはプレイヤーが話した直後の失敗にだけ**流す。イベント起点・無応答の声掛け・開始の発話が
      失敗して「もう一度お願いします」と言うと、話していない相手を混乱させる。
    - 5キャラ×2本 (`assets/reask/<id>_<n>.ogg`)。台詞はキャラ定義の `reask_lines` が正本で、
      `crosstalk-gen` の `reask` カテゴリと一致をテストで検査する。**音声は生成済み**
      (10本。`go run . -category reask -out ../game-server/assets`)。生成時、場面の指示
      (「聞き取れず頼む一言・申し訳なさそうに」) を context に足すとモズ2本とツグミ1本が
      400 (INVALID_ARGUMENT) を返し続けたので、context は `tts_style` だけにした。実音声の聞こえ方は未確認。
    - **見つけて直した副作用**: 発話生成は成功したが TTS が失敗して捨てられた場合、誤った報告の回数などの
      印が戻らず、プレイヤーの言い直しが同じ誤りの2回目に数えられた (不正解の線への誘導が早まる)。
      TTS の捨てを `errSpeechDropped` で返し、印を戻すようにした。開始・イベント・声掛けでは従来どおり無言で続行。
    - 会話ログへ聞き直しの台詞を残す (次の生成が聞き直したことを知るため)。
    - 未確認: 実運用でのタイムアウト値の妥当性 (聞き直しが多すぎれば秒数を延ばす)。実音声での聞こえ方。
    - 追記: TTS も再試行しない (10秒×1) に変えた。聞き直しの音声は生成済み。

165. **終幕 (解除成功・爆発) は生成せず、事前収録の音声をランダムに流す** (ユーザー判断で決定。2026-10-02):
    - 発端: 失敗・終了時の音声が遅れるという指摘。終幕は reply 生成 + TTS で十数秒かかっていた。
      提案: 聞き直し (決定164) と同じく事前生成にする。**ユーザーが生成発話の廃止まで決めた**
      (「事前生成にしたので、生成発話は廃止にしましょう」)。
    - 5キャラ × 解除成功3 + 爆発3 = 30本。台詞は Claude で下書きしてユーザーが1本ずつ直した
      (フクロウ成功の硬い日本語、ヒバリ失敗・成功の黒幕の出し方、アオサギ成功の「少し驚いています」→
      「ご無事で、何よりです」、フクロウ失敗2の「どうした! ……聞こえているなら応答しろ」など)。
      経緯は `docs/ending_presets_draft.md`。
    - **Gemini に同じ指針で生成させて比較した** (直前の交信なし・各5回。`-ending-no-history`)。
      1本ずつの質は悪くないが**毎回ほぼ同じ形に収束する** (ヒバリ成功は5/5が「やりましたね、無事に止まりました!」、
      失敗は5/5が「あっ、なんでもないです!」で終わる。モズ成功は5/5が飲み食いで締める)。
      3本を人が書き分けるほうが利点が大きいと判断し、Gemini の出力は採用しなかった。
    - **ヒバリの失敗1本目は意図してキャラシートの禁止を外した** (「装置への関与を示す語を言わない」に反して
      素に戻る一言を入れる)。本音を漏らすのは3本中2本までにし、3本目は普通に残念がる。
    - 生成時の失敗: 30本中2本が失敗 (フクロウ成功1は空応答 → 再実行で通った。ツグミ成功2は
      `[warm]` + 「……それじゃ」で 400 → `[calm]` に替えて通った。タグと台詞の組み合わせで決まる)。
    - 実装: `EndingPlayer` (`navigator_ending.go`)。効果音を台詞の前へ連結して1本で送る。
      コンソールモードは会話ログへ台詞だけ残す。台詞の音声が無いキャラクターは効果音だけになる。
    - **生成版は削除した** (ユーザー判断。同日): `prompt.toml` の `defused` / `exploded` トリガー指示と、
      出力ルールの「交信が終わる場面」の例外 (名乗らない・「どうぞ」を付けない。決定46・112)、
      キャラシートの「解除成功」「爆発」の節 (決定47・47b・52・88 ほかの指針)、`directorNotes` の終幕分、
      `speakTTS` の `prefixPCM`、`GeminiNavigator` の `sfxDir`、`TestSimulateEndings`
      (`-ending` フラグ) と、プロンプトの終幕指示を検査していた4テストを消した。
      **消した指針は台詞の中に生きている** (アオサギは「衝撃」「交信途絶」と言い呼びかけない、
      ヒバリは「失敗」を言い本音が漏れる、ツグミは「失敗」+軽い問いかけ+日常の一言、
      モズは言葉が途切れる、フクロウは呼びかけて現場へ入る)。禁止事項は
      `TestEndingLinesOfRealCharacters` が台詞に対して検査する。
      **過去の決定 (46・47・47b・52・88・112 など) は経緯として残す** — 現在の正本は ADR G-9 と各キャラ定義末尾の台詞。
    - **流すのは2秒遅らせる** (ユーザー判断。2026-10-03): 実機で聞くと「すぐ再生されるのでタイミングが悪い」。
      解除成功は `defused` の2秒後、爆発は破裂の2秒後。`exploded` はソレノイド駆動前に届く
      (赤点灯+ブザーで `detonate_delay_ms` = 2000ms ためる) ので、爆発は受信から約4秒後になる。
      履歴の確定は台詞を残したあと (遅らせたぶん確定も遅れるが、`Finished` は終了の瞬間に立てるので
      引き継ぎは遅れない)。
    - 未確認: 実音声の聞こえ方 (効果音との連結の間・ヒバリの切り替わり・モズの声が詰まる演技)。2秒の間の妥当性。

166. **聞き直しに「電波が乱れて途中が聞こえなかった」ノイズ入りの3本目を足した** (ユーザー判断。2026-10-06):
    - 発端: 「API失敗時のプリセット音声に、実際にノイズが入って一部が途切れて聞こえにくいものを各ナビゲーターへ1パターン足したい」。
      提案: **TTS に崩れた台詞を読ませる**か、**生成後に PCM を加工する**か → 加工を採用 (途切れの位置・長さが指定どおりで、
      作り直しても同じ音。TTS は読み上げ位置を返さず、省略記号の多い台詞は 400 を返しやすい)。
    - 台詞は既存2本と**別の文**にした (ユーザー判断)。「だいたい分かるが、本当に一か所だけ聞こえない部分を作る」。
      位置は台詞の「最初の間」(「こちらフクロウ。」のあと) の直後。単語の途中から切れないよう、音の無音から決める
      (`dropout_after_pause`)。見つからなければ生成を止める (黙って素通ししない)。
    - 調整の経緯 (試作のフクロウを聞いてもらいながら):
      1. ノイズ 0.03 + 欠落 → 「全体的にもう少し聞きにくく」。
      2. ノイズ・帯域・**音量のうねり** → ユーザー「FMで聞き取りにくい状況の表現を想定」。**AM のような声の音量の波打ちは FM と違う**ので外し、
         弱い FM の特徴 (高域寄りのヒス・電波が弱い瞬間にノイズが膨らむ・スケルチ) に作り直した。
      3. パチパチ (クラックル) を入れて → ユーザー「パチパチはなくしましょう」。コードごと削除。
      4. ユーザー「声は元と同じくらいの音量が良い。ノイズが入っているのと声がわかるのでバランスが重要」。
         帯域を絞ると声が小さくなり、ノイズが声のピーク比だったため相対的に目立っていた。**声は元の音量へ戻し、
         ノイズは声との比 (`snr_db`) で指定する**形にした (10dB = ノイズは目立つが言葉ははっきり)。
         実測が指定より 6dB 悪い誤り (ノイズの実効値の計算が2倍ずれ) をテストで見つけて直した。
    - 全員同じ設定 (`snr_db = 10, noise_swell = 1, band_limit = true, dropout_ms = 450, dropout_after_pause = 1`)。
      台詞はキャラごとに言い回しを変えた (アオサギは「音声が欠けました」・ヒバリは「ザーザーして」・
      ツグミは「あれ、ごめん」・モズは「電波が悪うて」)。
    - 生成時の失敗: ツグミだけ 400 が続いた (「話してもらえるかな」→「話してくれるかな」に替えて通る。
      ツグミは終幕のときも `[warm]` で 400 だった。台詞の組み合わせで決まり、意味は変わらない言い換えで通る)。
    - **既存の聞き直し2本 (各キャラの1・2本目) にも同じ加工を掛けた** (ユーザー判断。同日「他のreaskのパターンも同じ対応を行なって」)。
      これで聞き直し15本はすべて加工済みで、**加工なしの音声は残っていない** (作り直す前の音声は退避していない。
      戻すなら `degrade` の行を消して `-force` で再生成する)。台詞は変えていない (1・2本目の台詞は「よく聞き取れなかった」
      「雑音で聞こえなかった」で、聞こえにくさと矛盾しない)。欠落は最初の間 (名乗りのあと) の直後なので、
      「こちらフクロウ。」のあとの「よく聞き取」あたりが消える。ツグミ1本目は 400 が1回出て再実行で通った。
    - 未確認: 実機の無線越しでの聞こえ方 (SN比・欠落の長さ)。TTS の間の取り方で欠落位置が生成のたびにずれる。

167. **203 ブループリントの資料3は、端子から出る「太い線をたどる」だけにした** (ユーザー判断。2026-10-06):
    - 発端: 「資料3の図を簡略化し、太線と細線を示す先ではなく太線を辿れば良い感じにした。変更可能か」。
      従来は端子から**点線と太い線の2本**が出ていて、**両方たどると同じ色に着く** (答え合わせを兼ねた二重表現)。
      ナビは「点線と太い線の両方をたどり、同じ色の線を切れ」と言っていた。
    - 変更: ステージ定義 `203_blueprint.toml` の `answer` と `procedure` から点線・2本・「両方たどる」「同じ色に着く」を消し、
      **「その端子番号から出ている太い線をたどる → たどった先の色の線を切る」** に改めた。
      点線・細線には触れない (図でどう描かれているかはナビの知識に入れない)。
      紙の説明 (`docs/printed_materials.md` §4.1) も揃えた。実装 (抽選・端子対応・X/Y の2系統) は変わらない。
    - 失うもの: 二重表現による答え合わせ (取り違えたときに気づける) は無くなる。難度は下がる方向だが、
      203 は normal のままにする (系統の選択が主な工程で、引く工程自体は1段。puzzle_stage_ideas の難易度表)。
    - 未確認: 刷り直した紙の図と文面が合っているか (実物を見て確認)。実APIでのナビの言い方 (203 の台本の再実行)。

167. **誤った報告の判定は、光り方を「その色に付いた言い方」だけで読む** (実機のテストプレイで発覚。2026-10-07):
    - 症状: 102 で正しい報告「青が点滅して白が光っています」(青=点滅・白=点灯) をしたのに聞き返され、
      同じ報告をすると「押しながら切る」と**不正解の線**へ誘導された。
    - 原因: `lampReportClaims` が光り方を**文節全体**から読んでいた。区切り (「、」「。」) の無い1文節に
      色が2つあると、「点滅」が青にも白にも付き、点灯が正しい白が「白が点滅」と判定された
      (`checkLampReport` の誤判定 → 1回目は確かめ直し、同じ誤りの繰り返しで不正解の線。N-9b)。
      再現は決定的で、ナビの揺れではない。
    - 修正: 色が2つ以上ある文節では、**色の直後の「が」「は」から次の色までの区間**だけをその色の光り方とみなす。
      光り方が色の前に来る言い方 (「点滅している青と点灯している白」) は読み取れないので、色だけを照合する
      (**取りこぼしても誤りにはしない側へ倒す**。誤判定は不正解の線への誘導になり、爆発につながるため)。
      色が1つの文節は従来どおり文節全体で読む。同じ色が複数回出ても区間を正しく切る。
    - 検証: `TestLampReportReadsStatePerColor` (正しい8通りを誤りにしない・取り違えは見つける)。
      102 のシミュレーションも通った (フクロウ、OK)。

168. **第一声は開始前に生成し、Core のブザーに合わせて流す** (相談で決定。2026-10-09):
    - 課題: ブザーのあと第一声の生成 + TTS が終わるまで空白ができる。生成が失敗するとゲームだけが進み無言になる。
    - 決定: 生成 + TTS を `session_start` の前に済ませる (`Prepare`)。`session_ready` の発話がログに載ったあとに始めるので、
      プロンプトの履歴は従来と同じ (第一声は「改めて名乗る」)。`session_accepted` を合図に再生 (`Play`)。
      **プリセットにはしない** (動作確認を兼ねるため)。用意できなければ開始しない (ADR P-12)。
    - プロンプト・トリガー指示は変えていない。残り時間は開始前なので満了値で、`announceUrgent` は立たない。
    - 未確認: 実機でのブザーと声の間隔、生成が猶予 (5秒) 内に収まる頻度。最大10秒の追加待ち (`firstSpeechMaxWait`) の妥当性。

<!-- EOF -->
