ayumu-bekki/radio-terror/app/core-system/main/gpio_input_watch_task.h

#ifndef GPIO_INPUT_WATCH_TASK_H_
#define GPIO_INPUT_WATCH_TASK_H_
// (C)2024 bekki.jp
// GPIO input watch task

// Include ----------------------
#include <driver/gpio.h>
#include <freertos/FreeRTOS.h>

#include <functional>
#include <vector>

#include "gptimer.h"
#include "logger.h"
#include "message_queue.h"
#include "task.h"

class GpioInputWatchTask final : public Task {
 public:
  static constexpr std::string_view TASK_NAME = "GpioInputWatchTask";
  static constexpr int32_t PRIORITY = Task::PRIORITY_LOW;
  static constexpr int32_t CORE_ID = PRO_CPU_NUM;

 private:
  static constexpr int32_t EDGE_COUNTER = 3;

 public:
  enum GpioPullUpDown {
    NONE,
    PULL_UP_REGISTOR_ENABLE,
    PULL_DOWN_REGISTOR_ENABLE,
  };

  class GpioInfo {
   public:
    GpioInfo(gpio_num_t gpio_no, std::function<void()> on_up,
             std::function<void()> on_down)
        : gpio_no_(gpio_no),
          cnt_(-EDGE_COUNTER - 1),
          on_up_(on_up),
          on_down_(on_down) {}

    gpio_num_t GetGpioNo() const { return gpio_no_; }

    void Check() {
      if (gpio_get_level(gpio_no_) == 0) {
        if (cnt_ < 0) {
          cnt_ = 0;
        } else if (cnt_ <= EDGE_COUNTER) {
          ++cnt_;
          if (EDGE_COUNTER == cnt_) {
            if (on_up_) {
              on_up_();
            }
          }
        }
      } else {
        if (0 < cnt_) {
          cnt_ = 0;
        } else if (-EDGE_COUNTER <= cnt_) {
          --cnt_;
          if (-EDGE_COUNTER == cnt_) {
            if (on_down_) {
              on_down_();
            }
          }
        }
      }
    }

   private:
    gpio_num_t gpio_no_;
    int32_t cnt_;
    std::function<void()> on_up_;
    std::function<void()> on_down_;
  };

 public:
  GpioInputWatchTask()
      : Task(std::string(TASK_NAME).c_str(), PRIORITY, CORE_ID),
        message_queue_(),
        gptimer_(),
        gpio_list_() {
    // Create MessageQueue
    constexpr int32_t MESSAGE_QUEUE_SIZE = 10;
    if (!message_queue_.Create(MESSAGE_QUEUE_SIZE)) {
      ESP_LOGE(TAG, "Creating queue failed");
    }

    // Create Timer
    constexpr uint32_t GPIO_WATCH_RESOLUTION = 1000000u;  // 1us
    gptimer_.Create(GPIO_WATCH_RESOLUTION, &GpioInputWatchTask::TimerCallback,
                    &message_queue_);
  }

  ~GpioInputWatchTask() {
    gptimer_.Destroy();
    message_queue_.Destroy();
  }

  void Initialize() override {
    ESP_LOGI(TAG, "Start GpioInputWatchTask");
    gpio_install_isr_service(0);
  }

  void Update() override {
    gptimer_.Start(5000);  // 5ms
    int event_type = 0;
    while (true) {
      constexpr int32_t QUEUE_RECEIVE_LIMIT =
          1000 / portTICK_PERIOD_MS;  // 最大待機tick
      if (message_queue_.ReceiveWait(&event_type, QUEUE_RECEIVE_LIMIT)) {
        if (event_type == 1) {
          for (auto&& gpio_info : gpio_list_) {
            gpio_info.Check();
          }
          if (on_poll_) {
            on_poll_();
          }
        }
      }
    }
  }

  /// 毎周期 (5ms) 呼ぶ処理を登録する。
  ///
  /// GpioInfo の on_up_/on_down_ は**レベルが変化した瞬間の1回**しか呼ばれず、
  /// 「LOW が続いている間ずっと処理したい」用途には使えない
  /// (カウンタが飽和して二度と発火しない)。MCP23017 の INTA のように
  /// **読み出すまで LOW に張り付く**信号は、レベルを毎周期見る必要がある。
  void SetPollHandler(std::function<void()> on_poll) {
    on_poll_ = std::move(on_poll);
  }

  void AddMonitor(GpioInfo gpio_info,
                  GpioPullUpDown gpio_pullupdown = GpioPullUpDown::NONE) {
    // Setting GPIO Input
    // 注意:IO34～IO39は内部プルアップ/プルダウン抵抗は無し
    gpio_config_t io_input_conf = {
        .pin_bit_mask = 1ull << gpio_info.GetGpioNo(),
        .mode = GPIO_MODE_INPUT,
        .pull_up_en =
            (gpio_pullupdown == PULL_UP_REGISTOR_ENABLE ? GPIO_PULLUP_ENABLE
                                                        : GPIO_PULLUP_DISABLE),
        .pull_down_en = (gpio_pullupdown == PULL_DOWN_REGISTOR_ENABLE
                             ? GPIO_PULLDOWN_ENABLE
                             : GPIO_PULLDOWN_DISABLE),
        .intr_type = GPIO_INTR_ANYEDGE,
    };
    gpio_config(&io_input_conf);

    gpio_list_.emplace_back(std::move(gpio_info));
  }

 private:
  static bool TimerCallback(gptimer_handle_t timer,
                            const gptimer_alarm_event_data_t* event_data,
                            void* message_queue) {
    MessageQueue<int>* const queue =
        static_cast<MessageQueue<int>*>(message_queue);
    return queue->SendFromISR(1);
  }

 private:
  MessageQueue<int> message_queue_;
  GPTimer gptimer_;
  std::vector<GpioInfo> gpio_list_;
  std::function<void()> on_poll_;
};

#endif  // GPIO_INPUT_WATCH_TASK_H_

// EOF
