ayumu-bekki/radio-terror/app/core-system/main/i2c_util.h

#ifndef I2C_UTIL_H_
#define I2C_UTIL_H_
// ESP32 Epoch Clock
// (C)2021 bekki.jp
// Utilities

// Include ----------------------
#include <driver/gpio.h>
#include <driver/i2c_master.h>

namespace I2CUtil {

/// I2Cマスターバスを初期化する
i2c_master_bus_handle_t InitializeMaster(const i2c_port_t port,
                                         const gpio_num_t sdaPin,
                                         const gpio_num_t sclPin);

}  // namespace I2CUtil

#endif  // I2C_UTIL_H_

// EOF
